m-okada/CPU2908/Schematics/74HC/RevC2/CPU2908C.sch

## KiCad design Schematics/74HC/RevC2/CPU2908C.sch (2020-01-18)

Schematic: CPU2908C.sch

Parts:
C1, C125, C126, C127: 10uF; C_0603_HandSoldering
C2, C3, C4, C5, C6, C7, C8, C9, C10: 0.1uF; C_0402
C124: 47uF; CP_Radial_D8.0mm_P2.50mm
D145, D146, D147, D160, D161: LED_G; LED_0402
J1: Conn_02x20_Odd_Even; Pin_Header_Straight_2x20_Pitch2.54mm
R146, R147, R170, R171, R172, R173, R174: 47K; R_0402
S0, S1: LED_G; LED_0402
U1, U2: 74HC08D; SOIC-14_W3.9mm
U3: TC74VHCT04AFT; TSSOP-14_4.4x5mm_Pitch0.65mm
U4, U7, U9: TC74VHC574F; SOIC-20_W7.5mm
U5, U6, U119: 74HC74; MC74HC74ADG
U8: TC74HC125; SN74HC11D
U117: TC74VHCT541; TSSOP-20_W4.4mm
U121: 74AHC1G32; TSOP-5_1.65x3.05mm_Pitch0.95mm
