m-okada/CPU2908/Schematics/74HC/RevC3/BROM.sch

## KiCad design Schematics/74HC/RevC3/BROM.sch (2020-06-03)

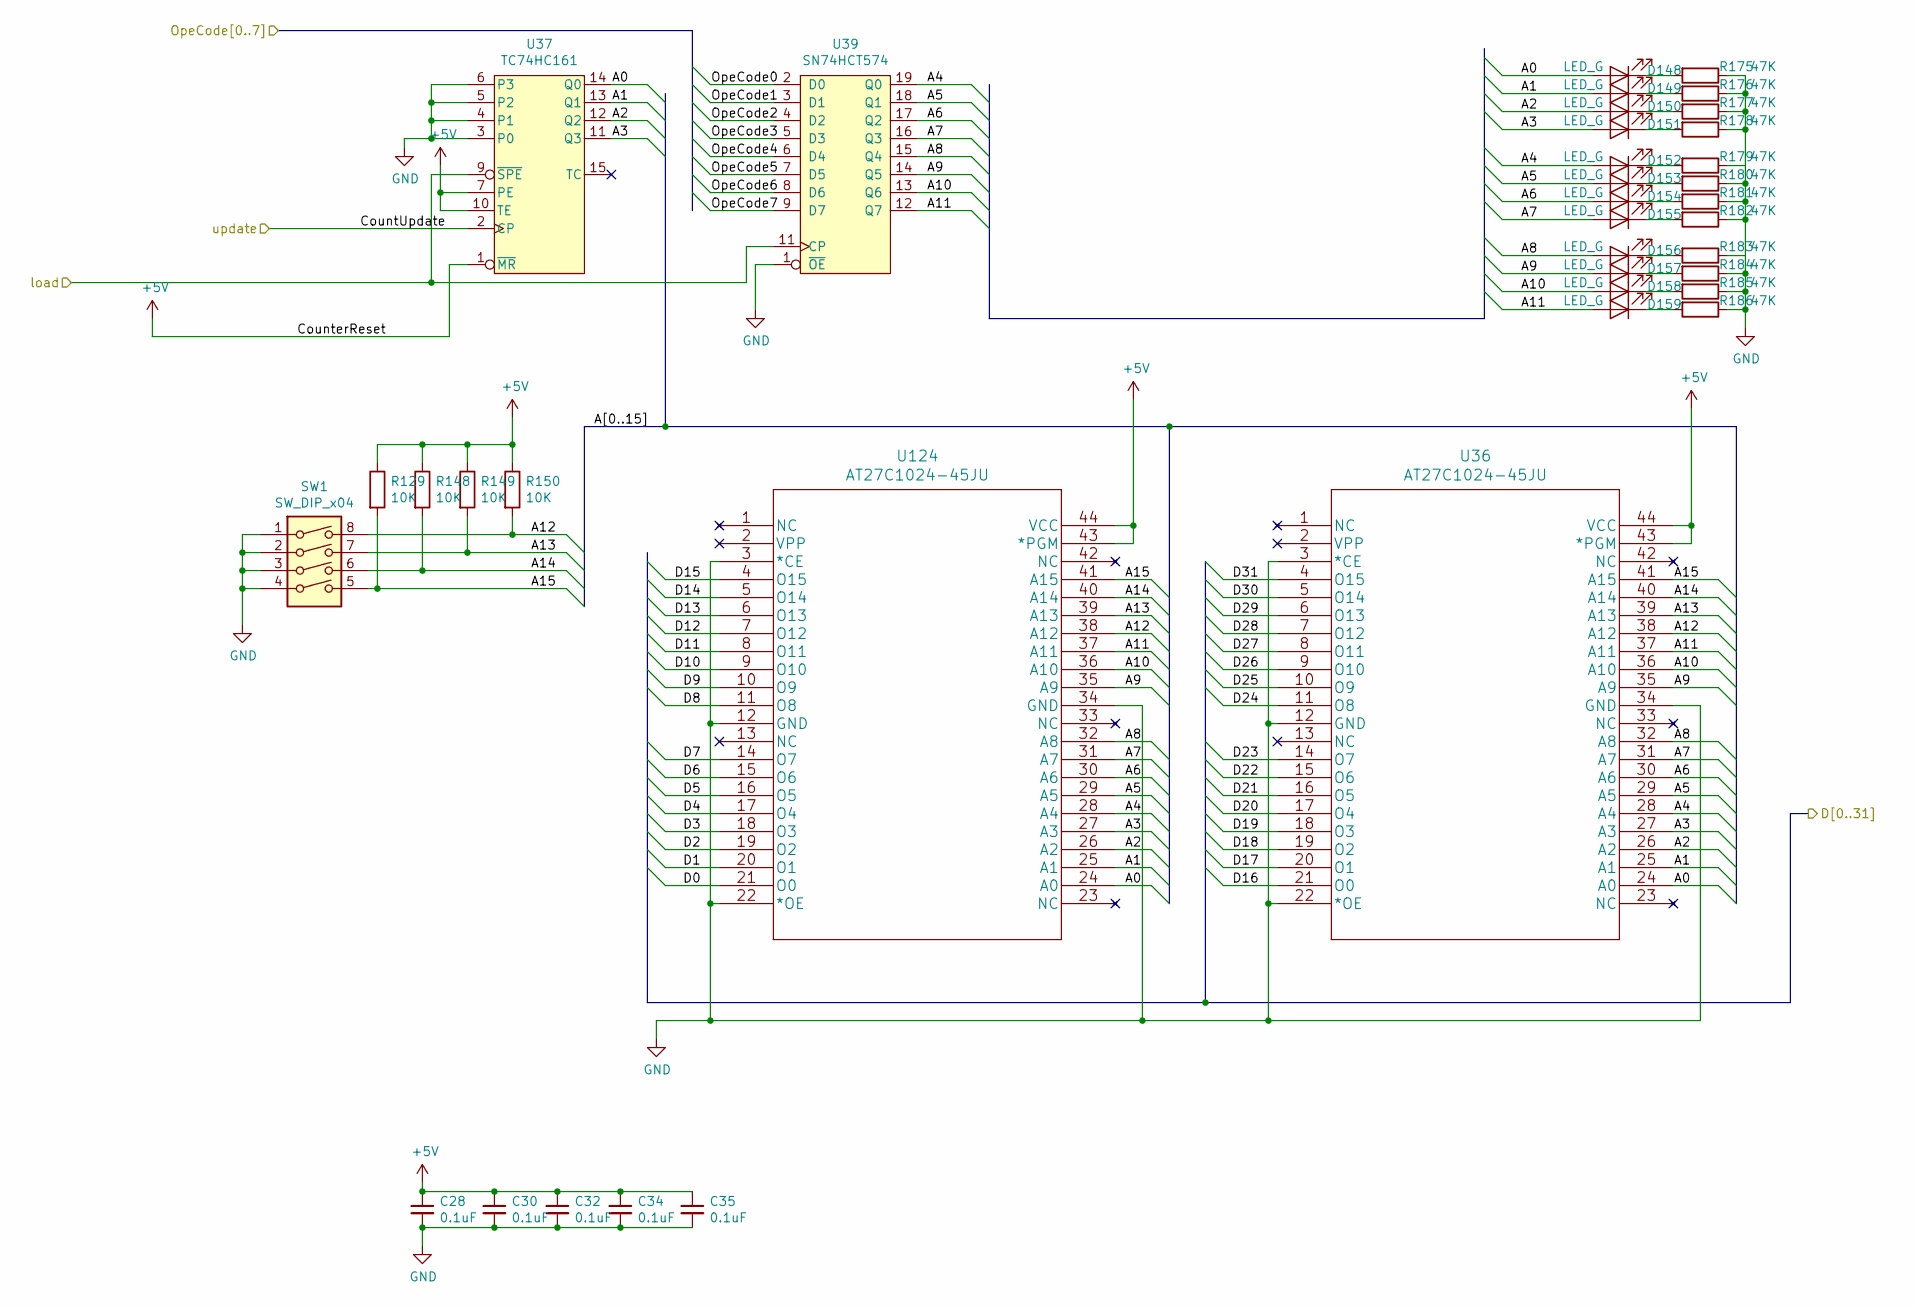
[picture p14: schematic BROM.sch]

Parts:
C28, C30, C32, C34, C35: 0.1uF; C_0402
D148, D149, D150, D151, D152, D153, D154, D155, D156, D157, D158, D159: LED_G; LED_0402
R129, R148, R149, R150: 10K; R_0402
R175, R176, R177, R178, R179, R180, R181, R182, R183, R184, R185, R186: 47K; R_0402
SW1: SW_DIP_x04; SW_DIP_x4_W7.62mm_Slide
U36, U124: AT27C1024-45JU; PLCC44
U37: TC74HC161; SOIC-16_W7.5mm
U39: SN74HCT574; SN74HCT574NSR

Connections:
+5V: C28.1, C30.1, C32.1, C34.1, C35.1, R129.1, R148.1, R149.1, R150.1, U36.43 (*PGM), U36.44 (VCC), U37.1 (~MR), U37.7 (PE), U37.10 (TE), U124.43 (*PGM), U124.44 (VCC)
A0: D148.2 (A), U36.24 (A0), U37.14 (Q0), U124.24 (A0)
A1: D149.2 (A), U36.25 (A1), U37.13 (Q1), U124.25 (A1)
A2: D150.2 (A), U36.26 (A2), U37.12 (Q2), U124.26 (A2)
A3: D151.2 (A), U36.27 (A3), U37.11 (Q3), U124.27 (A3)
A4: D152.2 (A), U36.28 (A4), U39.19 (Q0), U124.28 (A4)
A5: D153.2 (A), U36.29 (A5), U39.18 (Q1), U124.29 (A5)
A6: D154.2 (A), U36.30 (A6), U39.17 (Q2), U124.30 (A6)
A7: D155.2 (A), U36.31 (A7), U39.16 (Q3), U124.31 (A7)
A8: D156.2 (A), U36.32 (A8), U39.15 (Q4), U124.32 (A8)
A9: D157.2 (A), U36.35 (A9), U39.14 (Q5), U124.35 (A9)
A10: D158.2 (A), U36.36 (A10), U39.13 (Q6), U124.36 (A10)
A11: D159.2 (A), U36.37 (A11), U39.12 (Q7), U124.37 (A11)
A12: R150.2, SW1.8, U36.38 (A12), U124.38 (A12)
A13: R149.2, SW1.7, U36.39 (A13), U124.39 (A13)
A14: R148.2, SW1.6, U36.40 (A14), U124.40 (A14)
A15: R129.2, SW1.5, U36.41 (A15), U124.41 (A15)
CountUpdate: U37.2 (CP)
D0: U124.21 (O0)
D1: U124.20 (O1)
D2: U124.19 (O2)
D3: U124.18 (O3)
D4: U124.17 (O4)
D5: U124.16 (O5)
D6: U124.15 (O6)
D7: U124.14 (O7)
D8: U124.11 (O8)
D9: U124.10 (O9)
D10: U124.9 (O10)
D11: U124.8 (O11)
D12: U124.7 (O12)
D13: U124.6 (O13)
D14: U124.5 (O14)
D15: U124.4 (O15)
D16: U36.21 (O0)
D17: U36.20 (O1)
D18: U36.19 (O2)
D19: U36.18 (O3)
D20: U36.17 (O4)
D21: U36.16 (O5)
D22: U36.15 (O6)
D23: U36.14 (O7)
D24: U36.11 (O8)
D25: U36.10 (O9)
D26: U36.9 (O10)
D27: U36.8 (O11)
D28: U36.7 (O12)
D29: U36.6 (O13)
D30: U36.5 (O14)
D31: U36.4 (O15)
GND: C28.2, C30.2, C32.2, C34.2, C35.2, R175.1, R176.1, R177.1, R178.1, R179.1, R180.1, R181.1, R182.1, R183.1, R184.1, R185.1, R186.1, SW1.1, SW1.2, SW1.3, SW1.4, U36.3 (*CE), U36.12 (GND), U36.22 (*OE), U36.34 (GND), U37.3 (P0), U37.4 (P1), U37.5 (P2), U37.6 (P3), U39.1 (~OE), U124.3 (*CE), U124.12 (GND), U124.22 (*OE), U124.34 (GND)
unnamed: D148.1 (K), R175.2
unnamed: D149.1 (K), R176.2
unnamed: D150.1 (K), R177.2
unnamed: D151.1 (K), R178.2
unnamed: D152.1 (K), R179.2
unnamed: D153.1 (K), R180.2
unnamed: D154.1 (K), R181.2
unnamed: D155.1 (K), R182.2
unnamed: D156.1 (K), R183.2
unnamed: D157.1 (K), R184.2
unnamed: D158.1 (K), R185.2
unnamed: D159.1 (K), R186.2
OpeCode0: U39.2 (D0)
OpeCode1: U39.3 (D1)
OpeCode2: U39.4 (D2)
OpeCode3: U39.5 (D3)
OpeCode4: U39.6 (D4)
OpeCode5: U39.7 (D5)
OpeCode6: U39.8 (D6)
OpeCode7: U39.9 (D7)
load: U37.9 (~SPE), U39.11 (CP)
