m-okada/CPU2908/Schematics/74HC/RevC3/CPU2908Executer.sch

## KiCad design Schematics/74HC/RevC3/CPU2908Executer.sch (2020-06-03)

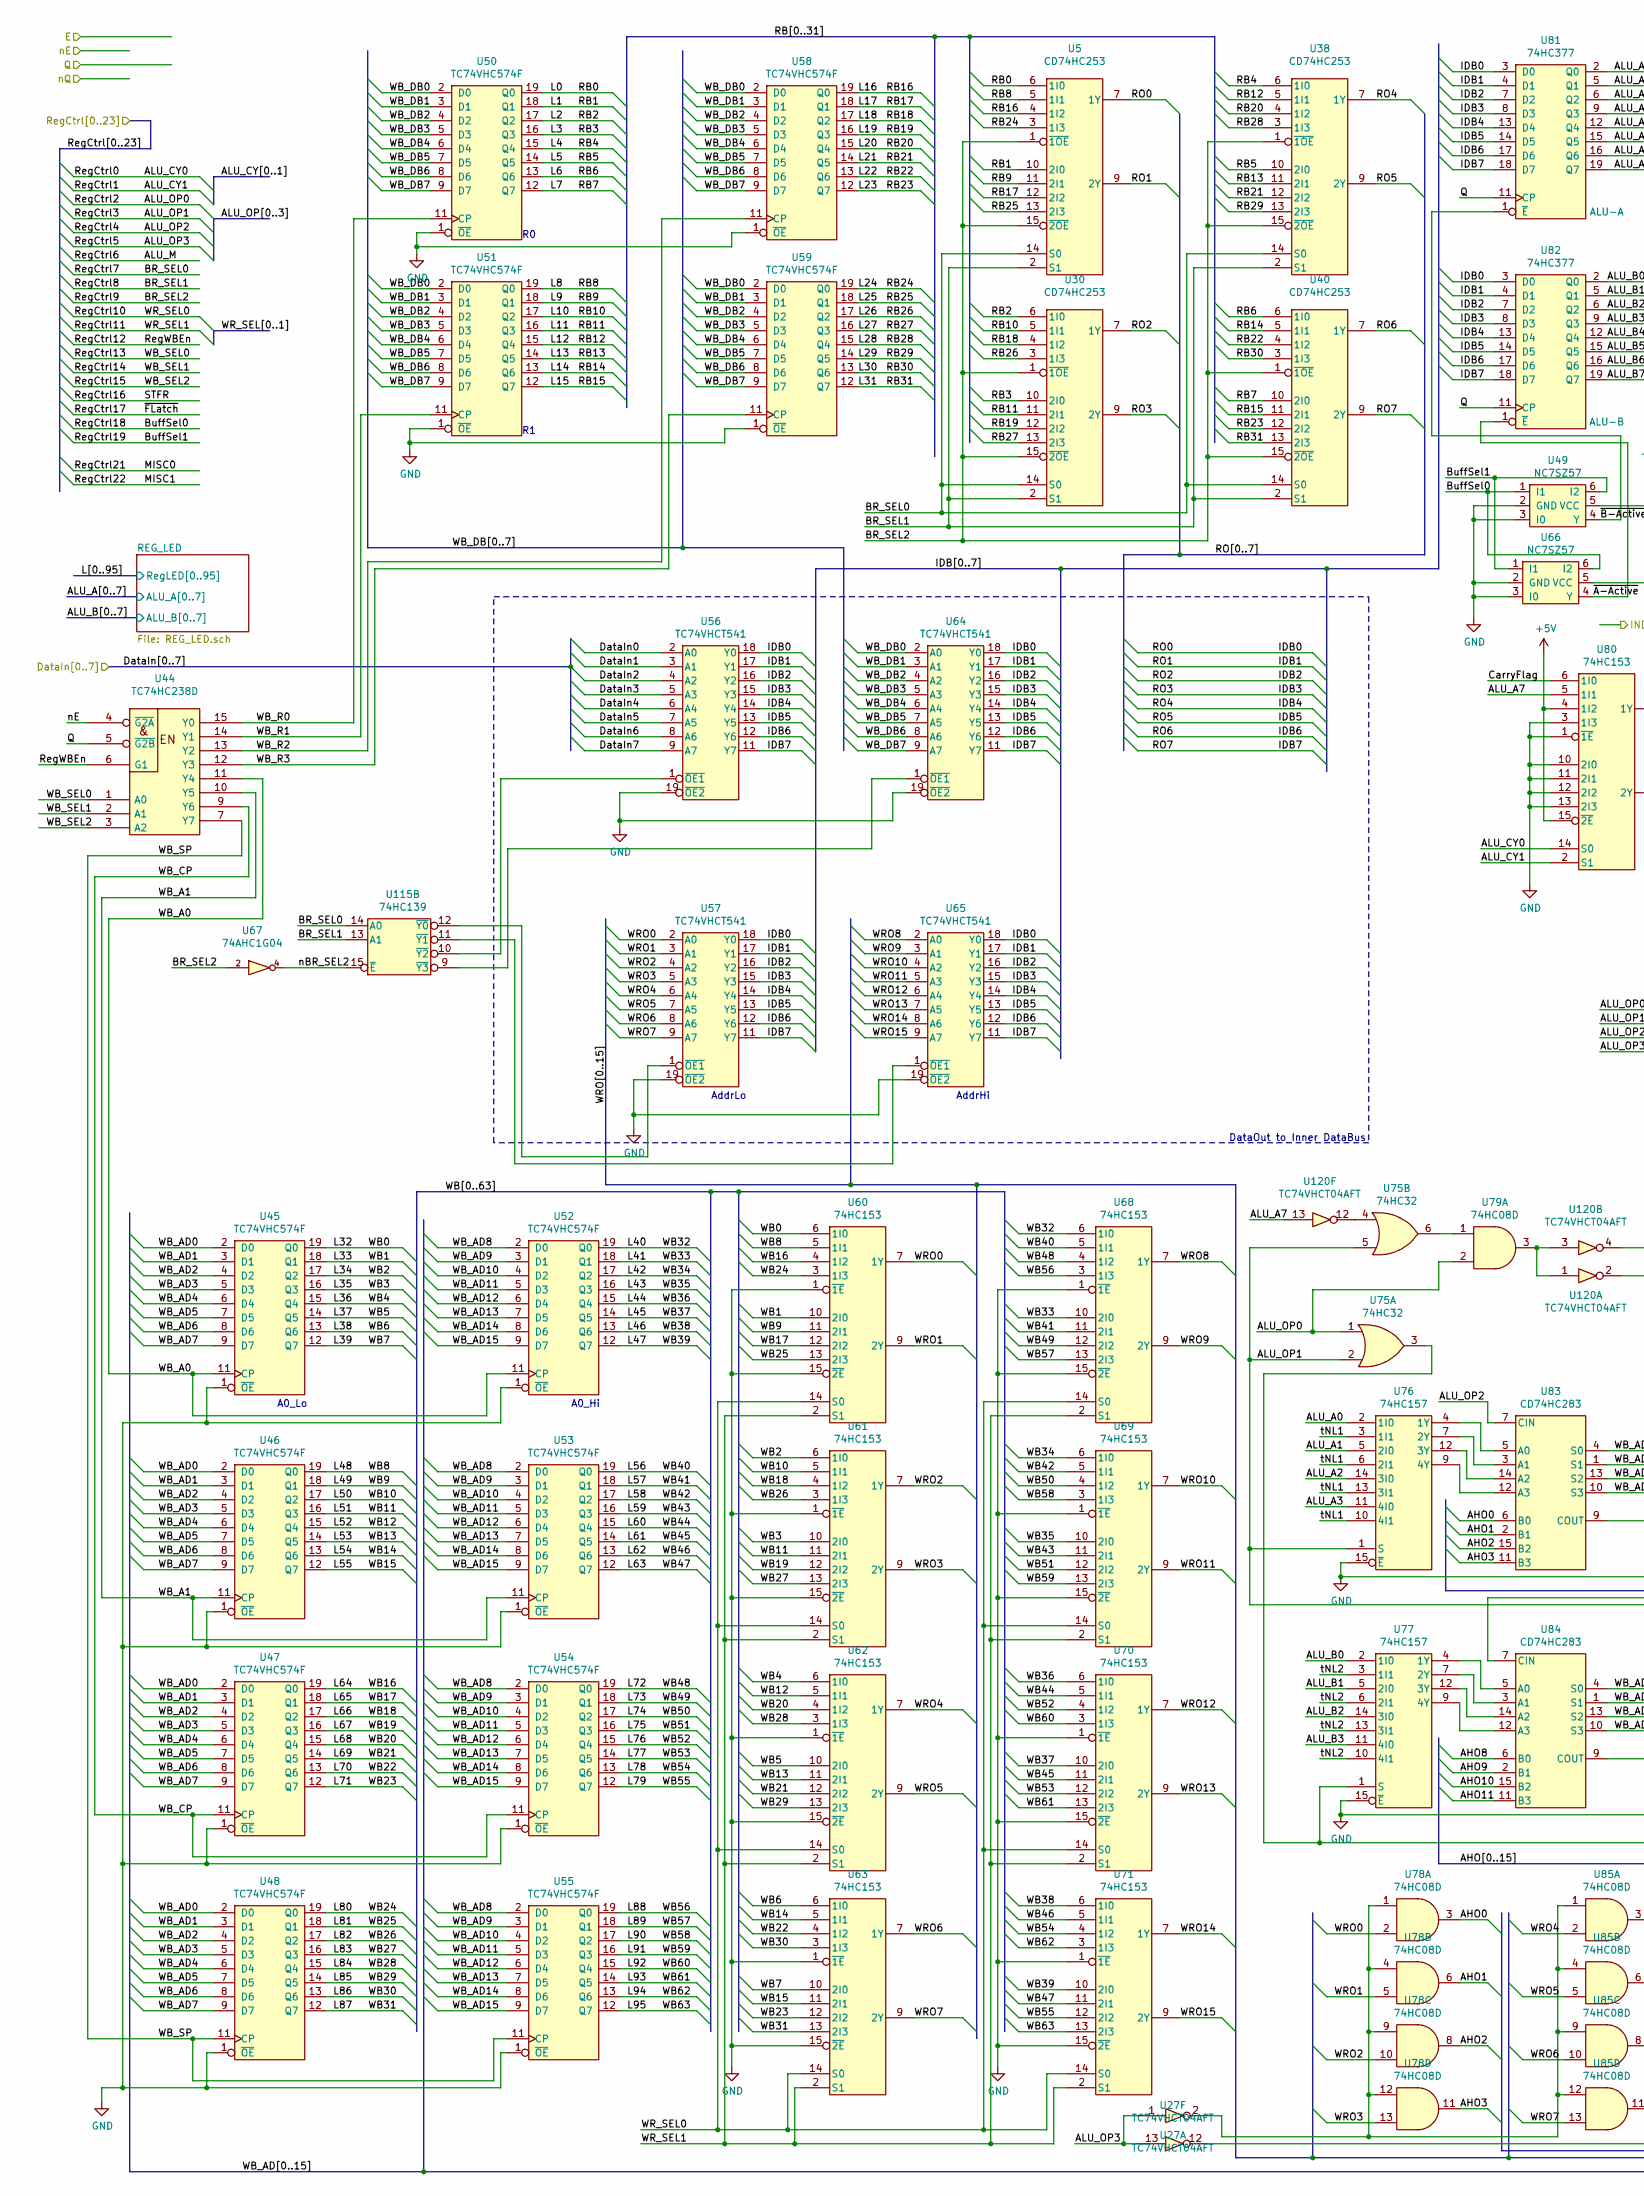
[picture p15: schematic CPU2908Executer.sch, part in row 1, column 1]

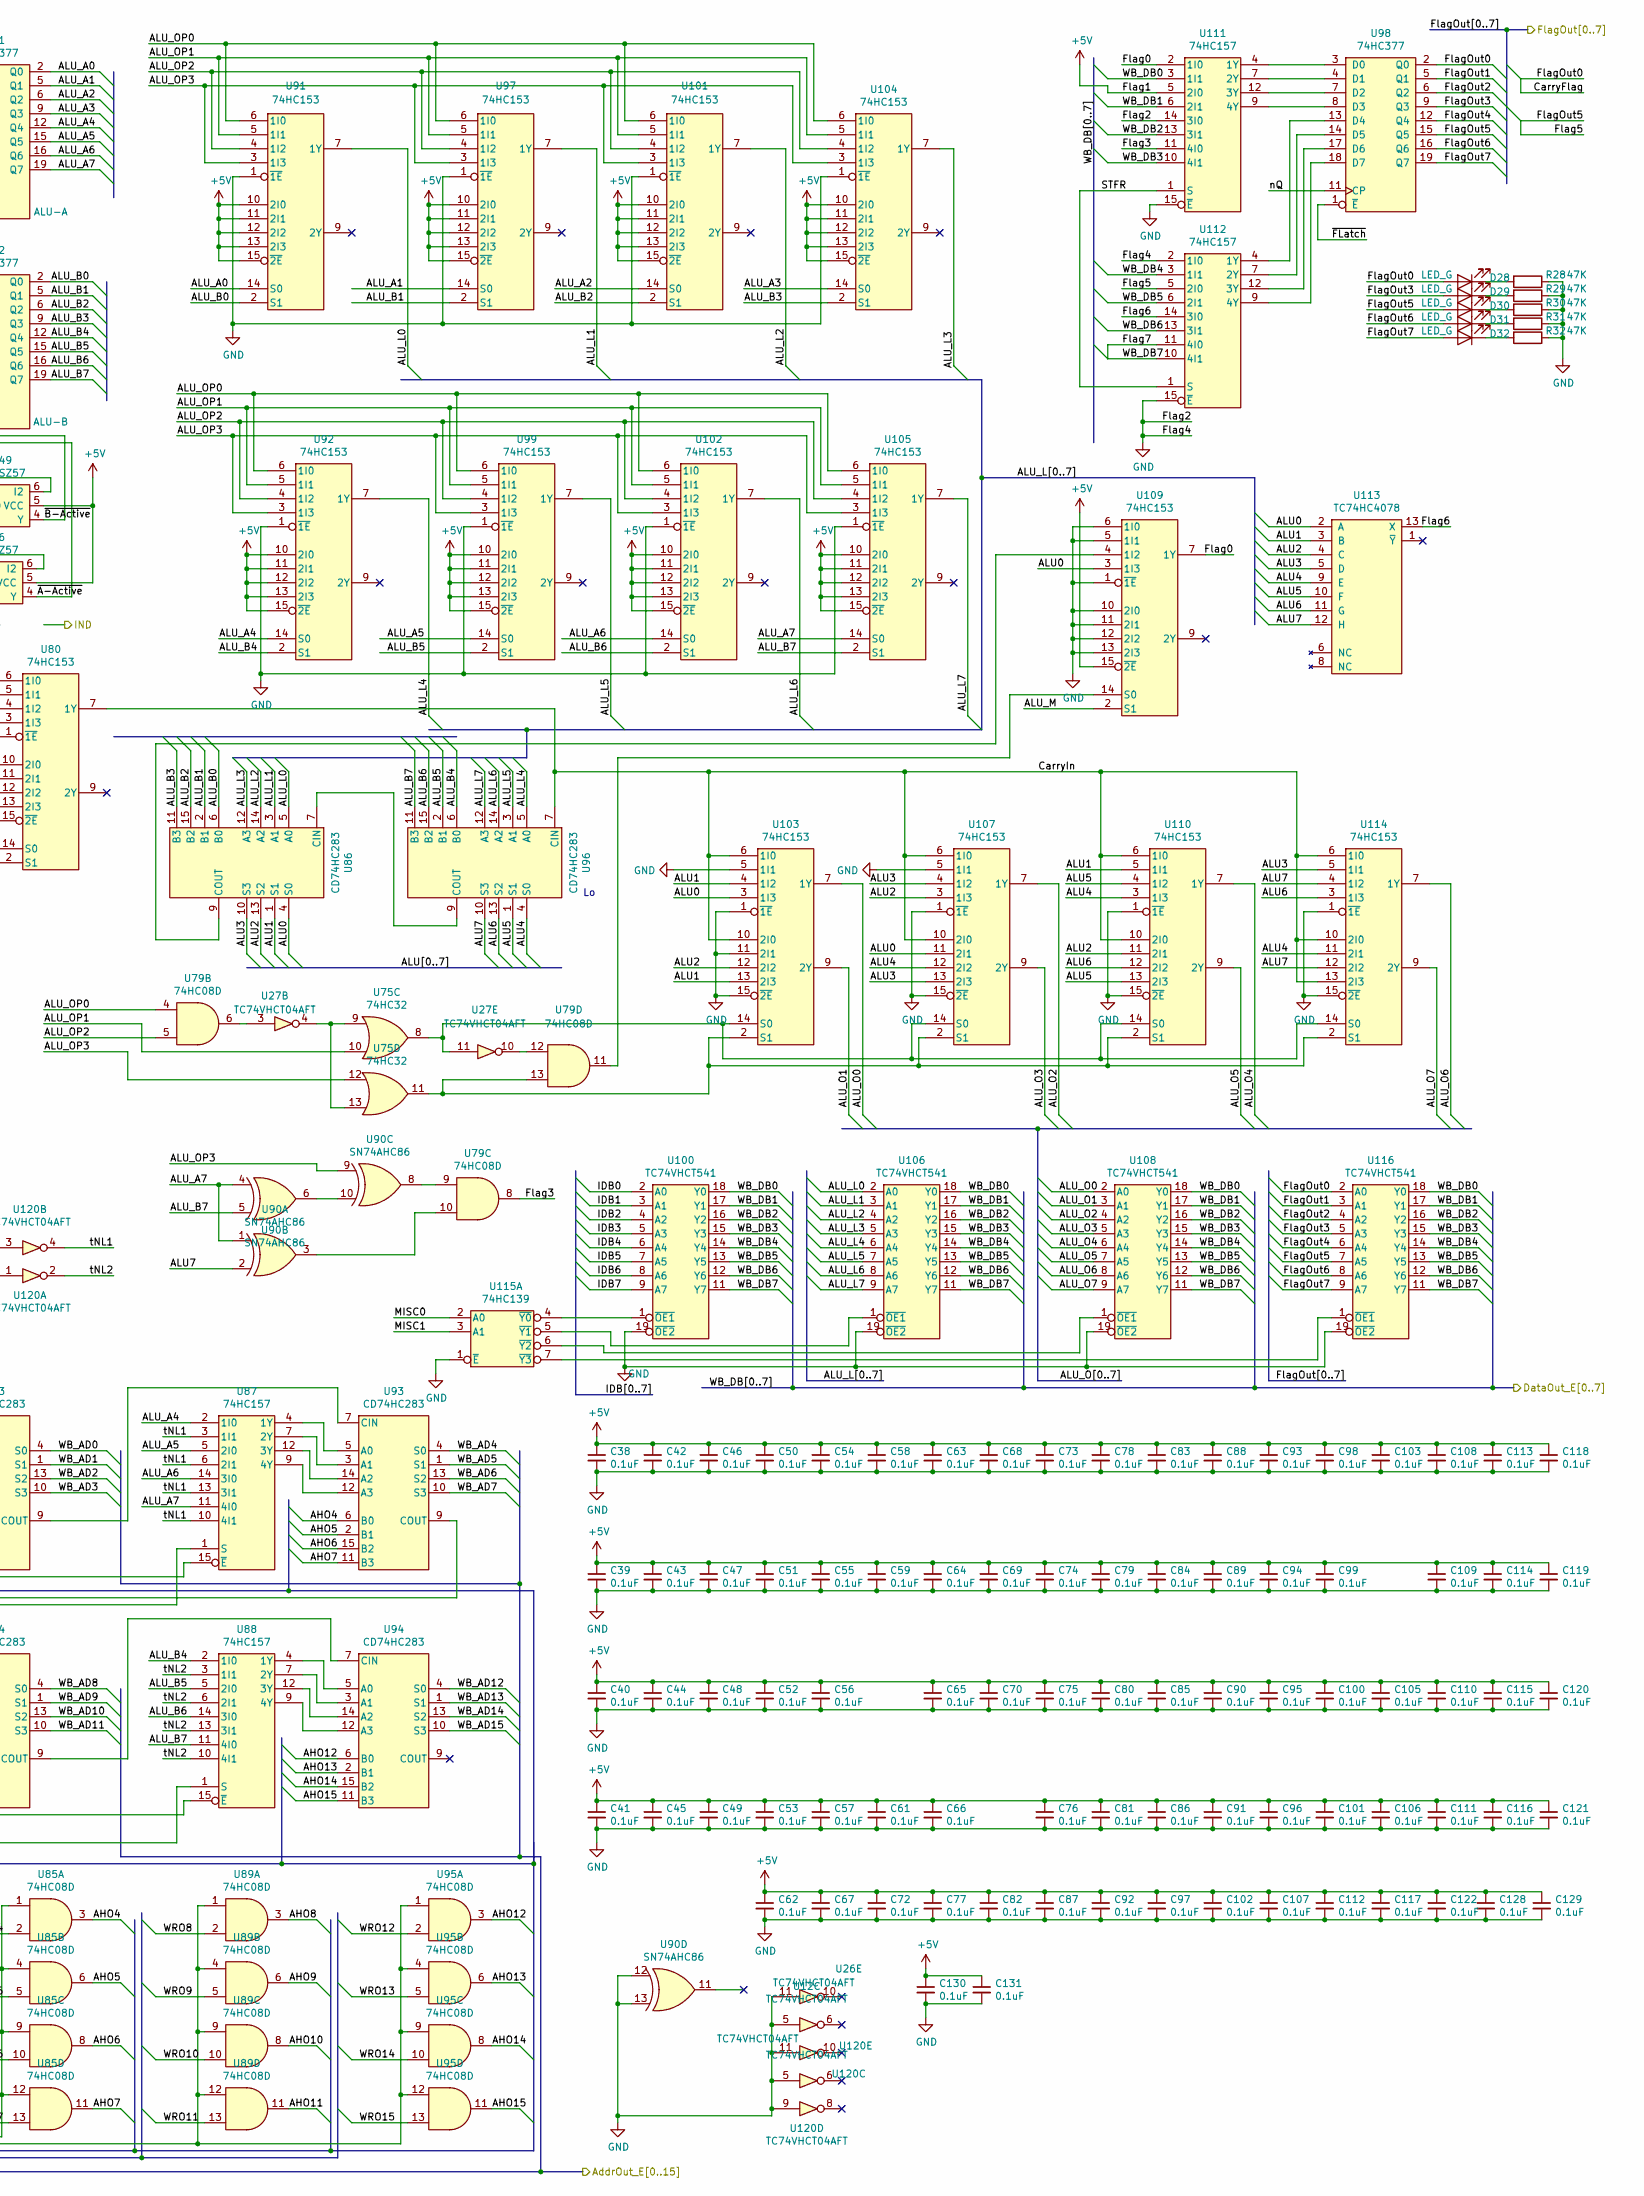
[picture p16: schematic CPU2908Executer.sch, part in row 1, column 2]

Parts:
C38, C39, C40, C41, C42, C43, C44, C45, C46, C47, C48, C49, C50, C51, C52, C53, C54, C55, C56, C57, C58, C59, C61, C62, C63, C64, C65, C66, C67, C68, C69, C70, C72, C73, C74, C75, C76, C77, C78, C79, C80, C81, C82, C83, C84, C85, C86, C87, C88, C89, C90, C91, C92, C93, C94, C95, C96, C97, C98, C99, C100, C101, C102, C103, C105, C106, C107, C108, C109, C110, C111, C112, C113, C114, C115, C116, C117, C118, C119, C120, C121, C122, C128, C129, C130, C131: 0.1uF; C_0402
D28, D29, D30, D31, D32: LED_G; LED_0402
R28, R29, R30, R31, R32: 47K; R_0402
U5, U30, U38, U40: CD74HC253; SOIC-16W_5.3x10.2mm_Pitch1.27mm
U12, U26, U27, U120: TC74VHCT04AFT; TSSOP-14_4.4x5mm_Pitch0.65mm
U44: TC74HC238D; 74HC238D
U45, U46, U47, U48, U50, U51, U52, U53, U54, U55, U58, U59: TC74VHC574F; SOIC-20_W7.5mm
U49, U66: NC7SZ57; SOT-363_SC-70-6_Handsoldering
U56, U57, U64, U65, U100, U106, U108, U116: TC74VHCT541; TSSOP-20_W4.4mm
U60, U61, U62, U63, U68, U69, U70, U71, U80, U91, U92, U97, U99, U101, U102, U103, U104, U105, U107, U109, U110, U114: 74HC153; SO-16-N
U67: 74AHC1G04; SOT-23-5
U75: 74HC32; SOIC-14_W3.9mm
U76, U77, U87, U88, U111, U112: 74HC157; SN74HC157DR
U78, U79, U85, U89, U95: 74HC08D; SOIC-14_W3.9mm
U81, U82, U98: 74HC377; SN74HC377NSR
U83, U84, U86, U93, U94, U96: CD74HC283; CD74HC283M96
U90: SN74AHC86; SN74AHC86D
U113: TC74HC4078; SN74HC11D
U115: 74HC139; MC74HC139ADR2G

Connections:
+5V: C38.1, C39.1, C40.1, C41.1, C42.1, C43.1, C44.1, C45.1, C46.1, C47.1, C48.1, C49.1, C50.1, C51.1, C52.1, C53.1, C54.1, C55.1, C56.1, C57.1, C58.1, C59.1, C61.1, C62.1, C63.1, C64.1, C65.1, C66.1, C67.1, C68.1, C69.1, C70.1, C72.1, C73.1, C74.1, C75.1, C76.1, C77.1, C78.1, C79.1, C80.1, C81.1, C82.1, C83.1, C84.1, C85.1, C86.1, C87.1, C88.1, C89.1, C90.1, C91.1, C92.1, C93.1, C94.1, C95.1, C96.1, C97.1, C98.1, C99.1, C100.1, C101.1, C102.1, C103.1, C105.1, C106.1, C107.1, C108.1, C109.1, C110.1, C111.1, C112.1, C113.1, C114.1, C115.1, C116.1, C117.1, C118.1, C119.1, C120.1, C121.1, C122.1, C128.1, C129.1, C130.1, C131.1, U49.5 (VCC), U66.5 (VCC), U80.4 (1I2), U80.15 (~2E), U91.10 (2I0), U91.11 (2I1), U91.12 (2I2), U91.13 (2I3), U91.15 (~2E), U92.10 (2I0), U92.11 (2I1), U92.12 (2I2), U92.13 (2I3), U92.15 (~2E), U97.10 (2I0), U97.11 (2I1), U97.12 (2I2), U97.13 (2I3), U97.15 (~2E), U99.10 (2I0), U99.11 (2I1), U99.12 (2I2), U99.13 (2I3), U99.15 (~2E), U101.10 (2I0), U101.11 (2I1), U101.12 (2I2), U101.13 (2I3), U101.15 (~2E), U102.10 (2I0), U102.11 (2I1), U102.12 (2I2), U102.13 (2I3), U102.15 (~2E), U104.10 (2I0), U104.11 (2I1), U104.12 (2I2), U104.13 (2I3), U104.15 (~2E), U105.10 (2I0), U105.11 (2I1), U105.12 (2I2), U105.13 (2I3), U105.15 (~2E), U109.15 (~2E), U111.5 (2I0)
AHO0: U78.3, U83.6 (B0)
AHO1: U78.6, U83.2 (B1)
AHO2: U78.8, U83.15 (B2)
AHO3: U78.11, U83.11 (B3)
AHO4: U85.3, U93.6 (B0)
AHO5: U85.6, U93.2 (B1)
AHO6: U85.8, U93.15 (B2)
AHO7: U85.11, U93.11 (B3)
AHO8: U84.6 (B0), U89.3
AHO9: U84.2 (B1), U89.6
AHO10: U84.15 (B2), U89.8
AHO11: U84.11 (B3), U89.11
AHO12: U94.6 (B0), U95.3
AHO13: U94.2 (B1), U95.6
AHO14: U94.15 (B2), U95.8
AHO15: U94.11 (B3), U95.11
ALU0: U86.4 (S0), U103.3 (1I3), U107.11 (2I1), U109.3 (1I3), U113.2 (A)
ALU1: U86.1 (S1), U103.4 (1I2), U103.13 (2I3), U110.5 (1I1), U113.3 (B)
ALU2: U86.13 (S2), U103.12 (2I2), U107.3 (1I3), U110.11 (2I1), U113.4 (C)
ALU3: U86.10 (S3), U107.4 (1I2), U107.13 (2I3), U113.5 (D), U114.5 (1I1)
ALU4: U96.4 (S0), U107.12 (2I2), U110.3 (1I3), U113.9 (E), U114.11 (2I1)
ALU5: U96.1 (S1), U110.4 (1I2), U110.13 (2I3), U113.10 (F)
ALU6: U96.13 (S2), U110.12 (2I2), U113.11 (G), U114.3 (1I3)
ALU7: U90.2, U96.10 (S3), U113.12 (H), U114.4 (1I2), U114.12 (2I2)
ALU_A0: U76.2 (1I0), U81.2 (Q0), U91.14 (S0)
ALU_A1: U76.5 (2I0), U81.5 (Q1), U97.14 (S0)
ALU_A2: U76.14 (3I0), U81.6 (Q2), U101.14 (S0)
ALU_A3: U76.11 (4I0), U81.9 (Q3), U104.14 (S0)
ALU_A4: U81.12 (Q4), U87.2 (1I0), U92.14 (S0)
ALU_A5: U81.15 (Q5), U87.5 (2I0), U99.14 (S0)
ALU_A6: U81.16 (Q6), U87.14 (3I0), U102.14 (S0)
ALU_A7: U80.5 (1I1), U81.19 (Q7), U87.11 (4I0), U90.1, U90.4, U105.14 (S0), U120.13
ALU_B0: U77.2 (1I0), U82.2 (Q0), U86.6 (B0), U91.2 (S1)
ALU_B1: U77.5 (2I0), U82.5 (Q1), U86.2 (B1), U97.2 (S1)
ALU_B2: U77.14 (3I0), U82.6 (Q2), U86.15 (B2), U101.2 (S1)
ALU_B3: U77.11 (4I0), U82.9 (Q3), U86.11 (B3), U104.2 (S1)
ALU_B4: U82.12 (Q4), U88.2 (1I0), U92.2 (S1), U96.6 (B0)
ALU_B5: U82.15 (Q5), U88.5 (2I0), U96.2 (B1), U99.2 (S1)
ALU_B6: U82.16 (Q6), U88.14 (3I0), U96.15 (B2), U102.2 (S1)
ALU_B7: U82.19 (Q7), U88.11 (4I0), U90.5, U96.11 (B3), U105.2 (S1)
ALU_CY0: U80.14 (S0)
ALU_CY1: U80.2 (S1)
ALU_L0: U86.5 (A0), U91.7 (1Y), U106.2 (A0)
ALU_L1: U86.3 (A1), U97.7 (1Y), U106.3 (A1)
ALU_L2: U86.14 (A2), U101.7 (1Y), U106.4 (A2)
ALU_L3: U86.12 (A3), U104.7 (1Y), U106.5 (A3)
ALU_L4: U92.7 (1Y), U96.5 (A0), U106.6 (A4)
ALU_L5: U96.3 (A1), U99.7 (1Y), U106.7 (A5)
ALU_L6: U96.14 (A2), U102.7 (1Y), U106.8 (A6)
ALU_L7: U96.12 (A3), U105.7 (1Y), U106.9 (A7)
ALU_M: U109.2 (S1)
ALU_O0: U103.7 (1Y), U108.2 (A0)
ALU_O1: U103.9 (2Y), U108.3 (A1)
ALU_O2: U107.7 (1Y), U108.4 (A2)
ALU_O3: U107.9 (2Y), U108.5 (A3)
ALU_O4: U108.6 (A4), U110.7 (1Y)
ALU_O5: U108.7 (A5), U110.9 (2Y)
ALU_O6: U108.8 (A6), U114.7 (1Y)
ALU_O7: U108.9 (A7), U114.9 (2Y)
ALU_OP0: U75.1, U79.2, U79.4, U91.6 (1I0), U92.6 (1I0), U97.6 (1I0), U99.6 (1I0), U101.6 (1I0), U102.6 (1I0), U104.6 (1I0), U105.6 (1I0)
ALU_OP1: U75.2, U75.5, U75.10, U76.1 (S), U87.1 (S), U91.5 (1I1), U92.5 (1I1), U97.5 (1I1), U99.5 (1I1), U101.5 (1I1), U102.5 (1I1), U104.5 (1I1), U105.5 (1I1)
ALU_OP2: U79.5, U83.7 (CIN), U91.4 (1I2), U92.4 (1I2), U97.4 (1I2), U99.4 (1I2), U101.4 (1I2), U102.4 (1I2), U104.4 (1I2), U105.4 (1I2)
ALU_OP3: U27.1, U27.13, U75.12, U90.9, U91.3 (1I3), U92.3 (1I3), U97.3 (1I3), U99.3 (1I3), U101.3 (1I3), U102.3 (1I3), U104.3 (1I3), U105.3 (1I3)
BR_SEL0: U5.14 (S0), U30.14 (S0), U38.14 (S0), U40.14 (S0), U115.14 (A0)
BR_SEL1: U5.2 (S1), U30.2 (S1), U38.2 (S1), U40.2 (S1), U115.13 (A1)
BR_SEL2: U5.1 (~1OE), U5.15 (~2OE), U30.1 (~1OE), U30.15 (~2OE), U38.1 (~1OE), U38.15 (~2OE), U40.1 (~1OE), U40.15 (~2OE), U67.2
BuffSel0: U49.1 (I1), U66.6 (I2)
BuffSel1: U49.6 (I2), U66.1 (I1)
CarryFlag: D28.2 (A), U80.6 (1I0), U98.2 (Q0), U116.2 (A0)
CarryIn: U80.7 (1Y), U96.7 (CIN), U103.6 (1I0), U103.10 (2I0), U107.6 (1I0), U107.10 (2I0), U110.6 (1I0), U110.10 (2I0), U114.6 (1I0), U114.10 (2I0), U114.13 (2I3)
DataIn0: U56.2 (A0)
DataIn1: U56.3 (A1)
DataIn2: U56.4 (A2)
DataIn3: U56.5 (A3)
DataIn4: U56.6 (A4)
DataIn5: U56.7 (A5)
DataIn6: U56.8 (A6)
DataIn7: U56.9 (A7)
Flag0: U109.7 (1Y), U111.2 (1I0)
Flag3: U79.8, U111.11 (4I0)
Flag5: D30.2 (A), U98.15 (Q5), U112.5 (2I0), U116.7 (A5)
Flag6: U112.14 (3I0), U113.13 (X)
Flag7: U50.9 (D7), U51.9 (D7), U58.9 (D7), U59.9 (D7), U64.9 (A7), U100.11 (Y7), U106.11 (Y7), U108.11 (Y7), U112.10 (4I1), U112.11 (4I0), U116.11 (Y7)
FlagOut1: U98.5 (Q1), U116.3 (A1)
FlagOut2: U98.6 (Q2), U116.4 (A2)
FlagOut3: D29.2 (A), U98.9 (Q3), U116.5 (A3)
FlagOut4: U98.12 (Q4), U116.6 (A4)
FlagOut6: D31.2 (A), U98.16 (Q6), U116.8 (A6)
FlagOut7: D32.2 (A), U98.19 (Q7), U116.9 (A7)
GND: C38.2, C39.2, C40.2, C41.2, C42.2, C43.2, C44.2, C45.2, C46.2, C47.2, C48.2, C49.2, C50.2, C51.2, C52.2, C53.2, C54.2, C55.2, C56.2, C57.2, C58.2, C59.2, C61.2, C62.2, C63.2, C64.2, C65.2, C66.2, C67.2, C68.2, C69.2, C70.2, C72.2, C73.2, C74.2, C75.2, C76.2, C77.2, C78.2, C79.2, C80.2, C81.2, C82.2, C83.2, C84.2, C85.2, C86.2, C87.2, C88.2, C89.2, C90.2, C91.2, C92.2, C93.2, C94.2, C95.2, C96.2, C97.2, C98.2, C99.2, C100.2, C101.2, C102.2, C103.2, C105.2, C106.2, C107.2, C108.2, C109.2, C110.2, C111.2, C112.2, C113.2, C114.2, C115.2, C116.2, C117.2, C118.2, C119.2, C120.2, C121.2, C122.2, C128.2, C129.2, C130.2, C131.2, R28.1, R29.1, R30.1, R31.1, R32.1, U12.5, U26.11, U45.1 (~OE), U46.1 (~OE), U47.1 (~OE), U48.1 (~OE), U49.2 (GND), U49.3 (I0), U50.1 (~OE), U51.1 (~OE), U52.1 (~OE), U53.1 (~OE), U54.1 (~OE), U55.1 (~OE), U56.19 (~OE2), U57.19 (~OE2), U58.1 (~OE), U59.1 (~OE), U60.1 (~1E), U60.15 (~2E), U61.1 (~1E), U61.15 (~2E), U62.1 (~1E), U62.15 (~2E), U63.1 (~1E), U63.15 (~2E), U64.19 (~OE2), U65.19 (~OE2), U66.2 (GND), U66.3 (I0), U68.1 (~1E), U68.15 (~2E), U69.1 (~1E), U69.15 (~2E), U70.1 (~1E), U70.15 (~2E), U71.1 (~1E), U71.15 (~2E), U76.15 (~E), U77.15 (~E), U80.1 (~1E), U80.3 (1I3), U80.10 (2I0), U80.11 (2I1), U80.12 (2I2), U80.13 (2I3), U87.15 (~E), U88.15 (~E), U90.12, U90.13, U91.1 (~1E), U92.1 (~1E), U97.1 (~1E), U99.1 (~1E), U100.19 (~OE2), U101.1 (~1E), U102.1 (~1E), U103.1 (~1E), U103.5 (1I1), U103.11 (2I1), U103.15 (~2E), U104.1 (~1E), U105.1 (~1E), U106.19 (~OE2), U107.1 (~1E), U107.5 (1I1), U107.15 (~2E), U108.19 (~OE2), U109.1 (~1E), U109.5 (1I1), U109.6 (1I0), U109.10 (2I0), U109.11 (2I1), U109.12 (2I2), U109.13 (2I3), U110.1 (~1E), U110.15 (~2E), U111.14 (3I0), U111.15 (~E), U112.2 (1I0), U112.15 (~E), U114.1 (~1E), U114.15 (~2E), U115.1 (~E), U116.19 (~OE2), U120.5, U120.9, U120.11
IDB0: U5.7 (1Y), U56.18 (Y0), U57.18 (Y0), U64.18 (Y0), U65.18 (Y0), U81.3 (D0), U82.3 (D0), U100.2 (A0)
IDB1: U5.9 (2Y), U56.17 (Y1), U57.17 (Y1), U64.17 (Y1), U65.17 (Y1), U81.4 (D1), U82.4 (D1), U100.3 (A1)
IDB2: U30.7 (1Y), U56.16 (Y2), U57.16 (Y2), U64.16 (Y2), U65.16 (Y2), U81.7 (D2), U82.7 (D2), U100.4 (A2)
IDB3: U30.9 (2Y), U56.15 (Y3), U57.15 (Y3), U64.15 (Y3), U65.15 (Y3), U81.8 (D3), U82.8 (D3), U100.5 (A3)
IDB4: U38.7 (1Y), U56.14 (Y4), U57.14 (Y4), U64.14 (Y4), U65.14 (Y4), U81.13 (D4), U82.13 (D4), U100.6 (A4)
IDB5: U38.9 (2Y), U56.13 (Y5), U57.13 (Y5), U64.13 (Y5), U65.13 (Y5), U81.14 (D5), U82.14 (D5), U100.7 (A5)
IDB6: U40.7 (1Y), U56.12 (Y6), U57.12 (Y6), U64.12 (Y6), U65.12 (Y6), U81.17 (D6), U82.17 (D6), U100.8 (A6)
IDB7: U40.9 (2Y), U56.11 (Y7), U57.11 (Y7), U64.11 (Y7), U65.11 (Y7), U81.18 (D7), U82.18 (D7), U100.9 (A7)
L0: U5.6 (1I0), U50.19 (Q0)
L1: U5.10 (2I0), U50.18 (Q1)
L2: U30.6 (1I0), U50.17 (Q2)
L3: U30.10 (2I0), U50.16 (Q3)
L4: U38.6 (1I0), U50.15 (Q4)
L5: U38.10 (2I0), U50.14 (Q5)
L6: U40.6 (1I0), U50.13 (Q6)
L7: U40.10 (2I0), U50.12 (Q7)
L8: U5.5 (1I1), U51.19 (Q0)
L9: U5.11 (2I1), U51.18 (Q1)
L10: U30.5 (1I1), U51.17 (Q2)
L11: U30.11 (2I1), U51.16 (Q3)
L12: U38.5 (1I1), U51.15 (Q4)
L13: U38.11 (2I1), U51.14 (Q5)
L14: U40.5 (1I1), U51.13 (Q6)
L15: U40.11 (2I1), U51.12 (Q7)
L16: U5.4 (1I2), U58.19 (Q0)
L17: U5.12 (2I2), U58.18 (Q1)
L18: U30.4 (1I2), U58.17 (Q2)
L19: U30.12 (2I2), U58.16 (Q3)
L20: U38.4 (1I2), U58.15 (Q4)
L21: U38.12 (2I2), U58.14 (Q5)
L22: U40.4 (1I2), U58.13 (Q6)
L23: U40.12 (2I2), U58.12 (Q7)
L24: U5.3 (1I3), U59.19 (Q0)
L25: U5.13 (2I3), U59.18 (Q1)
L26: U30.3 (1I3), U59.17 (Q2)
L27: U30.13 (2I3), U59.16 (Q3)
L28: U38.3 (1I3), U59.15 (Q4)
L29: U38.13 (2I3), U59.14 (Q5)
L30: U40.3 (1I3), U59.13 (Q6)
L31: U40.13 (2I3), U59.12 (Q7)
L32: U45.19 (Q0), U60.6 (1I0)
L33: U45.18 (Q1), U60.10 (2I0)
L34: U45.17 (Q2), U61.6 (1I0)
L35: U45.16 (Q3), U61.10 (2I0)
L36: U45.15 (Q4), U62.6 (1I0)
L37: U45.14 (Q5), U62.10 (2I0)
L38: U45.13 (Q6), U63.6 (1I0)
L39: U45.12 (Q7), U63.10 (2I0)
L40: U52.19 (Q0), U68.6 (1I0)
L41: U52.18 (Q1), U68.10 (2I0)
L42: U52.17 (Q2), U69.6 (1I0)
L43: U52.16 (Q3), U69.10 (2I0)
L44: U52.15 (Q4), U70.6 (1I0)
L45: U52.14 (Q5), U70.10 (2I0)
L46: U52.13 (Q6), U71.6 (1I0)
L47: U52.12 (Q7), U71.10 (2I0)
L48: U46.19 (Q0), U60.5 (1I1)
L49: U46.18 (Q1), U60.11 (2I1)
L50: U46.17 (Q2), U61.5 (1I1)
L51: U46.16 (Q3), U61.11 (2I1)
L52: U46.15 (Q4), U62.5 (1I1)
L53: U46.14 (Q5), U62.11 (2I1)
L54: U46.13 (Q6), U63.5 (1I1)
L55: U46.12 (Q7), U63.11 (2I1)
L56: U53.19 (Q0), U68.5 (1I1)
L57: U53.18 (Q1), U68.11 (2I1)
L58: U53.17 (Q2), U69.5 (1I1)
L59: U53.16 (Q3), U69.11 (2I1)
L60: U53.15 (Q4), U70.5 (1I1)
L61: U53.14 (Q5), U70.11 (2I1)
L62: U53.13 (Q6), U71.5 (1I1)
L63: U53.12 (Q7), U71.11 (2I1)
L64: U47.19 (Q0), U60.4 (1I2)
L65: U47.18 (Q1), U60.12 (2I2)
L66: U47.17 (Q2), U61.4 (1I2)
L67: U47.16 (Q3), U61.12 (2I2)
L68: U47.15 (Q4), U62.4 (1I2)
L69: U47.14 (Q5), U62.12 (2I2)
L70: U47.13 (Q6), U63.4 (1I2)
L71: U47.12 (Q7), U63.12 (2I2)
L72: U54.19 (Q0), U68.4 (1I2)
L73: U54.18 (Q1), U68.12 (2I2)
L74: U54.17 (Q2), U69.4 (1I2)
L75: U54.16 (Q3), U69.12 (2I2)
L76: U54.15 (Q4), U70.4 (1I2)
L77: U54.14 (Q5), U70.12 (2I2)
L78: U54.13 (Q6), U71.4 (1I2)
L79: U54.12 (Q7), U71.12 (2I2)
L80: U48.19 (Q0), U60.3 (1I3)
L81: U48.18 (Q1), U60.13 (2I3)
L82: U48.17 (Q2), U61.3 (1I3)
L83: U48.16 (Q3), U61.13 (2I3)
L84: U48.15 (Q4), U62.3 (1I3)
L85: U48.14 (Q5), U62.13 (2I3)
L86: U48.13 (Q6), U63.3 (1I3)
L87: U48.12 (Q7), U63.13 (2I3)
L88: U55.19 (Q0), U68.3 (1I3)
L89: U55.18 (Q1), U68.13 (2I3)
L90: U55.17 (Q2), U69.3 (1I3)
L91: U55.16 (Q3), U69.13 (2I3)
L92: U55.15 (Q4), U70.3 (1I3)
L93: U55.14 (Q5), U70.13 (2I3)
L94: U55.13 (Q6), U71.3 (1I3)
L95: U55.12 (Q7), U71.13 (2I3)
MISC0: U115.2 (A0)
MISC1: U115.3 (A1)
unnamed: D28.1 (K), R28.2
unnamed: D29.1 (K), R29.2
unnamed: D30.1 (K), R30.2
unnamed: D31.1 (K), R31.2
unnamed: D32.1 (K), R32.2
unnamed: U27.2, U78.1, U78.4, U78.9, U78.12, U85.1, U85.4, U85.9, U85.12
unnamed: U27.3, U79.6
unnamed: U27.4, U75.9, U75.13
unnamed: U27.10, U79.12
unnamed: U27.12, U89.1, U89.4, U89.9, U89.12, U95.1, U95.4, U95.9, U95.12
unnamed: U75.3, U77.1 (S), U88.1 (S)
unnamed: U75.6, U79.1
unnamed: U76.4 (1Y), U83.5 (A0)
unnamed: U76.7 (2Y), U83.3 (A1)
unnamed: U76.9 (4Y), U83.12 (A3)
unnamed: U76.12 (3Y), U83.14 (A2)
unnamed: U77.4 (1Y), U84.5 (A0)
unnamed: U77.7 (2Y), U84.3 (A1)
unnamed: U77.9 (4Y), U84.12 (A3)
unnamed: U77.12 (3Y), U84.14 (A2)
unnamed: U79.9, U90.8
unnamed: U79.10, U90.3
unnamed: U83.9 (COUT), U93.7 (CIN)
unnamed: U84.7 (CIN), U93.9 (COUT)
unnamed: U84.9 (COUT), U94.7 (CIN)
unnamed: U86.7 (CIN), U96.9 (COUT)
unnamed: U87.4 (1Y), U93.5 (A0)
unnamed: U87.7 (2Y), U93.3 (A1)
unnamed: U87.9 (4Y), U93.12 (A3)
unnamed: U87.12 (3Y), U93.14 (A2)
unnamed: U88.4 (1Y), U94.5 (A0)
unnamed: U88.7 (2Y), U94.3 (A1)
unnamed: U88.9 (4Y), U94.12 (A3)
unnamed: U88.12 (3Y), U94.14 (A2)
unnamed: U90.6, U90.10
unnamed: U100.1 (~OE1), U115.4 (~Y0)
unnamed: U75.11, U79.13, U103.2 (S1), U107.2 (S1), U110.2 (S1), U114.2 (S1)
unnamed: U27.11, U75.8, U103.14 (S0), U107.14 (S0), U110.14 (S0), U114.14 (S0)
unnamed: U106.1 (~OE1), U115.5 (~Y1)
unnamed: U108.1 (~OE1), U115.6 (~Y2)
unnamed: U86.9 (COUT), U109.4 (1I2)
unnamed: U79.11, U109.14 (S0)
unnamed: U98.3 (D0), U111.4 (1Y)
unnamed: U98.4 (D1), U111.7 (2Y)
unnamed: U98.8 (D3), U111.9 (4Y)
unnamed: U98.7 (D2), U111.12 (3Y)
unnamed: U98.13 (D4), U112.4 (1Y)
unnamed: U98.14 (D5), U112.7 (2Y)
unnamed: U98.18 (D7), U112.9 (4Y)
unnamed: U98.17 (D6), U112.12 (3Y)
unnamed: U115.7 (~Y3), U116.1 (~OE1)
unnamed: U64.1 (~OE1), U115.9 (~Y3)
unnamed: U56.1 (~OE1), U115.10 (~Y2)
unnamed: U65.1 (~OE1), U115.11 (~Y1)
unnamed: U57.1 (~OE1), U115.12 (~Y0)
unnamed: U79.3, U120.1, U120.3
unnamed: U75.4, U120.12
Q: U44.5 (~G2B), U81.11 (CP), U82.11 (CP)
RegCtrl10: U60.14 (S0), U61.14 (S0), U62.14 (S0), U63.14 (S0), U68.14 (S0), U69.14 (S0), U70.14 (S0), U71.14 (S0)
RegCtrl11: U60.2 (S1), U61.2 (S1), U62.2 (S1), U63.2 (S1), U68.2 (S1), U69.2 (S1), U70.2 (S1), U71.2 (S1)
RegCtrl12: U44.6 (G1)
RegCtrl13: U44.1 (A0)
RegCtrl14: U44.2 (A1)
RegCtrl15: U44.3 (A2)
RegCtrl16: U111.1 (S), U112.1 (S)
RegCtrl17: U98.1 (~E)
WB_A0: U44.11 (Y4), U45.11 (CP), U52.11 (CP)
WB_A1: U44.10 (Y5), U46.11 (CP), U53.11 (CP)
WB_AD0: U45.2 (D0), U46.2 (D0), U47.2 (D0), U48.2 (D0), U83.4 (S0)
WB_AD1: U45.3 (D1), U46.3 (D1), U47.3 (D1), U48.3 (D1), U83.1 (S1)
WB_AD2: U45.4 (D2), U46.4 (D2), U47.4 (D2), U48.4 (D2), U83.13 (S2)
WB_AD3: U45.5 (D3), U46.5 (D3), U47.5 (D3), U48.5 (D3), U83.10 (S3)
WB_AD4: U45.6 (D4), U46.6 (D4), U47.6 (D4), U48.6 (D4), U93.4 (S0)
WB_AD5: U45.7 (D5), U46.7 (D5), U47.7 (D5), U48.7 (D5), U93.1 (S1)
WB_AD6: U45.8 (D6), U46.8 (D6), U47.8 (D6), U48.8 (D6), U93.13 (S2)
WB_AD7: U45.9 (D7), U46.9 (D7), U47.9 (D7), U48.9 (D7), U93.10 (S3)
WB_AD8: U52.2 (D0), U53.2 (D0), U54.2 (D0), U55.2 (D0), U84.4 (S0)
WB_AD9: U52.3 (D1), U53.3 (D1), U54.3 (D1), U55.3 (D1), U84.1 (S1)
WB_AD10: U52.4 (D2), U53.4 (D2), U54.4 (D2), U55.4 (D2), U84.13 (S2)
WB_AD11: U52.5 (D3), U53.5 (D3), U54.5 (D3), U55.5 (D3), U84.10 (S3)
WB_AD12: U52.6 (D4), U53.6 (D4), U54.6 (D4), U55.6 (D4), U94.4 (S0)
WB_AD13: U52.7 (D5), U53.7 (D5), U54.7 (D5), U55.7 (D5), U94.1 (S1)
WB_AD14: U52.8 (D6), U53.8 (D6), U54.8 (D6), U55.8 (D6), U94.13 (S2)
WB_AD15: U52.9 (D7), U53.9 (D7), U54.9 (D7), U55.9 (D7), U94.10 (S3)
WB_CP: U44.9 (Y6), U47.11 (CP), U54.11 (CP)
WB_DB0: U50.2 (D0), U51.2 (D0), U58.2 (D0), U59.2 (D0), U64.2 (A0), U100.18 (Y0), U106.18 (Y0), U108.18 (Y0), U111.3 (1I1), U116.18 (Y0)
WB_DB1: U50.3 (D1), U51.3 (D1), U58.3 (D1), U59.3 (D1), U64.3 (A1), U100.17 (Y1), U106.17 (Y1), U108.17 (Y1), U111.6 (2I1), U116.17 (Y1)
WB_DB2: U50.4 (D2), U51.4 (D2), U58.4 (D2), U59.4 (D2), U64.4 (A2), U100.16 (Y2), U106.16 (Y2), U108.16 (Y2), U111.13 (3I1), U116.16 (Y2)
WB_DB3: U50.5 (D3), U51.5 (D3), U58.5 (D3), U59.5 (D3), U64.5 (A3), U100.15 (Y3), U106.15 (Y3), U108.15 (Y3), U111.10 (4I1), U116.15 (Y3)
WB_DB4: U50.6 (D4), U51.6 (D4), U58.6 (D4), U59.6 (D4), U64.6 (A4), U100.14 (Y4), U106.14 (Y4), U108.14 (Y4), U112.3 (1I1), U116.14 (Y4)
WB_DB5: U50.7 (D5), U51.7 (D5), U58.7 (D5), U59.7 (D5), U64.7 (A5), U100.13 (Y5), U106.13 (Y5), U108.13 (Y5), U112.6 (2I1), U116.13 (Y5)
WB_DB6: U50.8 (D6), U51.8 (D6), U58.8 (D6), U59.8 (D6), U64.8 (A6), U100.12 (Y6), U106.12 (Y6), U108.12 (Y6), U112.13 (3I1), U116.12 (Y6)
WB_R0: U44.15 (Y0), U50.11 (CP)
WB_R1: U44.14 (Y1), U51.11 (CP)
WB_R2: U44.13 (Y2), U58.11 (CP)
WB_R3: U44.12 (Y3), U59.11 (CP)
WB_SP: U44.7 (Y7), U48.11 (CP), U55.11 (CP)
WRO0: U57.2 (A0), U60.7 (1Y), U78.2
WRO1: U57.3 (A1), U60.9 (2Y), U78.5
WRO2: U57.4 (A2), U61.7 (1Y), U78.10
WRO3: U57.5 (A3), U61.9 (2Y), U78.13
WRO4: U57.6 (A4), U62.7 (1Y), U85.2
WRO5: U57.7 (A5), U62.9 (2Y), U85.5
WRO6: U57.8 (A6), U63.7 (1Y), U85.10
WRO7: U57.9 (A7), U63.9 (2Y), U85.13
WRO8: U65.2 (A0), U68.7 (1Y), U89.2
WRO9: U65.3 (A1), U68.9 (2Y), U89.5
WRO10: U65.4 (A2), U69.7 (1Y), U89.10
WRO11: U65.5 (A3), U69.9 (2Y), U89.13
WRO12: U65.6 (A4), U70.7 (1Y), U95.2
WRO13: U65.7 (A5), U70.9 (2Y), U95.5
WRO14: U65.8 (A6), U71.7 (1Y), U95.10
WRO15: U65.9 (A7), U71.9 (2Y), U95.13
nBR_SEL2: U67.4, U115.15 (~E)
nE: U44.4 (~G2A)
nQ: U98.11 (CP)
tNL1: U76.3 (1I1), U76.6 (2I1), U76.10 (4I1), U76.13 (3I1), U87.3 (1I1), U87.6 (2I1), U87.10 (4I1), U87.13 (3I1), U120.4
tNL2: U77.3 (1I1), U77.6 (2I1), U77.10 (4I1), U77.13 (3I1), U88.3 (1I1), U88.6 (2I1), U88.10 (4I1), U88.13 (3I1), U120.2
~A-Active: U66.4 (Y), U82.1 (~E)
~B-Active: U49.4 (Y), U81.1 (~E)

Notes on the sheet:
AddrHi
AddrLo
DataOut to Inner DataBus
A0_Lo
A0_Hi
