m-okada/CPU2908/Schematics/74HC/RevC3/CPU2908Sequencer.sch

## KiCad design Schematics/74HC/RevC3/CPU2908Sequencer.sch (2020-06-03)

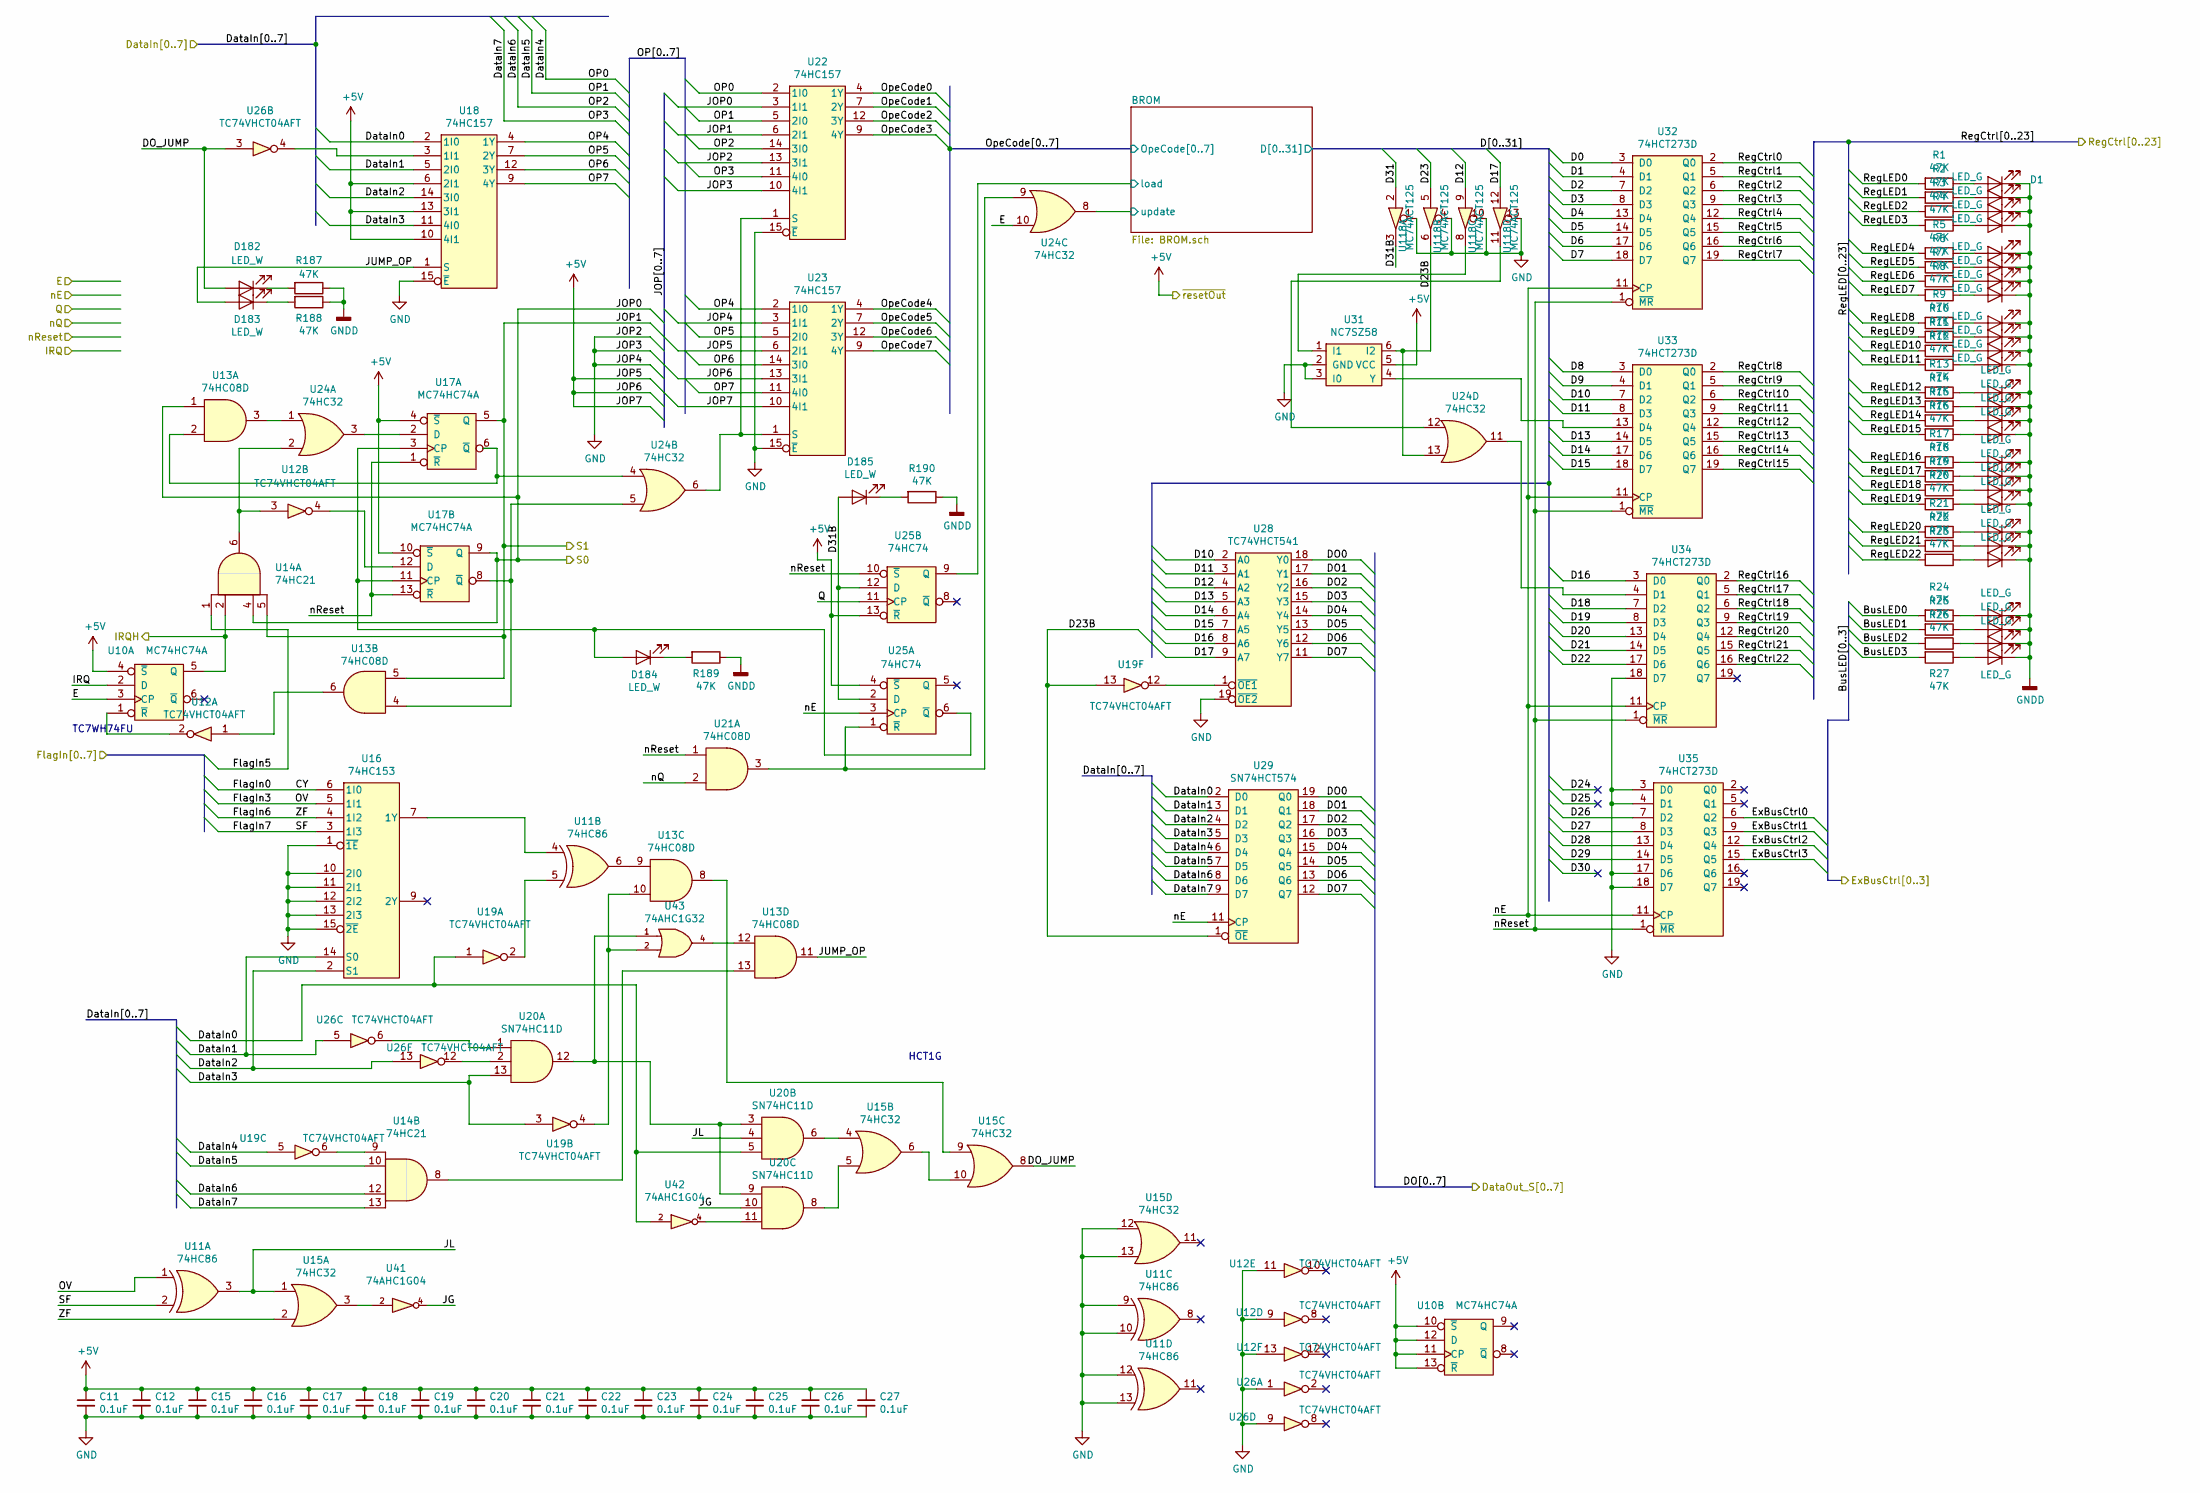
[picture p17: schematic CPU2908Sequencer.sch]

Parts:
C11, C12, C15, C16, C17, C18, C19, C20, C21, C22, C23, C24, C25, C26, C27: 0.1uF; C_0402
D1, D2, D3, D4, D5, D6, D7, D8, D9, D10, D11, D12, D13, D14, D15, D16, D17, D18, D19, D20, D21, D22, D23, D24, D25, D26, D27: LED_G; LED_0402
D182, D183, D184, D185: LED_W; LED_0402
R1, R2, R3, R4, R5, R6, R7, R8, R9, R10, R11, R12, R13, R14, R15, R16, R17, R18, R19, R20, R21, R22, R23, R24, R25, R26, R27, R187, R188, R189, R190: 47K; R_0402
U10, U17: MC74HC74A; MC74HC74ADG
U11: 74HC86; SOIC-14_W3.9mm
U12, U19, U26: TC74VHCT04AFT; TSSOP-14_4.4x5mm_Pitch0.65mm
U13, U21: 74HC08D; SOIC-14_W3.9mm
U14: 74HC21; SOIC-14_W3.9mm
U15, U24: 74HC32; SOIC-14_W3.9mm
U16: 74HC153; SO-16-N
U18, U22, U23: 74HC157; SN74HC157DR
U20: SN74HC11D
U25: 74HC74; MC74HC74ADG
U28: TC74VHCT541; TSSOP-20_W4.4mm
U29: SN74HCT574; SN74HCT574NSR
U31: NC7SZ58; SOT-363_SC-70-6_Handsoldering
U32, U33, U34, U35: 74HCT273D; SOIC-20_W7.5mm
U41, U42: 74AHC1G04; SOT-23-5
U43: 74AHC1G32; TSOP-5_1.65x3.05mm_Pitch0.95mm
U118: MC74ACT125; SOIC-14_W3.9mm

Connections:
+5V: C11.1, C12.1, C15.1, C16.1, C17.1, C18.1, C19.1, C20.1, C21.1, C22.1, C23.1, C24.1, C25.1, C26.1, C27.1, U10.4 (~S), U10.10 (~S), U10.11 (CP), U10.12 (D), U10.13 (~R), U17.4 (~S), U17.10 (~S), U18.6 (2I1), U18.10 (4I1), U18.13 (3I1), U23.6 (2I1), U23.10 (4I1), U23.13 (3I1), U25.4 (~S), U25.13 (~R), U31.5 (VCC)
BusLED0: R24.2
BusLED1: R25.2
BusLED2: R26.2
BusLED3: R27.2
CY: U16.6 (1I0)
D0: U32.3 (D0)
D1: U32.4 (D1)
D2: U32.7 (D2)
D3: U32.8 (D3)
D4: U32.13 (D4)
D5: U32.14 (D5)
D6: U32.17 (D6)
D7: U32.18 (D7)
D8: U33.3 (D0)
D9: U33.4 (D1)
D10: U28.2 (A0), U33.7 (D2)
D11: U28.3 (A1), U33.8 (D3)
D12: U28.4 (A2), U118.9
D13: U28.5 (A3), U33.14 (D5)
D14: U28.6 (A4), U33.17 (D6)
D15: U28.7 (A5), U33.18 (D7)
D16: U28.8 (A6), U34.3 (D0)
D17: U28.9 (A7), U118.12
D18: U34.7 (D2)
D19: U34.8 (D3)
D20: U34.13 (D4)
D21: U34.14 (D5)
D22: U34.17 (D6)
D23: U118.5
D23B: U19.13, U24.13, U29.1 (~OE), U31.6 (I2), U118.6
D26: U35.7 (D2)
D27: U35.8 (D3)
D28: U35.13 (D4)
D29: U35.14 (D5)
D31: U118.2
D31B: D185.2 (A), U25.2 (D), U25.12 (D), U118.3
DO0: U28.18 (Y0), U29.19 (Q0)
DO1: U28.17 (Y1), U29.18 (Q1)
DO2: U28.16 (Y2), U29.17 (Q2)
DO3: U28.15 (Y3), U29.16 (Q3)
DO4: U28.14 (Y4), U29.15 (Q4)
DO5: U28.13 (Y5), U29.14 (Q5)
DO6: U28.12 (Y6), U29.13 (Q6)
DO7: U28.11 (Y7), U29.12 (Q7)
DO_JUMP: D182.2 (A), U15.8, U26.3
DataIn0: U18.2 (1I0), U19.1, U20.5, U29.2 (D0), U42.2
DataIn1: U16.14 (S0), U18.5 (2I0), U26.5, U29.3 (D1)
DataIn2: U16.2 (S1), U18.14 (3I0), U26.13, U29.4 (D2)
DataIn3: U18.11 (4I0), U19.3, U20.13, U29.5 (D3)
DataIn4: U19.5, U22.2 (1I0), U29.6 (D4)
DataIn5: U14.10, U22.5 (2I0), U29.7 (D5)
DataIn6: U14.12, U22.14 (3I0), U29.8 (D6)
DataIn7: U14.13, U22.11 (4I0), U29.9 (D7)
E: U10.3 (CP), U24.10
ExBusCtrl0: U35.6 (Q2)
ExBusCtrl1: U35.9 (Q3)
ExBusCtrl2: U35.12 (Q4)
ExBusCtrl3: U35.15 (Q5)
FlagIn3: U11.1, U16.5 (1I1)
FlagIn5: U14.1
FlagIn6: U15.2, U16.4 (1I2)
FlagIn7: U11.2, U16.3 (1I3)
GND: C11.2, C12.2, C15.2, C16.2, C17.2, C18.2, C19.2, C20.2, C21.2, C22.2, C23.2, C24.2, C25.2, C26.2, C27.2, U11.9, U11.10, U11.12, U11.13, U12.9, U12.11, U12.13, U15.12, U15.13, U16.1 (~1E), U16.10 (2I0), U16.11 (2I1), U16.12 (2I2), U16.13 (2I3), U16.15 (~2E), U18.15 (~E), U22.10 (4I1), U22.13 (3I1), U22.15 (~E), U23.3 (1I1), U23.15 (~E), U26.1, U26.9, U28.19 (~OE2), U31.2 (GND), U31.3 (I0), U34.18 (D7), U35.3 (D0), U35.4 (D1), U35.17 (D6), U35.18 (D7), U118.1, U118.4, U118.10, U118.13
GNDD: D1.1 (K), D2.1 (K), D3.1 (K), D4.1 (K), D5.1 (K), D6.1 (K), D7.1 (K), D8.1 (K), D9.1 (K), D10.1 (K), D11.1 (K), D12.1 (K), D13.1 (K), D14.1 (K), D15.1 (K), D16.1 (K), D17.1 (K), D18.1 (K), D19.1 (K), D20.1 (K), D21.1 (K), D22.1 (K), D23.1 (K), D24.1 (K), D25.1 (K), D26.1 (K), D27.1 (K), R187.1, R188.1, R189.1, R190.1
IRQ: U10.2 (D)
IRQH: U10.5 (Q), U14.2
JG: U20.10, U41.4
JL: U11.3, U15.1, U20.4
JOP0: U13.1, U14.4, U17.9 (Q), U22.3 (1I1)
JOP1: U13.5, U14.5, U17.5 (Q), U22.6 (2I1)
JUMP_OP: D183.2 (A), U13.11, U18.1 (S)
unnamed: D1.2 (A), R1.1
unnamed: D2.2 (A), R2.1
unnamed: D3.2 (A), R3.1
unnamed: D4.2 (A), R4.1
unnamed: D5.2 (A), R5.1
unnamed: D6.2 (A), R6.1
unnamed: D7.2 (A), R7.1
unnamed: D8.2 (A), R8.1
unnamed: D9.2 (A), R9.1
unnamed: D10.2 (A), R10.1
unnamed: D11.2 (A), R11.1
unnamed: D12.2 (A), R12.1
unnamed: D13.2 (A), R13.1
unnamed: D14.2 (A), R14.1
unnamed: D15.2 (A), R15.1
unnamed: D16.2 (A), R16.1
unnamed: D17.2 (A), R17.1
unnamed: D18.2 (A), R18.1
unnamed: D19.2 (A), R19.1
unnamed: D20.2 (A), R20.1
unnamed: D21.2 (A), R21.1
unnamed: D22.2 (A), R22.1
unnamed: D23.2 (A), R23.1
unnamed: D24.2 (A), R24.1
unnamed: D25.2 (A), R25.1
unnamed: D26.2 (A), R26.1
unnamed: D27.2 (A), R27.1
unnamed: D182.1 (K), R187.2
unnamed: D183.1 (K), R188.2
unnamed: D184.1 (K), R189.2
unnamed: D184.2 (A), U17.3 (CP), U17.11 (CP), U25.6 (~Q)
unnamed: D185.1 (K), R190.2
unnamed: U10.1 (~R), U12.2
unnamed: U11.4, U16.7 (1Y)
unnamed: U11.5, U19.2
unnamed: U11.6, U13.9
unnamed: U12.1, U13.6
unnamed: U12.3, U14.6, U24.2
unnamed: U12.4, U17.12 (D)
unnamed: U13.2, U17.6 (~Q), U24.4
unnamed: U13.3, U24.1
unnamed: U13.4, U17.8 (~Q), U24.5
unnamed: U13.8, U15.9
unnamed: U13.10, U19.4, U43.2
unnamed: U13.12, U43.4
unnamed: U13.13, U14.8
unnamed: U14.9, U19.6
unnamed: U15.3, U41.2
unnamed: U15.4, U20.6
unnamed: U15.5, U20.8
unnamed: U15.6, U15.10
unnamed: U17.2 (D), U24.3
unnamed: U18.3 (1I1), U26.4
unnamed: U19.12, U28.1 (~OE1)
unnamed: U20.1, U26.6
unnamed: U20.2, U26.12
unnamed: U20.11, U42.4
unnamed: U20.3, U20.9, U20.12, U43.1
unnamed: U21.3, U24.9, U25.1 (~R)
unnamed: U22.1 (S), U23.1 (S), U24.6
unnamed: U24.11, U34.4 (D1)
unnamed: U31.4 (Y), U33.13 (D4)
unnamed: U31.1 (I1), U118.8
unnamed: U24.12, U118.11
OP4: U18.4 (1Y), U23.2 (1I0)
OP5: U18.7 (2Y), U23.5 (2I0)
OP6: U18.12 (3Y), U23.14 (3I0)
OP7: U18.9 (4Y), U23.11 (4I0)
OpeCode0: U22.4 (1Y)
OpeCode1: U22.7 (2Y)
OpeCode2: U22.12 (3Y)
OpeCode3: U22.9 (4Y)
OpeCode4: U23.4 (1Y)
OpeCode5: U23.7 (2Y)
OpeCode6: U23.12 (3Y)
OpeCode7: U23.9 (4Y)
Q: U25.11 (CP)
RegCtrl0: U32.2 (Q0)
RegCtrl1: U32.5 (Q1)
RegCtrl2: U32.6 (Q2)
RegCtrl3: U32.9 (Q3)
RegCtrl4: U32.12 (Q4)
RegCtrl5: U32.15 (Q5)
RegCtrl6: U32.16 (Q6)
RegCtrl7: U32.19 (Q7)
RegCtrl8: U33.2 (Q0)
RegCtrl9: U33.5 (Q1)
RegCtrl10: U33.6 (Q2)
RegCtrl11: U33.9 (Q3)
RegCtrl12: U33.12 (Q4)
RegCtrl13: U33.15 (Q5)
RegCtrl14: U33.16 (Q6)
RegCtrl15: U33.19 (Q7)
RegCtrl16: U34.2 (Q0)
RegCtrl17: U34.5 (Q1)
RegCtrl18: U34.6 (Q2)
RegCtrl19: U34.9 (Q3)
RegCtrl20: U34.12 (Q4)
RegCtrl21: U34.15 (Q5)
RegCtrl22: U34.16 (Q6)
RegLED0: R1.2
RegLED1: R2.2
RegLED2: R3.2
RegLED3: R4.2
RegLED4: R5.2
RegLED5: R6.2
RegLED6: R7.2
RegLED7: R8.2
RegLED8: R9.2
RegLED9: R10.2
RegLED10: R11.2
RegLED11: R12.2
RegLED12: R13.2
RegLED13: R14.2
RegLED14: R15.2
RegLED15: R16.2
RegLED16: R17.2
RegLED17: R18.2
RegLED18: R19.2
RegLED19: R20.2
RegLED20: R21.2
RegLED21: R22.2
RegLED22: R23.2
load: U25.9 (Q)
nE: U25.3 (CP), U29.11 (CP), U32.11 (CP), U33.11 (CP), U34.11 (CP), U35.11 (CP)
nQ: U21.2
nReset: U17.1 (~R), U17.13 (~R), U21.1, U25.10 (~S), U32.1 (~MR), U33.1 (~MR), U34.1 (~MR), U35.1 (~MR)
update: U24.8

Notes on the sheet:
HCT1G
TC7WH74FU
