m-okada/CPU2908/Schematics/74HC/RevC3/REG_LED.sch

## KiCad design Schematics/74HC/RevC3/REG_LED.sch (2020-06-03)

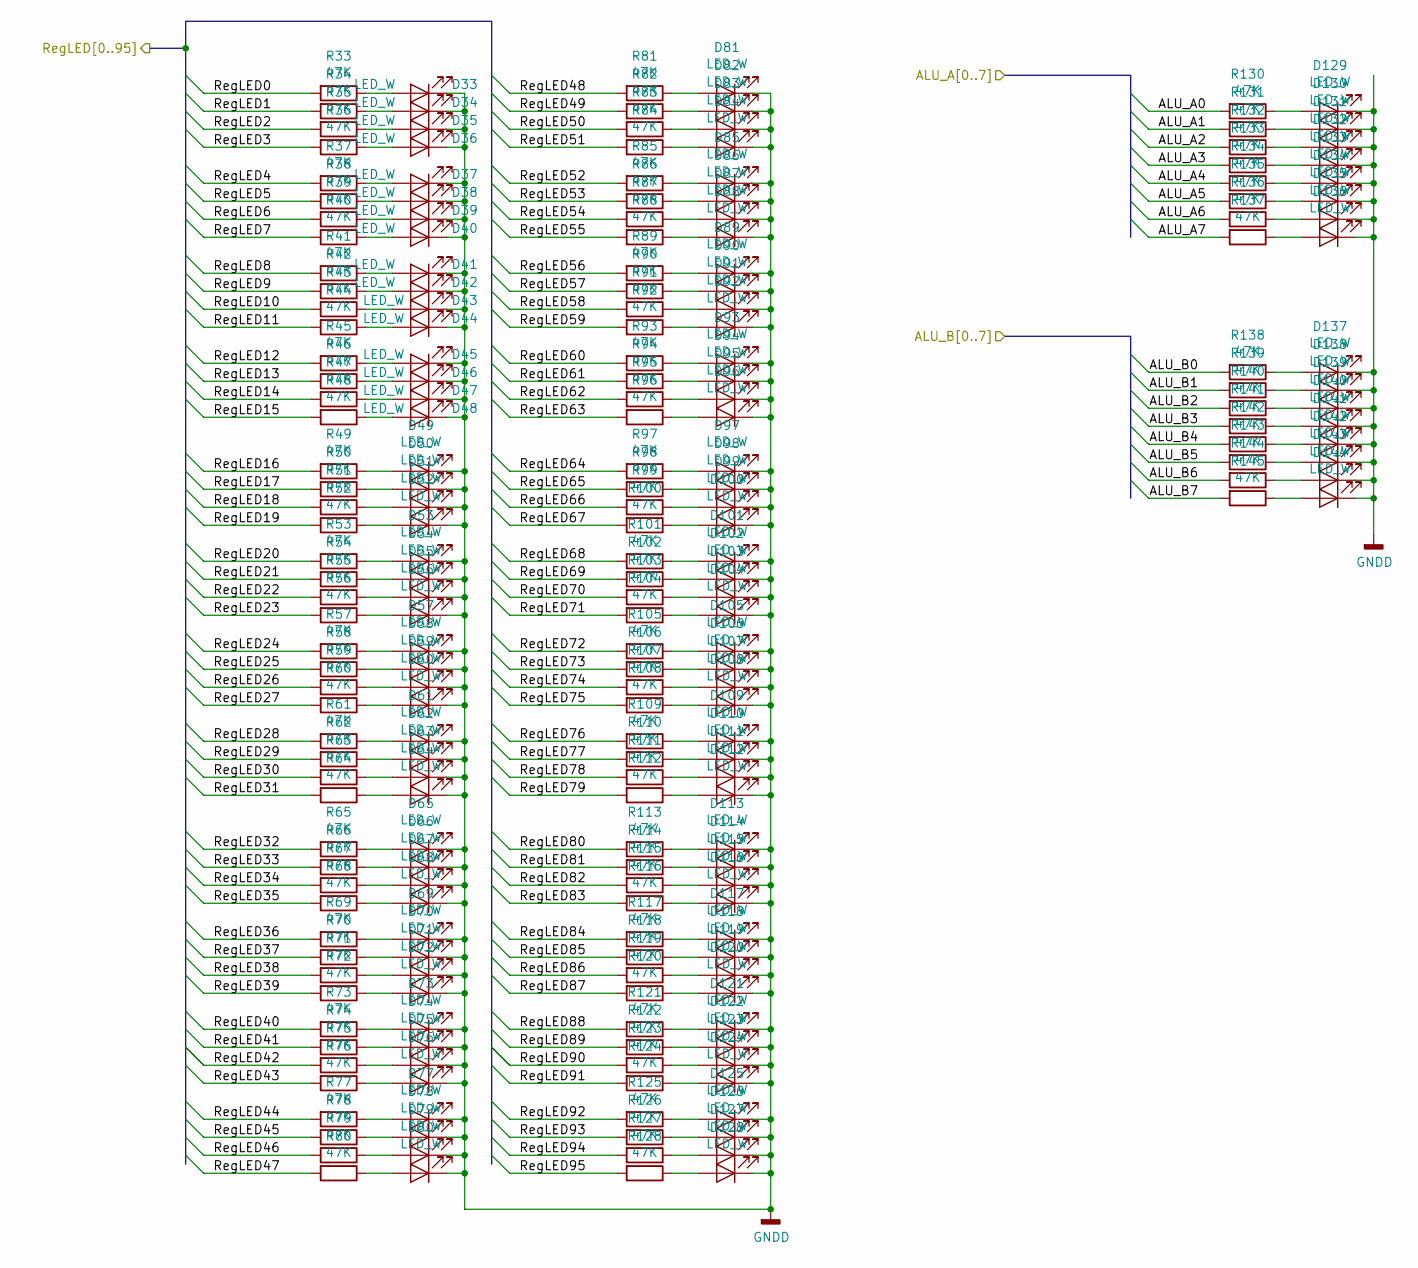
[picture p18: schematic REG_LED.sch]

Parts:
D33, D34, D35, D36, D37, D38, D39, D40, D41, D42, D43, D44, D45, D46, D47, D48, D49, D50, D51, D52, D53, D54, D55, D56, D57, D58, D59, D60, D61, D62, D63, D64, D65, D66, D67, D68, D69, D70, D71, D72, D73, D74, D75, D76, D77, D78, D79, D80, D81, D82, D83, D84, D85, D86, D87, D88, D89, D90, D91, D92, D93, D94, D95, D96, D97, D98, D99, D100, D101, D102, D103, D104, D105, D106, D107, D108, D109, D110, D111, D112, D113, D114, D115, D116, D117, D118, D119, D120, D121, D122, D123, D124, D125, D126, D127, D128, D129, D130, D131, D132, D133, D134, D135, D136, D137, D138, D139, D140, D141, D142, D143, D144: LED_W; LED_0402
R33, R34, R35, R36, R37, R38, R39, R40, R41, R42, R43, R44, R45, R46, R47, R48, R49, R50, R51, R52, R53, R54, R55, R56, R57, R58, R59, R60, R61, R62, R63, R64, R65, R66, R67, R68, R69, R70, R71, R72, R73, R74, R75, R76, R77, R78, R79, R80, R81, R82, R83, R84, R85, R86, R87, R88, R89, R90, R91, R92, R93, R94, R95, R96, R97, R98, R99, R100, R101, R102, R103, R104, R105, R106, R107, R108, R109, R110, R111, R112, R113, R114, R115, R116, R117, R118, R119, R120, R121, R122, R123, R124, R125, R126, R127, R128, R130, R131, R132, R133, R134, R135, R136, R137, R138, R139, R140, R141, R142, R143, R144, R145: 47K; R_0402

Connections:
ALU_A0: R130.2
ALU_A1: R131.2
ALU_A2: R132.2
ALU_A3: R133.2
ALU_A4: R134.2
ALU_A5: R135.2
ALU_A6: R136.2
ALU_A7: R137.2
ALU_B0: R138.2
ALU_B1: R139.2
ALU_B2: R140.2
ALU_B3: R141.2
ALU_B4: R142.2
ALU_B5: R143.2
ALU_B6: R144.2
ALU_B7: R145.2
GNDD: D33.1 (K), D34.1 (K), D35.1 (K), D36.1 (K), D37.1 (K), D38.1 (K), D39.1 (K), D40.1 (K), D41.1 (K), D42.1 (K), D43.1 (K), D44.1 (K), D45.1 (K), D46.1 (K), D47.1 (K), D48.1 (K), D49.1 (K), D50.1 (K), D51.1 (K), D52.1 (K), D53.1 (K), D54.1 (K), D55.1 (K), D56.1 (K), D57.1 (K), D58.1 (K), D59.1 (K), D60.1 (K), D61.1 (K), D62.1 (K), D63.1 (K), D64.1 (K), D65.1 (K), D66.1 (K), D67.1 (K), D68.1 (K), D69.1 (K), D70.1 (K), D71.1 (K), D72.1 (K), D73.1 (K), D74.1 (K), D75.1 (K), D76.1 (K), D77.1 (K), D78.1 (K), D79.1 (K), D80.1 (K), D81.1 (K), D82.1 (K), D83.1 (K), D84.1 (K), D85.1 (K), D86.1 (K), D87.1 (K), D88.1 (K), D89.1 (K), D90.1 (K), D91.1 (K), D92.1 (K), D93.1 (K), D94.1 (K), D95.1 (K), D96.1 (K), D97.1 (K), D98.1 (K), D99.1 (K), D100.1 (K), D101.1 (K), D102.1 (K), D103.1 (K), D104.1 (K), D105.1 (K), D106.1 (K), D107.1 (K), D108.1 (K), D109.1 (K), D110.1 (K), D111.1 (K), D112.1 (K), D113.1 (K), D114.1 (K), D115.1 (K), D116.1 (K), D117.1 (K), D118.1 (K), D119.1 (K), D120.1 (K), D121.1 (K), D122.1 (K), D123.1 (K), D124.1 (K), D125.1 (K), D126.1 (K), D127.1 (K), D128.1 (K), D129.1 (K), D130.1 (K), D131.1 (K), D132.1 (K), D133.1 (K), D134.1 (K), D135.1 (K), D136.1 (K), D137.1 (K), D138.1 (K), D139.1 (K), D140.1 (K), D141.1 (K), D142.1 (K), D143.1 (K), D144.1 (K)
unnamed: D33.2 (A), R33.1
unnamed: D34.2 (A), R34.1
unnamed: D35.2 (A), R35.1
unnamed: D36.2 (A), R36.1
unnamed: D37.2 (A), R37.1
unnamed: D38.2 (A), R38.1
unnamed: D39.2 (A), R39.1
unnamed: D40.2 (A), R40.1
unnamed: D41.2 (A), R41.1
unnamed: D42.2 (A), R42.1
unnamed: D43.2 (A), R43.1
unnamed: D44.2 (A), R44.1
unnamed: D45.2 (A), R45.1
unnamed: D46.2 (A), R46.1
unnamed: D47.2 (A), R47.1
unnamed: D48.2 (A), R48.1
unnamed: D49.2 (A), R49.1
unnamed: D50.2 (A), R50.1
unnamed: D51.2 (A), R51.1
unnamed: D52.2 (A), R52.1
unnamed: D53.2 (A), R53.1
unnamed: D54.2 (A), R54.1
unnamed: D55.2 (A), R55.1
unnamed: D56.2 (A), R56.1
unnamed: D57.2 (A), R57.1
unnamed: D58.2 (A), R58.1
unnamed: D59.2 (A), R59.1
unnamed: D60.2 (A), R60.1
unnamed: D61.2 (A), R61.1
unnamed: D62.2 (A), R62.1
unnamed: D63.2 (A), R63.1
unnamed: D64.2 (A), R64.1
unnamed: D65.2 (A), R65.1
unnamed: D66.2 (A), R66.1
unnamed: D67.2 (A), R67.1
unnamed: D68.2 (A), R68.1
unnamed: D69.2 (A), R69.1
unnamed: D70.2 (A), R70.1
unnamed: D71.2 (A), R71.1
unnamed: D72.2 (A), R72.1
unnamed: D73.2 (A), R73.1
unnamed: D74.2 (A), R74.1
unnamed: D75.2 (A), R75.1
unnamed: D76.2 (A), R76.1
unnamed: D77.2 (A), R77.1
unnamed: D78.2 (A), R78.1
unnamed: D79.2 (A), R79.1
unnamed: D80.2 (A), R80.1
unnamed: D81.2 (A), R81.1
unnamed: D82.2 (A), R82.1
unnamed: D83.2 (A), R83.1
unnamed: D84.2 (A), R84.1
unnamed: D85.2 (A), R85.1
unnamed: D86.2 (A), R86.1
unnamed: D87.2 (A), R87.1
unnamed: D88.2 (A), R88.1
unnamed: D89.2 (A), R89.1
unnamed: D90.2 (A), R90.1
unnamed: D91.2 (A), R91.1
unnamed: D92.2 (A), R92.1
unnamed: D93.2 (A), R93.1
unnamed: D94.2 (A), R94.1
unnamed: D95.2 (A), R95.1
unnamed: D96.2 (A), R96.1
unnamed: D97.2 (A), R97.1
unnamed: D98.2 (A), R98.1
unnamed: D99.2 (A), R99.1
unnamed: D100.2 (A), R100.1
unnamed: D101.2 (A), R101.1
unnamed: D102.2 (A), R102.1
unnamed: D103.2 (A), R103.1
unnamed: D104.2 (A), R104.1
unnamed: D105.2 (A), R105.1
unnamed: D106.2 (A), R106.1
unnamed: D107.2 (A), R107.1
unnamed: D108.2 (A), R108.1
unnamed: D109.2 (A), R109.1
unnamed: D110.2 (A), R110.1
unnamed: D111.2 (A), R111.1
unnamed: D112.2 (A), R112.1
unnamed: D113.2 (A), R113.1
unnamed: D114.2 (A), R114.1
unnamed: D115.2 (A), R115.1
unnamed: D116.2 (A), R116.1
unnamed: D117.2 (A), R117.1
unnamed: D118.2 (A), R118.1
unnamed: D119.2 (A), R119.1
unnamed: D120.2 (A), R120.1
unnamed: D121.2 (A), R121.1
unnamed: D122.2 (A), R122.1
unnamed: D123.2 (A), R123.1
unnamed: D124.2 (A), R124.1
unnamed: D125.2 (A), R125.1
unnamed: D126.2 (A), R126.1
unnamed: D127.2 (A), R127.1
unnamed: D128.2 (A), R128.1
unnamed: D129.2 (A), R130.1
unnamed: D130.2 (A), R131.1
unnamed: D131.2 (A), R132.1
unnamed: D132.2 (A), R133.1
unnamed: D133.2 (A), R134.1
unnamed: D134.2 (A), R135.1
unnamed: D135.2 (A), R136.1
unnamed: D136.2 (A), R137.1
unnamed: D137.2 (A), R138.1
unnamed: D138.2 (A), R139.1
unnamed: D139.2 (A), R140.1
unnamed: D140.2 (A), R141.1
unnamed: D141.2 (A), R142.1
unnamed: D142.2 (A), R143.1
unnamed: D143.2 (A), R144.1
unnamed: D144.2 (A), R145.1
RegLED0: R33.2
RegLED1: R34.2
RegLED2: R35.2
RegLED3: R36.2
RegLED4: R37.2
RegLED5: R38.2
RegLED6: R39.2
RegLED7: R40.2
RegLED8: R41.2
RegLED9: R42.2
RegLED10: R43.2
RegLED11: R44.2
RegLED12: R45.2
RegLED13: R46.2
RegLED14: R47.2
RegLED15: R48.2
RegLED16: R49.2
RegLED17: R50.2
RegLED18: R51.2
RegLED19: R52.2
RegLED20: R53.2
RegLED21: R54.2
RegLED22: R55.2
RegLED23: R56.2
RegLED24: R57.2
RegLED25: R58.2
RegLED26: R59.2
RegLED27: R60.2
RegLED28: R61.2
RegLED29: R62.2
RegLED30: R63.2
RegLED31: R64.2
RegLED32: R65.2
RegLED33: R66.2
RegLED34: R67.2
RegLED35: R68.2
RegLED36: R69.2
RegLED37: R70.2
RegLED38: R71.2
RegLED39: R72.2
RegLED40: R73.2
RegLED41: R74.2
RegLED42: R75.2
RegLED43: R76.2
RegLED44: R77.2
RegLED45: R78.2
RegLED46: R79.2
RegLED47: R80.2
RegLED48: R81.2
RegLED49: R82.2
RegLED50: R83.2
RegLED51: R84.2
RegLED52: R85.2
RegLED53: R86.2
RegLED54: R87.2
RegLED55: R88.2
RegLED56: R89.2
RegLED57: R90.2
RegLED58: R91.2
RegLED59: R92.2
RegLED60: R93.2
RegLED61: R94.2
RegLED62: R95.2
RegLED63: R96.2
RegLED64: R97.2
RegLED65: R98.2
RegLED66: R99.2
RegLED67: R100.2
RegLED68: R101.2
RegLED69: R102.2
RegLED70: R103.2
RegLED71: R104.2
RegLED72: R105.2
RegLED73: R106.2
RegLED74: R107.2
RegLED75: R108.2
RegLED76: R109.2
RegLED77: R110.2
RegLED78: R111.2
RegLED79: R112.2
RegLED80: R113.2
RegLED81: R114.2
RegLED82: R115.2
RegLED83: R116.2
RegLED84: R117.2
RegLED85: R118.2
RegLED86: R119.2
RegLED87: R120.2
RegLED88: R121.2
RegLED89: R122.2
RegLED90: R123.2
RegLED91: R124.2
RegLED92: R125.2
RegLED93: R126.2
RegLED94: R127.2
RegLED95: R128.2
