m-okada/CPU2908/FPGA/MachXO2/impl1/top_prim.v

// Verilog netlist produced by program LSE :  version Diamond (64-bit) 3.8.0.115.3
// Netlist written on Tue Jan 07 17:55:17 2020
//
// Verilog Description of module top
//

module top (dataBus, nCS, clk, gclk1, nReset, nIRQ, nTSC, bootMode, 
            addrOut, clkQ, clkE, nRD, nAltRD, nWR, nAltWR, nIRQA, 
            IRQH, S, SPI_CLK, SPI_MISO, SPI_MOSI, SPI_CS, TxD, 
            RxD, nRTS, nCTS, SerialClock, monitor_sel, UM) /* synthesis syn_module_defined=1 */ ;   // v:/cpu2908/fpga/machxo2/top.v(1[8:11])
    inout [7:0]dataBus;   // v:/cpu2908/fpga/machxo2/top.v(2[19:26])
    output [3:0]nCS;   // v:/cpu2908/fpga/machxo2/top.v(3[20:23])
    input clk;   // v:/cpu2908/fpga/machxo2/top.v(4[13:16])
    input gclk1;   // v:/cpu2908/fpga/machxo2/top.v(5[13:18])
    input nReset;   // v:/cpu2908/fpga/machxo2/top.v(7[13:19])
    input nIRQ;   // v:/cpu2908/fpga/machxo2/top.v(8[13:17])
    input nTSC;   // v:/cpu2908/fpga/machxo2/top.v(9[13:17])
    input bootMode;   // v:/cpu2908/fpga/machxo2/top.v(11[13:21])
    output [19:0]addrOut;   // v:/cpu2908/fpga/machxo2/top.v(13[21:28])
    output clkQ;   // v:/cpu2908/fpga/machxo2/top.v(14[14:18])
    output clkE;   // v:/cpu2908/fpga/machxo2/top.v(15[14:18])
    output nRD;   // v:/cpu2908/fpga/machxo2/top.v(17[14:17])
    output nAltRD;   // v:/cpu2908/fpga/machxo2/top.v(17[18:24])
    output nWR;   // v:/cpu2908/fpga/machxo2/top.v(18[14:17])
    output nAltWR;   // v:/cpu2908/fpga/machxo2/top.v(18[18:24])
    output nIRQA;   // v:/cpu2908/fpga/machxo2/top.v(19[14:19])
    output IRQH;   // v:/cpu2908/fpga/machxo2/top.v(20[14:18])
    output [1:0]S;   // v:/cpu2908/fpga/machxo2/top.v(22[19:20])
    output SPI_CLK;   // v:/cpu2908/fpga/machxo2/top.v(25[14:21])
    output SPI_MISO;   // v:/cpu2908/fpga/machxo2/top.v(26[14:22])
    output SPI_MOSI;   // v:/cpu2908/fpga/machxo2/top.v(27[14:22])
    output [5:0]SPI_CS;   // v:/cpu2908/fpga/machxo2/top.v(28[19:25])
    output TxD;   // v:/cpu2908/fpga/machxo2/top.v(30[14:17])
    input RxD;   // v:/cpu2908/fpga/machxo2/top.v(31[13:16])
    output nRTS;   // v:/cpu2908/fpga/machxo2/top.v(32[14:18])
    input nCTS;   // v:/cpu2908/fpga/machxo2/top.v(33[13:17])
    output SerialClock;   // v:/cpu2908/fpga/machxo2/top.v(34[14:25])
    input [3:0]monitor_sel;   // v:/cpu2908/fpga/machxo2/top.v(36[18:29])
    output [7:0]UM;   // v:/cpu2908/fpga/machxo2/top.v(37[19:21])
    
    wire clk_c /* synthesis SET_AS_NETWORK=clk_c, is_clock=1 */ ;   // v:/cpu2908/fpga/machxo2/top.v(4[13:16])
    wire clkQ_c /* synthesis is_clock=1 */ ;   // v:/cpu2908/fpga/machxo2/top.v(14[14:18])
    wire clkE_c /* synthesis is_clock=1 */ ;   // v:/cpu2908/fpga/machxo2/top.v(15[14:18])
    wire RxD_c /* synthesis is_clock=1 */ ;   // v:/cpu2908/fpga/machxo2/top.v(31[13:16])
    wire SerialClock2 /* synthesis is_clock=1 */ ;   // v:/cpu2908/fpga/machxo2/top.v(59[6:18])
    wire iclk /* synthesis is_clock=1, SET_AS_NETWORK=iclk */ ;   // v:/cpu2908/fpga/machxo2/top.v(61[6:10])
    wire nRDRxD /* synthesis is_clock=1, SET_AS_NETWORK=nRDRxD */ ;   // v:/cpu2908/fpga/machxo2/top.v(123[6:12])
    wire nWRTxD /* synthesis is_clock=1, SET_AS_NETWORK=nWRTxD */ ;   // v:/cpu2908/fpga/machxo2/top.v(124[6:12])
    wire clkE_N_18 /* synthesis is_inv_clock=1 */ ;   // v:/cpu2908/fpga/machxo2/top.v(14[14:18])
    wire clkQ_c__inv /* synthesis is_inv_clock=1, is_clock=1 */ ;   // v:/cpu2908/fpga/machxo2/top.v(14[14:18])
    
    wire GND_net, VCC_net, nCS_c_1, nCS_c_0, nReset_c, nIRQ_c, nTSC_c, 
        n534, n537, n541, n545, n549, n553, n557, n561, n565, 
        n569, n573, n577, n581, n585, n589, n593, IRQH_c, S_c_1, 
        S_c_0, n615, n614, n613, TxD_c, nRTS_c, SerialClock_c_7;
    wire [127:0]sig;   // v:/cpu2908/fpga/machxo2/top.v(40[13:16])
    wire [7:0]ExDataIn;   // v:/cpu2908/fpga/machxo2/top.v(43[11:19])
    wire [7:0]ExDataOut;   // v:/cpu2908/fpga/machxo2/top.v(44[11:20])
    
    wire n612, n611, clk3, nReset1, nReset2;
    wire [7:0]bootROM_data;   // v:/cpu2908/fpga/machxo2/top.v(90[11:23])
    wire [7:0]sramData;   // v:/cpu2908/fpga/machxo2/top.v(92[11:19])
    wire [7:0]TxBuff;   // v:/cpu2908/fpga/machxo2/top.v(121[10:16])
    
    wire RxDclr, RxBusy, TxRdy, n610, sramWE, nReset2_N_20, nReset_N_22, 
        n307, n308, n309, n310, n311, n312, n313, n314;
    wire [7:0]ExDataIn_7__N_23;
    wire [7:0]ExDataIn_7__N_6;
    wire [15:0]subPort;   // v:/cpu2908/fpga/machxo2/register.v(100[20:27])
    
    wire n31, n972, n5386;
    wire [15:0]subPort_adj_589;   // v:/cpu2908/fpga/machxo2/register.v(100[20:27])
    
    wire R, R_adj_564, R_adj_565, ocea_enable_1;
    wire [7:0]subPort_adj_599;   // v:/cpu2908/fpga/machxo2/register.v(74[19:26])
    
    wire n865, n531, n5382, n616, n4970, n31_adj_574, UM_c, n4, 
        n929, n921, n3115, n4869, n4907, n5398, n4793, n22, 
        n20, n18, n5742, n14, n10;
    
    VHI i2 (.Z(VCC_net));
    INV i4931 (.A(clkQ_c), .Z(clkQ_c__inv));
    FD1P3DX clkQ_I_0_89 (.D(clkE_N_18), .SP(VCC_net), .CK(iclk), .CD(nReset2_N_20), 
            .Q(clkQ_c)) /* synthesis syn_instantiated=1 */ ;   // v:/cpu2908/fpga/machxo2/top.v(80[9:72])
    defparam clkQ_I_0_89.GSR = "DISABLED";
    FD1P3DX dff03 (.D(n5742), .SP(VCC_net), .CK(clk_c), .CD(nReset_N_22), 
            .Q(nReset1)) /* synthesis syn_instantiated=1 */ ;   // v:/cpu2908/fpga/machxo2/top.v(82[9:77])
    defparam dff03.GSR = "DISABLED";
    FD1P3DX nReset2_I_0_87 (.D(nReset1), .SP(VCC_net), .CK(clk_c), .CD(nReset_N_22), 
            .Q(nReset2)) /* synthesis syn_instantiated=1 */ ;   // v:/cpu2908/fpga/machxo2/top.v(83[9:80])
    defparam nReset2_I_0_87.GSR = "DISABLED";
    FD1P3DX dff05 (.D(nReset2), .SP(VCC_net), .CK(clk_c), .CD(nReset_N_22), 
            .Q(clk3)) /* synthesis syn_instantiated=1 */ ;   // v:/cpu2908/fpga/machxo2/top.v(84[9:77])
    defparam dff05.GSR = "DISABLED";
    FD1P3DX dff06 (.D(SerialClock_c_7), .SP(VCC_net), .CK(clkQ_c__inv), 
            .CD(nReset_N_22), .Q(SerialClock2)) /* synthesis syn_instantiated=1 */ ;   // v:/cpu2908/fpga/machxo2/top.v(152[9:86])
    defparam dff06.GSR = "DISABLED";
    LUT4 mux_76_i6_3_lut (.A(sramData[5]), .B(n612), .C(ocea_enable_1), 
         .Z(n309)) /* synthesis lut_function=(A (B+(C))+!A !((C)+!B)) */ ;   // v:/cpu2908/fpga/machxo2/top.v(191[2] 192[9])
    defparam mux_76_i6_3_lut.init = 16'hacac;
    FD1P3DX dff07 (.D(n5742), .SP(VCC_net), .CK(nRDRxD), .CD(clkQ_c__inv), 
            .Q(RxDclr)) /* synthesis syn_instantiated=1 */ ;   // v:/cpu2908/fpga/machxo2/top.v(154[9:72])
    defparam dff07.GSR = "DISABLED";
    FD1P3DX clkE_I_0_88 (.D(clkQ_c), .SP(VCC_net), .CK(iclk), .CD(nReset2_N_20), 
            .Q(clkE_c)) /* synthesis syn_instantiated=1 */ ;   // v:/cpu2908/fpga/machxo2/top.v(79[9:71])
    defparam clkE_I_0_88.GSR = "DISABLED";
    sram sramData_7__I_0 (.clkQ_c__inv(clkQ_c__inv), .ocea_enable_1(ocea_enable_1), 
         .nReset2_N_20(nReset2_N_20), .sramWE(sramWE), .n569(n569), .n573(n573), 
         .n577(n577), .n581(n581), .n585(n585), .n589(n589), .n593(n593), 
         .ExDataOut({ExDataOut}), .sramData({sramData}), .GND_net(GND_net), 
         .VCC_net(VCC_net)) /* synthesis NGD_DRC_MASK=1, syn_module_defined=1 */ ;   // v:/cpu2908/fpga/machxo2/top.v(183[6] 184[33])
    core nWR_I_0_84 (.clkQ_c(clkQ_c), .clkE_c(clkE_c), .R(R_adj_564), 
         .nReset2_N_20(nReset2_N_20), .R_adj_121(R), .R_adj_122(R_adj_565), 
         .nReset2(nReset2), .clkQ_c__inv(clkQ_c__inv), .ExDataOut({ExDataOut}), 
         .nTSC_c(nTSC_c), .n865(n865), .nWRTxD(nWRTxD), .ocea_enable_1(ocea_enable_1), 
         .sramWE(sramWE), .subPort({subPort_adj_589}), .n549(n549), .nRDRxD(nRDRxD), 
         .n553(n553), .n929(n929), .nCS_c_0(nCS_c_0), .n4907(n4907), 
         .n5386(n5386), .n561(n561), .n5398(n5398), .n4869(n4869), .n972(n972), 
         .n4(n4), .n31(n31), .n589(n589), .n545(n545), .n557(n557), 
         .n541(n541), .n537(n537), .n534(n534), .n573(n573), .n569(n569), 
         .n585(n585), .n581(n581), .n577(n577), .n593(n593), .n565(n565), 
         .nCS_c_1(nCS_c_1), .ExDataIn({ExDataIn}), .IRQH_c(IRQH_c), .S_c_1(S_c_1), 
         .S_c_0(S_c_0), .nIRQ_c(nIRQ_c), .VCC_net(VCC_net), .clkE_N_18(clkE_N_18), 
         .nReset1(nReset1), .GND_net(GND_net)) /* synthesis syn_module_defined=1 */ ;   // v:/cpu2908/fpga/machxo2/top.v(97[6] 117[2])
    serialRxD rxd01 (.SerialClock2(SerialClock2), .\sig[40] (sig[40]), .GND_net(GND_net), 
            .VCC_net(VCC_net), .RxBusy(RxBusy), .n5742(n5742), .RxD_c(RxD_c), 
            .subPort({subPort_adj_599}), .RxDclr(RxDclr)) /* synthesis syn_module_defined=1 */ ;   // v:/cpu2908/fpga/machxo2/top.v(156[11] 159[66])
    FD1S3AX TxBuff_i0 (.D(ExDataOut[0]), .CK(nWRTxD), .Q(TxBuff[0]));   // v:/cpu2908/fpga/machxo2/top.v(126[8] 128[4])
    defparam TxBuff_i0.GSR = "DISABLED";
    serialTxD txd01 (.TxRdy(TxRdy), .TxD_c(TxD_c), .VCC_net(VCC_net), 
            .SerialClock2(SerialClock2), .n5742(n5742), .TxBuff({TxBuff}), 
            .nWRTxD(nWRTxD)) /* synthesis syn_module_defined=1 */ ;   // v:/cpu2908/fpga/machxo2/top.v(163[11:97])
    bootROM rom0 (.n577(n577), .n581(n581), .n585(n585), .n589(n589), 
            .n593(n593), .bootROM_data({bootROM_data})) /* synthesis NGD_DRC_MASK=1, syn_module_defined=1 */ ;   // v:/cpu2908/fpga/machxo2/top.v(175[9:52])
    LUT4 ExDataIn_7__I_0_i5_4_lut (.A(bootROM_data[4]), .B(ExDataIn_7__N_23[4]), 
         .C(n5382), .D(n31), .Z(ExDataIn[4])) /* synthesis lut_function=(A (B ((D)+!C)+!B !(C))+!A (B (C (D)))) */ ;   // v:/cpu2908/fpga/machxo2/top.v(187[2] 192[9])
    defparam ExDataIn_7__I_0_i5_4_lut.init = 16'hca0a;
    LUT4 mux_77_i5_3_lut (.A(subPort_adj_599[3]), .B(n310), .C(n31_adj_574), 
         .Z(ExDataIn_7__N_23[4])) /* synthesis lut_function=(A (B+!(C))+!A (B (C))) */ ;   // v:/cpu2908/fpga/machxo2/top.v(190[2] 192[9])
    defparam mux_77_i5_3_lut.init = 16'hcaca;
    LUT4 mux_76_i5_3_lut (.A(sramData[4]), .B(n613), .C(ocea_enable_1), 
         .Z(n310)) /* synthesis lut_function=(A (B+(C))+!A !((C)+!B)) */ ;   // v:/cpu2908/fpga/machxo2/top.v(191[2] 192[9])
    defparam mux_76_i5_3_lut.init = 16'hacac;
    LUT4 ExDataIn_7__I_0_i3_4_lut (.A(bootROM_data[2]), .B(ExDataIn_7__N_23[2]), 
         .C(n5382), .D(n31), .Z(ExDataIn[2])) /* synthesis lut_function=(A (B ((D)+!C)+!B !(C))+!A (B (C (D)))) */ ;   // v:/cpu2908/fpga/machxo2/top.v(187[2] 192[9])
    defparam ExDataIn_7__I_0_i3_4_lut.init = 16'hca0a;
    register16_U18 ioaddr_reg (.subPort({subPort}), .clkQ_c__inv(clkQ_c__inv), 
            .n593(n593), .n534(n534), .n537(n537), .n541(n541), .n545(n545), 
            .n549(n549), .n553(n553), .n557(n557), .n561(n561), .n565(n565), 
            .n569(n569), .n573(n573), .n577(n577), .n581(n581), .n585(n585), 
            .n589(n589)) /* synthesis syn_module_defined=1 */ ;   // v:/cpu2908/fpga/machxo2/top.v(146[12:82])
    PFUMX ExDataIn_7__I_0_i4 (.BLUT(n311), .ALUT(ExDataIn_7__N_6[3]), .C0(n4970), 
          .Z(ExDataIn[3]));
    PFUMX ExDataIn_7__I_0_i7 (.BLUT(n308), .ALUT(ExDataIn_7__N_6[6]), .C0(n4970), 
          .Z(ExDataIn[6]));
    PFUMX ExDataIn_7__I_0_i8 (.BLUT(n307), .ALUT(ExDataIn_7__N_6[7]), .C0(n4970), 
          .Z(ExDataIn[7]));
    LUT4 nReset_I_0_1_lut (.A(nReset_c), .Z(nReset_N_22)) /* synthesis lut_function=(!(A)) */ ;   // v:/cpu2908/fpga/machxo2/top.v(82[57:64])
    defparam nReset_I_0_1_lut.init = 16'h5555;
    LUT4 ExDataIn_7__I_1_i4_3_lut (.A(ExDataIn_7__N_23[3]), .B(bootROM_data[3]), 
         .C(n5382), .Z(ExDataIn_7__N_6[3])) /* synthesis lut_function=(A (B+(C))+!A !((C)+!B)) */ ;   // v:/cpu2908/fpga/machxo2/top.v(189[2] 192[9])
    defparam ExDataIn_7__I_1_i4_3_lut.init = 16'hacac;
    LUT4 mux_77_i3_3_lut (.A(subPort_adj_599[5]), .B(n312), .C(n31_adj_574), 
         .Z(ExDataIn_7__N_23[2])) /* synthesis lut_function=(A (B+!(C))+!A (B (C))) */ ;   // v:/cpu2908/fpga/machxo2/top.v(190[2] 192[9])
    defparam mux_77_i3_3_lut.init = 16'hcaca;
    LUT4 i1_4_lut (.A(subPort[0]), .B(n4793), .C(n3115), .D(subPort[8]), 
         .Z(n865)) /* synthesis lut_function=((B+!(C (D)))+!A) */ ;   // v:/cpu2908/fpga/machxo2/top.v(148[17:39])
    defparam i1_4_lut.init = 16'hdfff;
    divider div01 (.clk_c(clk_c), .nReset2_N_20(nReset2_N_20), .SerialClock_c_7(SerialClock_c_7), 
            .GND_net(GND_net)) /* synthesis syn_module_defined=1 */ ;   // v:/cpu2908/fpga/machxo2/top.v(87[9:78])
    FD1S3AX TxBuff_i7 (.D(ExDataOut[7]), .CK(nWRTxD), .Q(TxBuff[7]));   // v:/cpu2908/fpga/machxo2/top.v(126[8] 128[4])
    defparam TxBuff_i7.GSR = "DISABLED";
    FD1S3AX TxBuff_i6 (.D(ExDataOut[6]), .CK(nWRTxD), .Q(TxBuff[6]));   // v:/cpu2908/fpga/machxo2/top.v(126[8] 128[4])
    defparam TxBuff_i6.GSR = "DISABLED";
    FD1S3AX TxBuff_i5 (.D(ExDataOut[5]), .CK(nWRTxD), .Q(TxBuff[5]));   // v:/cpu2908/fpga/machxo2/top.v(126[8] 128[4])
    defparam TxBuff_i5.GSR = "DISABLED";
    LUT4 mux_76_i3_3_lut (.A(sramData[2]), .B(n615), .C(ocea_enable_1), 
         .Z(n312)) /* synthesis lut_function=(A (B+(C))+!A !((C)+!B)) */ ;   // v:/cpu2908/fpga/machxo2/top.v(191[2] 192[9])
    defparam mux_76_i3_3_lut.init = 16'hacac;
    IB RxD_pad (.I(RxD), .O(RxD_c));   // v:/cpu2908/fpga/machxo2/top.v(31[13:16])
    FD1S3AX TxBuff_i4 (.D(ExDataOut[4]), .CK(nWRTxD), .Q(TxBuff[4]));   // v:/cpu2908/fpga/machxo2/top.v(126[8] 128[4])
    defparam TxBuff_i4.GSR = "DISABLED";
    FD1S3AX TxBuff_i3 (.D(ExDataOut[3]), .CK(nWRTxD), .Q(TxBuff[3]));   // v:/cpu2908/fpga/machxo2/top.v(126[8] 128[4])
    defparam TxBuff_i3.GSR = "DISABLED";
    FD1S3AX TxBuff_i2 (.D(ExDataOut[2]), .CK(nWRTxD), .Q(TxBuff[2]));   // v:/cpu2908/fpga/machxo2/top.v(126[8] 128[4])
    defparam TxBuff_i2.GSR = "DISABLED";
    FD1S3AX TxBuff_i1 (.D(ExDataOut[1]), .CK(nWRTxD), .Q(TxBuff[1]));   // v:/cpu2908/fpga/machxo2/top.v(126[8] 128[4])
    defparam TxBuff_i1.GSR = "DISABLED";
    IB nTSC_pad (.I(nTSC), .O(nTSC_c));   // v:/cpu2908/fpga/machxo2/top.v(9[13:17])
    IB nIRQ_pad (.I(nIRQ), .O(nIRQ_c));   // v:/cpu2908/fpga/machxo2/top.v(8[13:17])
    IB nReset_pad (.I(nReset), .O(nReset_c));   // v:/cpu2908/fpga/machxo2/top.v(7[13:19])
    LUT4 i10_4_lut (.A(subPort[6]), .B(n20), .C(n14), .D(subPort[1]), 
         .Z(n22)) /* synthesis lut_function=(A+(B+(C+(D)))) */ ;   // v:/cpu2908/fpga/machxo2/top.v(148[17:39])
    defparam i10_4_lut.init = 16'hfffe;
    LUT4 i4615_3_lut_3_lut (.A(n5382), .B(n31_adj_574), .C(n31), .Z(n4970)) /* synthesis lut_function=(!(A (B (C)))) */ ;   // v:/cpu2908/fpga/machxo2/top.v(187[2] 192[9])
    defparam i4615_3_lut_3_lut.init = 16'h7f7f;
    LUT4 i6_2_lut (.A(subPort[14]), .B(subPort[15]), .Z(n18)) /* synthesis lut_function=(A+(B)) */ ;   // v:/cpu2908/fpga/machxo2/top.v(148[17:39])
    defparam i6_2_lut.init = 16'heeee;
    LUT4 i8_4_lut (.A(subPort[3]), .B(subPort[12]), .C(subPort[5]), .D(subPort[2]), 
         .Z(n20)) /* synthesis lut_function=(A+(B+(C+(D)))) */ ;   // v:/cpu2908/fpga/machxo2/top.v(148[17:39])
    defparam i8_4_lut.init = 16'hfffe;
    IB clk_pad (.I(clk), .O(clk_c));   // v:/cpu2908/fpga/machxo2/top.v(4[13:16])
    OB UM_pad_0 (.I(UM_c), .O(UM[0]));   // v:/cpu2908/fpga/machxo2/top.v(37[19:21])
    OB UM_pad_1 (.I(n616), .O(UM[1]));   // v:/cpu2908/fpga/machxo2/top.v(37[19:21])
    OB UM_pad_2 (.I(n615), .O(UM[2]));   // v:/cpu2908/fpga/machxo2/top.v(37[19:21])
    OB UM_pad_3 (.I(n614), .O(UM[3]));   // v:/cpu2908/fpga/machxo2/top.v(37[19:21])
    OB UM_pad_4 (.I(n613), .O(UM[4]));   // v:/cpu2908/fpga/machxo2/top.v(37[19:21])
    OB UM_pad_5 (.I(n612), .O(UM[5]));   // v:/cpu2908/fpga/machxo2/top.v(37[19:21])
    OB UM_pad_6 (.I(n611), .O(UM[6]));   // v:/cpu2908/fpga/machxo2/top.v(37[19:21])
    OB UM_pad_7 (.I(n610), .O(UM[7]));   // v:/cpu2908/fpga/machxo2/top.v(37[19:21])
    OB SerialClock_pad (.I(SerialClock_c_7), .O(SerialClock));   // v:/cpu2908/fpga/machxo2/top.v(34[14:25])
    OB nRTS_pad (.I(nRTS_c), .O(nRTS));   // v:/cpu2908/fpga/machxo2/top.v(32[14:18])
    OB TxD_pad (.I(TxD_c), .O(TxD));   // v:/cpu2908/fpga/machxo2/top.v(30[14:17])
    OB SPI_CS_pad_0 (.I(GND_net), .O(SPI_CS[0]));   // v:/cpu2908/fpga/machxo2/top.v(28[19:25])
    OB SPI_CS_pad_1 (.I(GND_net), .O(SPI_CS[1]));   // v:/cpu2908/fpga/machxo2/top.v(28[19:25])
    OB SPI_CS_pad_2 (.I(GND_net), .O(SPI_CS[2]));   // v:/cpu2908/fpga/machxo2/top.v(28[19:25])
    OB SPI_CS_pad_3 (.I(GND_net), .O(SPI_CS[3]));   // v:/cpu2908/fpga/machxo2/top.v(28[19:25])
    OB SPI_CS_pad_4 (.I(GND_net), .O(SPI_CS[4]));   // v:/cpu2908/fpga/machxo2/top.v(28[19:25])
    OB SPI_CS_pad_5 (.I(GND_net), .O(SPI_CS[5]));   // v:/cpu2908/fpga/machxo2/top.v(28[19:25])
    OB SPI_MOSI_pad (.I(GND_net), .O(SPI_MOSI));   // v:/cpu2908/fpga/machxo2/top.v(27[14:22])
    OB SPI_MISO_pad (.I(GND_net), .O(SPI_MISO));   // v:/cpu2908/fpga/machxo2/top.v(26[14:22])
    OB SPI_CLK_pad (.I(GND_net), .O(SPI_CLK));   // v:/cpu2908/fpga/machxo2/top.v(25[14:21])
    OB S_pad_0 (.I(S_c_0), .O(S[0]));   // v:/cpu2908/fpga/machxo2/top.v(22[19:20])
    OB S_pad_1 (.I(S_c_1), .O(S[1]));   // v:/cpu2908/fpga/machxo2/top.v(22[19:20])
    OB IRQH_pad (.I(IRQH_c), .O(IRQH));   // v:/cpu2908/fpga/machxo2/top.v(20[14:18])
    OBZ nIRQA_pad (.I(R_adj_565), .T(n5398), .O(nIRQA));   // v:/cpu2908/fpga/machxo2/tristatebuff.v(7[8:9])
    OBZ n607_pad (.I(R_adj_564), .T(n5398), .O(nAltWR));   // v:/cpu2908/fpga/machxo2/tristatebuff.v(7[8:9])
    OBZ n604_pad (.I(R_adj_564), .T(n5398), .O(nWR));   // v:/cpu2908/fpga/machxo2/tristatebuff.v(7[8:9])
    LUT4 i2_2_lut (.A(subPort[4]), .B(subPort[13]), .Z(n14)) /* synthesis lut_function=(A+(B)) */ ;   // v:/cpu2908/fpga/machxo2/top.v(148[17:39])
    defparam i2_2_lut.init = 16'heeee;
    OBZ n601_pad (.I(R), .T(n5398), .O(nAltRD));   // v:/cpu2908/fpga/machxo2/tristatebuff.v(7[8:9])
    OBZ n598_pad (.I(R), .T(n5398), .O(nRD));   // v:/cpu2908/fpga/machxo2/tristatebuff.v(7[8:9])
    OB clkE_pad (.I(clkE_c), .O(clkE));   // v:/cpu2908/fpga/machxo2/top.v(15[14:18])
    OB clkQ_pad (.I(clkQ_c), .O(clkQ));   // v:/cpu2908/fpga/machxo2/top.v(14[14:18])
    OBZ addrOut_pad_0 (.I(subPort_adj_589[0]), .T(n5398), .O(addrOut[0]));   // v:/cpu2908/fpga/machxo2/register.v(112[8:9])
    OBZ addrOut_pad_1 (.I(subPort_adj_589[1]), .T(n5398), .O(addrOut[1]));   // v:/cpu2908/fpga/machxo2/register.v(112[8:9])
    OBZ addrOut_pad_2 (.I(subPort_adj_589[2]), .T(n5398), .O(addrOut[2]));   // v:/cpu2908/fpga/machxo2/register.v(112[8:9])
    OBZ addrOut_pad_3 (.I(subPort_adj_589[3]), .T(n5398), .O(addrOut[3]));   // v:/cpu2908/fpga/machxo2/register.v(112[8:9])
    OBZ addrOut_pad_4 (.I(subPort_adj_589[4]), .T(n5398), .O(addrOut[4]));   // v:/cpu2908/fpga/machxo2/register.v(112[8:9])
    OBZ addrOut_pad_5 (.I(subPort_adj_589[5]), .T(n5398), .O(addrOut[5]));   // v:/cpu2908/fpga/machxo2/register.v(112[8:9])
    OBZ addrOut_pad_6 (.I(subPort_adj_589[6]), .T(n5398), .O(addrOut[6]));   // v:/cpu2908/fpga/machxo2/register.v(112[8:9])
    OBZ addrOut_pad_7 (.I(subPort_adj_589[7]), .T(n5398), .O(addrOut[7]));   // v:/cpu2908/fpga/machxo2/register.v(112[8:9])
    LUT4 ExDataIn_7__I_0_i1_4_lut (.A(bootROM_data[0]), .B(ExDataIn_7__N_23[0]), 
         .C(n5382), .D(n31), .Z(ExDataIn[0])) /* synthesis lut_function=(A (B ((D)+!C)+!B !(C))+!A (B (C (D)))) */ ;   // v:/cpu2908/fpga/machxo2/top.v(187[2] 192[9])
    defparam ExDataIn_7__I_0_i1_4_lut.init = 16'hca0a;
    OBZ addrOut_pad_8 (.I(subPort_adj_589[8]), .T(n5398), .O(addrOut[8]));   // v:/cpu2908/fpga/machxo2/register.v(112[8:9])
    OBZ addrOut_pad_9 (.I(subPort_adj_589[9]), .T(n5398), .O(addrOut[9]));   // v:/cpu2908/fpga/machxo2/register.v(112[8:9])
    OBZ addrOut_pad_10 (.I(subPort_adj_589[10]), .T(n5398), .O(addrOut[10]));   // v:/cpu2908/fpga/machxo2/register.v(112[8:9])
    OBZ addrOut_pad_11 (.I(subPort_adj_589[11]), .T(n5398), .O(addrOut[11]));   // v:/cpu2908/fpga/machxo2/register.v(112[8:9])
    OBZ addrOut_pad_12 (.I(subPort_adj_589[12]), .T(n5398), .O(addrOut[12]));   // v:/cpu2908/fpga/machxo2/register.v(112[8:9])
    OBZ addrOut_pad_13 (.I(subPort_adj_589[13]), .T(n5398), .O(addrOut[13]));   // v:/cpu2908/fpga/machxo2/register.v(112[8:9])
    OBZ addrOut_pad_14 (.I(subPort_adj_589[14]), .T(n5398), .O(addrOut[14]));   // v:/cpu2908/fpga/machxo2/register.v(112[8:9])
    OBZ addrOut_pad_15 (.I(subPort_adj_589[15]), .T(n5398), .O(addrOut[15]));   // v:/cpu2908/fpga/machxo2/register.v(112[8:9])
    OBZ addrOut_pad_16 (.I(GND_net), .T(n531), .O(addrOut[16]));   // v:/cpu2908/fpga/machxo2/top.v(52[8:15])
    OBZ addrOut_pad_17 (.I(GND_net), .T(n531), .O(addrOut[17]));   // v:/cpu2908/fpga/machxo2/top.v(52[8:15])
    OBZ addrOut_pad_18 (.I(GND_net), .T(n531), .O(addrOut[18]));   // v:/cpu2908/fpga/machxo2/top.v(52[8:15])
    OBZ addrOut_pad_19 (.I(GND_net), .T(n531), .O(addrOut[19]));   // v:/cpu2908/fpga/machxo2/top.v(52[8:15])
    OB nCS_pad_0 (.I(nCS_c_0), .O(nCS[0]));   // v:/cpu2908/fpga/machxo2/top.v(3[20:23])
    OB nCS_pad_1 (.I(nCS_c_1), .O(nCS[1]));   // v:/cpu2908/fpga/machxo2/top.v(3[20:23])
    OB nCS_pad_2 (.I(GND_net), .O(nCS[2]));   // v:/cpu2908/fpga/machxo2/top.v(3[20:23])
    OB nCS_pad_3 (.I(GND_net), .O(nCS[3]));   // v:/cpu2908/fpga/machxo2/top.v(3[20:23])
    BB dataBus_pad_0 (.I(ExDataOut[0]), .T(n5386), .B(dataBus[0]), .O(UM_c));   // v:/cpu2908/fpga/machxo2/top.v(53[8:15])
    BB dataBus_pad_1 (.I(ExDataOut[1]), .T(n5386), .B(dataBus[1]), .O(n616));   // v:/cpu2908/fpga/machxo2/top.v(53[8:15])
    BB dataBus_pad_2 (.I(ExDataOut[2]), .T(n5386), .B(dataBus[2]), .O(n615));   // v:/cpu2908/fpga/machxo2/top.v(53[8:15])
    BB dataBus_pad_3 (.I(ExDataOut[3]), .T(n5386), .B(dataBus[3]), .O(n614));   // v:/cpu2908/fpga/machxo2/top.v(53[8:15])
    BB dataBus_pad_4 (.I(ExDataOut[4]), .T(n5386), .B(dataBus[4]), .O(n613));   // v:/cpu2908/fpga/machxo2/top.v(53[8:15])
    BB dataBus_pad_5 (.I(ExDataOut[5]), .T(n5386), .B(dataBus[5]), .O(n612));   // v:/cpu2908/fpga/machxo2/top.v(53[8:15])
    BB dataBus_pad_6 (.I(ExDataOut[6]), .T(n5386), .B(dataBus[6]), .O(n611));   // v:/cpu2908/fpga/machxo2/top.v(53[8:15])
    BB dataBus_pad_7 (.I(ExDataOut[7]), .T(n5386), .B(dataBus[7]), .O(n610));   // v:/cpu2908/fpga/machxo2/top.v(53[8:15])
    LUT4 mux_77_i1_3_lut (.A(subPort_adj_599[7]), .B(n314), .C(n31_adj_574), 
         .Z(ExDataIn_7__N_23[0])) /* synthesis lut_function=(A (B+!(C))+!A (B (C))) */ ;   // v:/cpu2908/fpga/machxo2/top.v(190[2] 192[9])
    defparam mux_77_i1_3_lut.init = 16'hcaca;
    LUT4 mux_76_i1_3_lut (.A(sramData[0]), .B(UM_c), .C(ocea_enable_1), 
         .Z(n314)) /* synthesis lut_function=(A (B+(C))+!A !((C)+!B)) */ ;   // v:/cpu2908/fpga/machxo2/top.v(191[2] 192[9])
    defparam mux_76_i1_3_lut.init = 16'hacac;
    LUT4 i2_4_lut (.A(n4907), .B(n589), .C(n593), .D(n972), .Z(n31_adj_574)) /* synthesis lut_function=(A+(B+((D)+!C))) */ ;   // v:/cpu2908/fpga/machxo2/top.v(190[2:22])
    defparam i2_4_lut.init = 16'hffef;
    LUT4 i431_4_lut_rep_94 (.A(n5398), .B(n921), .C(n10), .D(subPort_adj_589[8]), 
         .Z(n5382)) /* synthesis lut_function=(!(A+!(B+(C+(D))))) */ ;   // v:/cpu2908/fpga/machxo2/top.v(187[2:21])
    defparam i431_4_lut_rep_94.init = 16'h5554;
    LUT4 sig_40__I_0_1_lut (.A(sig[40]), .Z(nRTS_c)) /* synthesis lut_function=(!(A)) */ ;   // v:/cpu2908/fpga/machxo2/top.v(150[15:21])
    defparam sig_40__I_0_1_lut.init = 16'h5555;
    GSR GSR_INST (.GSR(nReset1));
    LUT4 i3_4_lut (.A(subPort_adj_589[14]), .B(subPort_adj_589[13]), .C(subPort_adj_589[12]), 
         .D(subPort_adj_589[15]), .Z(n929)) /* synthesis lut_function=(A+(B+(C+(D)))) */ ;   // v:/cpu2908/fpga/machxo2/top.v(189[2:22])
    defparam i3_4_lut.init = 16'hfffe;
    LUT4 i4_4_lut (.A(subPort_adj_589[9]), .B(n929), .C(subPort_adj_589[10]), 
         .D(subPort_adj_589[11]), .Z(n10)) /* synthesis lut_function=(A+(B+(C+(D)))) */ ;   // v:/cpu2908/fpga/machxo2/top.v(187[2:21])
    defparam i4_4_lut.init = 16'hfffe;
    LUT4 i260_1_lut (.A(nTSC_c), .Z(n531)) /* synthesis lut_function=(!(A)) */ ;   // v:/cpu2908/fpga/machxo2/top.v(52[8:15])
    defparam i260_1_lut.init = 16'h5555;
    LUT4 i1_2_lut (.A(subPort_adj_589[1]), .B(subPort_adj_589[0]), .Z(n4)) /* synthesis lut_function=(A+(B)) */ ;   // v:/cpu2908/fpga/machxo2/top.v(190[2:22])
    defparam i1_2_lut.init = 16'heeee;
    LUT4 i3_4_lut_adj_101 (.A(subPort_adj_589[4]), .B(subPort_adj_589[2]), 
         .C(subPort_adj_589[3]), .D(n921), .Z(n4869)) /* synthesis lut_function=(A+(B+(C+(D)))) */ ;   // v:/cpu2908/fpga/machxo2/top.v(187[2:21])
    defparam i3_4_lut_adj_101.init = 16'hfffe;
    LUT4 i2_3_lut (.A(subPort_adj_589[7]), .B(subPort_adj_589[6]), .C(subPort_adj_589[5]), 
         .Z(n921)) /* synthesis lut_function=(A+(B+(C))) */ ;   // v:/cpu2908/fpga/machxo2/top.v(190[2:22])
    defparam i2_3_lut.init = 16'hfefe;
    LUT4 mux_77_i4_3_lut (.A(subPort_adj_599[4]), .B(TxRdy), .C(n31), 
         .Z(ExDataIn_7__N_23[3])) /* synthesis lut_function=(A (B+(C))+!A !((C)+!B)) */ ;   // v:/cpu2908/fpga/machxo2/top.v(190[2] 192[9])
    defparam mux_77_i4_3_lut.init = 16'hacac;
    LUT4 mux_76_i4_3_lut (.A(sramData[3]), .B(n614), .C(ocea_enable_1), 
         .Z(n311)) /* synthesis lut_function=(A (B+(C))+!A !((C)+!B)) */ ;   // v:/cpu2908/fpga/machxo2/top.v(191[2] 192[9])
    defparam mux_76_i4_3_lut.init = 16'hacac;
    LUT4 clk3_I_0_2_lut (.A(clk3), .B(clk_c), .Z(iclk)) /* synthesis lut_function=(A (B)) */ ;   // v:/cpu2908/fpga/machxo2/top.v(70[15:30])
    defparam clk3_I_0_2_lut.init = 16'h8888;
    LUT4 ExDataIn_7__I_0_i2_4_lut (.A(bootROM_data[1]), .B(ExDataIn_7__N_23[1]), 
         .C(n5382), .D(n31), .Z(ExDataIn[1])) /* synthesis lut_function=(A (B ((D)+!C)+!B !(C))+!A (B (C (D)))) */ ;   // v:/cpu2908/fpga/machxo2/top.v(187[2] 192[9])
    defparam ExDataIn_7__I_0_i2_4_lut.init = 16'hca0a;
    LUT4 ExDataIn_7__I_0_i6_4_lut (.A(bootROM_data[5]), .B(ExDataIn_7__N_23[5]), 
         .C(n5382), .D(n31), .Z(ExDataIn[5])) /* synthesis lut_function=(A (B ((D)+!C)+!B !(C))+!A (B (C (D)))) */ ;   // v:/cpu2908/fpga/machxo2/top.v(187[2] 192[9])
    defparam ExDataIn_7__I_0_i6_4_lut.init = 16'hca0a;
    LUT4 mux_77_i6_3_lut (.A(subPort_adj_599[2]), .B(n309), .C(n31_adj_574), 
         .Z(ExDataIn_7__N_23[5])) /* synthesis lut_function=(A (B+!(C))+!A (B (C))) */ ;   // v:/cpu2908/fpga/machxo2/top.v(190[2] 192[9])
    defparam mux_77_i6_3_lut.init = 16'hcaca;
    LUT4 mux_77_i2_3_lut (.A(subPort_adj_599[6]), .B(n313), .C(n31_adj_574), 
         .Z(ExDataIn_7__N_23[1])) /* synthesis lut_function=(A (B+!(C))+!A (B (C))) */ ;   // v:/cpu2908/fpga/machxo2/top.v(190[2] 192[9])
    defparam mux_77_i2_3_lut.init = 16'hcaca;
    LUT4 mux_76_i2_3_lut (.A(sramData[1]), .B(n616), .C(ocea_enable_1), 
         .Z(n313)) /* synthesis lut_function=(A (B+(C))+!A !((C)+!B)) */ ;   // v:/cpu2908/fpga/machxo2/top.v(191[2] 192[9])
    defparam mux_76_i2_3_lut.init = 16'hacac;
    LUT4 mux_76_i7_3_lut (.A(sramData[6]), .B(n611), .C(ocea_enable_1), 
         .Z(n308)) /* synthesis lut_function=(A (B+(C))+!A !((C)+!B)) */ ;   // v:/cpu2908/fpga/machxo2/top.v(191[2] 192[9])
    defparam mux_76_i7_3_lut.init = 16'hacac;
    LUT4 ExDataIn_7__I_1_i7_3_lut (.A(ExDataIn_7__N_23[6]), .B(bootROM_data[6]), 
         .C(n5382), .Z(ExDataIn_7__N_6[6])) /* synthesis lut_function=(A (B+(C))+!A !((C)+!B)) */ ;   // v:/cpu2908/fpga/machxo2/top.v(189[2] 192[9])
    defparam ExDataIn_7__I_1_i7_3_lut.init = 16'hacac;
    INV i4930 (.A(clkE_c), .Z(clkE_N_18));
    LUT4 mux_77_i7_3_lut (.A(subPort_adj_599[1]), .B(sig[40]), .C(n31), 
         .Z(ExDataIn_7__N_23[6])) /* synthesis lut_function=(A (B+(C))+!A !((C)+!B)) */ ;   // v:/cpu2908/fpga/machxo2/top.v(190[2] 192[9])
    defparam mux_77_i7_3_lut.init = 16'hacac;
    VLO i1 (.Z(GND_net));
    LUT4 mux_76_i8_3_lut (.A(sramData[7]), .B(n610), .C(ocea_enable_1), 
         .Z(n307)) /* synthesis lut_function=(A (B+(C))+!A !((C)+!B)) */ ;   // v:/cpu2908/fpga/machxo2/top.v(191[2] 192[9])
    defparam mux_76_i8_3_lut.init = 16'hacac;
    TSALL TSALL_INST (.TSALL(GND_net));
    LUT4 ExDataIn_7__I_1_i8_3_lut (.A(ExDataIn_7__N_23[7]), .B(bootROM_data[7]), 
         .C(n5382), .Z(ExDataIn_7__N_6[7])) /* synthesis lut_function=(A (B+(C))+!A !((C)+!B)) */ ;   // v:/cpu2908/fpga/machxo2/top.v(189[2] 192[9])
    defparam ExDataIn_7__I_1_i8_3_lut.init = 16'hacac;
    LUT4 mux_77_i8_3_lut (.A(subPort_adj_599[0]), .B(RxBusy), .C(n31), 
         .Z(ExDataIn_7__N_23[7])) /* synthesis lut_function=(A (B+(C))+!A !((C)+!B)) */ ;   // v:/cpu2908/fpga/machxo2/top.v(190[2] 192[9])
    defparam mux_77_i8_3_lut.init = 16'hacac;
    PUR PUR_INST (.PUR(VCC_net));
    defparam PUR_INST.RST_PULSE = 1;
    LUT4 i11_4_lut (.A(subPort[7]), .B(n22), .C(n18), .D(subPort[11]), 
         .Z(n4793)) /* synthesis lut_function=(A+(B+(C+!(D)))) */ ;   // v:/cpu2908/fpga/machxo2/top.v(148[17:39])
    defparam i11_4_lut.init = 16'hfeff;
    LUT4 i2669_2_lut (.A(subPort[10]), .B(subPort[9]), .Z(n3115)) /* synthesis lut_function=(A (B)) */ ;
    defparam i2669_2_lut.init = 16'h8888;
    LUT4 m1_lut (.Z(n5742)) /* synthesis lut_function=1, syn_instantiated=1 */ ;
    defparam m1_lut.init = 16'hffff;
    
endmodule
//
// Verilog Description of module sram
//

module sram (clkQ_c__inv, ocea_enable_1, nReset2_N_20, sramWE, n569, 
            n573, n577, n581, n585, n589, n593, ExDataOut, sramData, 
            GND_net, VCC_net) /* synthesis NGD_DRC_MASK=1, syn_module_defined=1 */ ;
    input clkQ_c__inv;
    input ocea_enable_1;
    input nReset2_N_20;
    input sramWE;
    input n569;
    input n573;
    input n577;
    input n581;
    input n585;
    input n589;
    input n593;
    input [7:0]ExDataOut;
    output [7:0]sramData;
    input GND_net;
    input VCC_net;
    
    wire clkQ_c__inv /* synthesis is_inv_clock=1, is_clock=1 */ ;   // v:/cpu2908/fpga/machxo2/top.v(14[14:18])
    
    DP8KC sram_0_0_0_0 (.DIA0(ExDataOut[0]), .DIA1(ExDataOut[1]), .DIA2(ExDataOut[2]), 
          .DIA3(ExDataOut[3]), .DIA4(ExDataOut[4]), .DIA5(ExDataOut[5]), 
          .DIA6(ExDataOut[6]), .DIA7(ExDataOut[7]), .DIA8(GND_net), .ADA0(VCC_net), 
          .ADA1(GND_net), .ADA2(GND_net), .ADA3(n593), .ADA4(n589), 
          .ADA5(n585), .ADA6(n581), .ADA7(n577), .ADA8(n573), .ADA9(n569), 
          .ADA10(GND_net), .ADA11(GND_net), .ADA12(GND_net), .CEA(ocea_enable_1), 
          .OCEA(ocea_enable_1), .CLKA(clkQ_c__inv), .WEA(sramWE), .CSA0(GND_net), 
          .CSA1(GND_net), .CSA2(GND_net), .RSTA(nReset2_N_20), .DIB0(GND_net), 
          .DIB1(GND_net), .DIB2(GND_net), .DIB3(GND_net), .DIB4(GND_net), 
          .DIB5(GND_net), .DIB6(GND_net), .DIB7(GND_net), .DIB8(GND_net), 
          .ADB0(GND_net), .ADB1(GND_net), .ADB2(GND_net), .ADB3(GND_net), 
          .ADB4(GND_net), .ADB5(GND_net), .ADB6(GND_net), .ADB7(GND_net), 
          .ADB8(GND_net), .ADB9(GND_net), .ADB10(GND_net), .ADB11(GND_net), 
          .ADB12(GND_net), .CEB(VCC_net), .OCEB(VCC_net), .CLKB(GND_net), 
          .WEB(GND_net), .CSB0(GND_net), .CSB1(GND_net), .CSB2(GND_net), 
          .RSTB(GND_net), .DOA0(sramData[0]), .DOA1(sramData[1]), .DOA2(sramData[2]), 
          .DOA3(sramData[3]), .DOA4(sramData[4]), .DOA5(sramData[5]), 
          .DOA6(sramData[6]), .DOA7(sramData[7])) /* synthesis MEM_LPC_FILE="sram.lpc", MEM_INIT_FILE="INIT_ALL_0s", syn_instantiated=1, LSE_LINE_FILE_ID=3, LSE_LCOL=6, LSE_RCOL=33, LSE_LLINE=183, LSE_RLINE=184 */ ;   // v:/cpu2908/fpga/machxo2/top.v(183[6] 184[33])
    defparam sram_0_0_0_0.DATA_WIDTH_A = 9;
    defparam sram_0_0_0_0.DATA_WIDTH_B = 9;
    defparam sram_0_0_0_0.REGMODE_A = "NOREG";
    defparam sram_0_0_0_0.REGMODE_B = "NOREG";
    defparam sram_0_0_0_0.CSDECODE_A = "0b000";
    defparam sram_0_0_0_0.CSDECODE_B = "0b111";
    defparam sram_0_0_0_0.WRITEMODE_A = "NORMAL";
    defparam sram_0_0_0_0.WRITEMODE_B = "NORMAL";
    defparam sram_0_0_0_0.GSR = "ENABLED";
    defparam sram_0_0_0_0.RESETMODE = "ASYNC";
    defparam sram_0_0_0_0.ASYNC_RESET_RELEASE = "SYNC";
    defparam sram_0_0_0_0.INIT_DATA = "STATIC";
    defparam sram_0_0_0_0.INITVAL_00 = "0x00000000000000000000000000000000000000000000000000000000000000000000000000000000";
    defparam sram_0_0_0_0.INITVAL_01 = "0x00000000000000000000000000000000000000000000000000000000000000000000000000000000";
    defparam sram_0_0_0_0.INITVAL_02 = "0x00000000000000000000000000000000000000000000000000000000000000000000000000000000";
    defparam sram_0_0_0_0.INITVAL_03 = "0x00000000000000000000000000000000000000000000000000000000000000000000000000000000";
    defparam sram_0_0_0_0.INITVAL_04 = "0x00000000000000000000000000000000000000000000000000000000000000000000000000000000";
    defparam sram_0_0_0_0.INITVAL_05 = "0x00000000000000000000000000000000000000000000000000000000000000000000000000000000";
    defparam sram_0_0_0_0.INITVAL_06 = "0x00000000000000000000000000000000000000000000000000000000000000000000000000000000";
    defparam sram_0_0_0_0.INITVAL_07 = "0x00000000000000000000000000000000000000000000000000000000000000000000000000000000";
    defparam sram_0_0_0_0.INITVAL_08 = "0x00000000000000000000000000000000000000000000000000000000000000000000000000000000";
    defparam sram_0_0_0_0.INITVAL_09 = "0x00000000000000000000000000000000000000000000000000000000000000000000000000000000";
    defparam sram_0_0_0_0.INITVAL_0A = "0x00000000000000000000000000000000000000000000000000000000000000000000000000000000";
    defparam sram_0_0_0_0.INITVAL_0B = "0x00000000000000000000000000000000000000000000000000000000000000000000000000000000";
    defparam sram_0_0_0_0.INITVAL_0C = "0x00000000000000000000000000000000000000000000000000000000000000000000000000000000";
    defparam sram_0_0_0_0.INITVAL_0D = "0x00000000000000000000000000000000000000000000000000000000000000000000000000000000";
    defparam sram_0_0_0_0.INITVAL_0E = "0x00000000000000000000000000000000000000000000000000000000000000000000000000000000";
    defparam sram_0_0_0_0.INITVAL_0F = "0x00000000000000000000000000000000000000000000000000000000000000000000000000000000";
    defparam sram_0_0_0_0.INITVAL_10 = "0x00000000000000000000000000000000000000000000000000000000000000000000000000000000";
    defparam sram_0_0_0_0.INITVAL_11 = "0x00000000000000000000000000000000000000000000000000000000000000000000000000000000";
    defparam sram_0_0_0_0.INITVAL_12 = "0x00000000000000000000000000000000000000000000000000000000000000000000000000000000";
    defparam sram_0_0_0_0.INITVAL_13 = "0x00000000000000000000000000000000000000000000000000000000000000000000000000000000";
    defparam sram_0_0_0_0.INITVAL_14 = "0x00000000000000000000000000000000000000000000000000000000000000000000000000000000";
    defparam sram_0_0_0_0.INITVAL_15 = "0x00000000000000000000000000000000000000000000000000000000000000000000000000000000";
    defparam sram_0_0_0_0.INITVAL_16 = "0x00000000000000000000000000000000000000000000000000000000000000000000000000000000";
    defparam sram_0_0_0_0.INITVAL_17 = "0x00000000000000000000000000000000000000000000000000000000000000000000000000000000";
    defparam sram_0_0_0_0.INITVAL_18 = "0x00000000000000000000000000000000000000000000000000000000000000000000000000000000";
    defparam sram_0_0_0_0.INITVAL_19 = "0x00000000000000000000000000000000000000000000000000000000000000000000000000000000";
    defparam sram_0_0_0_0.INITVAL_1A = "0x00000000000000000000000000000000000000000000000000000000000000000000000000000000";
    defparam sram_0_0_0_0.INITVAL_1B = "0x00000000000000000000000000000000000000000000000000000000000000000000000000000000";
    defparam sram_0_0_0_0.INITVAL_1C = "0x00000000000000000000000000000000000000000000000000000000000000000000000000000000";
    defparam sram_0_0_0_0.INITVAL_1D = "0x00000000000000000000000000000000000000000000000000000000000000000000000000000000";
    defparam sram_0_0_0_0.INITVAL_1E = "0x00000000000000000000000000000000000000000000000000000000000000000000000000000000";
    defparam sram_0_0_0_0.INITVAL_1F = "0x00000000000000000000000000000000000000000000000000000000000000000000000000000000";
    
endmodule
//
// Verilog Description of module core
//

module core (clkQ_c, clkE_c, R, nReset2_N_20, R_adj_121, R_adj_122, 
            nReset2, clkQ_c__inv, ExDataOut, nTSC_c, n865, nWRTxD, 
            ocea_enable_1, sramWE, subPort, n549, nRDRxD, n553, 
            n929, nCS_c_0, n4907, n5386, n561, n5398, n4869, n972, 
            n4, n31, n589, n545, n557, n541, n537, n534, n573, 
            n569, n585, n581, n577, n593, n565, nCS_c_1, ExDataIn, 
            IRQH_c, S_c_1, S_c_0, nIRQ_c, VCC_net, clkE_N_18, nReset1, 
            GND_net) /* synthesis syn_module_defined=1 */ ;
    input clkQ_c;
    input clkE_c;
    output R;
    output nReset2_N_20;
    output R_adj_121;
    output R_adj_122;
    input nReset2;
    input clkQ_c__inv;
    output [7:0]ExDataOut;
    input nTSC_c;
    input n865;
    output nWRTxD;
    output ocea_enable_1;
    output sramWE;
    output [15:0]subPort;
    output n549;
    output nRDRxD;
    output n553;
    input n929;
    output nCS_c_0;
    output n4907;
    output n5386;
    output n561;
    output n5398;
    input n4869;
    output n972;
    input n4;
    output n31;
    output n589;
    output n545;
    output n557;
    output n541;
    output n537;
    output n534;
    output n573;
    output n569;
    output n585;
    output n581;
    output n577;
    output n593;
    output n565;
    output nCS_c_1;
    input [7:0]ExDataIn;
    output IRQH_c;
    output S_c_1;
    output S_c_0;
    input nIRQ_c;
    input VCC_net;
    input clkE_N_18;
    input nReset1;
    input GND_net;
    
    wire clkQ_c /* synthesis is_clock=1 */ ;   // v:/cpu2908/fpga/machxo2/top.v(14[14:18])
    wire clkE_c /* synthesis is_clock=1 */ ;   // v:/cpu2908/fpga/machxo2/top.v(15[14:18])
    wire N_34 /* synthesis is_clock=1, SET_AS_NETWORK=\nWR_I_0_84/Executer/Executer_s/N_34 */ ;   // v:/cpu2908/fpga/machxo2/impl1/executer_s.v(38[6:10])
    wire clkQ_c__inv /* synthesis is_inv_clock=1, is_clock=1 */ ;   // v:/cpu2908/fpga/machxo2/top.v(14[14:18])
    wire nWRTxD /* synthesis is_clock=1, SET_AS_NETWORK=nWRTxD */ ;   // v:/cpu2908/fpga/machxo2/top.v(124[6:12])
    wire nRDRxD /* synthesis is_clock=1, SET_AS_NETWORK=nRDRxD */ ;   // v:/cpu2908/fpga/machxo2/top.v(123[6:12])
    wire clkE_N_18 /* synthesis is_inv_clock=1 */ ;   // v:/cpu2908/fpga/machxo2/top.v(14[14:18])
    wire [127:0]sig;   // v:/cpu2908/fpga/machxo2/core.v(20[21:24])
    
    wire nread_ff_N_58, n5395, data_ctrl_N_62, nirq_ff_N_64;
    wire [7:0]subPort_c;   // v:/cpu2908/fpga/machxo2/register.v(49[19:26])
    wire [7:0]data_ibus;   // v:/cpu2908/fpga/machxo2/core.v(48[12:21])
    
    wire R_adj_516;
    wire [15:0]addr_ibus;   // v:/cpu2908/fpga/machxo2/core.v(45[13:22])
    
    wire n7;
    wire [7:0]subPort_adj_544;   // v:/cpu2908/fpga/machxo2/register.v(49[19:26])
    wire [3:0]outreg;   // v:/cpu2908/fpga/machxo2/executer.v(109[11:17])
    wire [7:0]InternalDataBus;   // v:/cpu2908/fpga/machxo2/impl1/executer_s.v(35[14:29])
    wire [7:0]addrLo;   // v:/cpu2908/fpga/machxo2/impl1/executer_s.v(31[14:20])
    wire [7:0]addrHi;   // v:/cpu2908/fpga/machxo2/impl1/executer_s.v(30[14:20])
    
    wire n68;
    wire [7:0]subPort_adj_545;   // v:/cpu2908/fpga/machxo2/register.v(49[19:26])
    wire [7:0]subPort_adj_546;   // v:/cpu2908/fpga/machxo2/register.v(49[19:26])
    
    wire n5388, n1, n1_adj_530, n1_adj_532, n1_adj_534, n1_adj_536, 
        n5389;
    wire [7:0]subPort_adj_547;   // v:/cpu2908/fpga/machxo2/register.v(49[19:26])
    
    wire n5, clkQ_c_derived_27_enable_9, clkQ_c_derived_27_enable_5, n7_adj_539, 
        n7_adj_540, n7_adj_541, n7_adj_542;
    wire [7:0]data_es_bus;   // v:/cpu2908/fpga/machxo2/core.v(51[12:23])
    
    LUT4 i4574_2_lut (.A(sig[32]), .B(sig[33]), .Z(nread_ff_N_58)) /* synthesis lut_function=((B)+!A) */ ;   // v:/cpu2908/fpga/machxo2/core.v(69[26:59])
    defparam i4574_2_lut.init = 16'hdddd;
    LUT4 data_ctrl_I_2_2_lut_rep_107 (.A(sig[32]), .B(sig[33]), .Z(n5395)) /* synthesis lut_function=(!(A+!(B))) */ ;   // v:/cpu2908/fpga/machxo2/core.v(70[27:59])
    defparam data_ctrl_I_2_2_lut_rep_107.init = 16'h4444;
    LUT4 data_ctrl_N_50_I_0_1_lut_2_lut (.A(sig[32]), .B(sig[33]), .Z(data_ctrl_N_62)) /* synthesis lut_function=(A+!(B)) */ ;   // v:/cpu2908/fpga/machxo2/core.v(70[27:59])
    defparam data_ctrl_N_50_I_0_1_lut_2_lut.init = 16'hbbbb;
    LUT4 i4577_2_lut (.A(sig[32]), .B(sig[33]), .Z(nirq_ff_N_64)) /* synthesis lut_function=(!(A (B))) */ ;   // v:/cpu2908/fpga/machxo2/core.v(71[26:58])
    defparam i4577_2_lut.init = 16'h7777;
    LUT4 i2_3_lut_3_lut (.A(clkQ_c), .B(sig[84]), .C(clkE_c), .Z(N_34)) /* synthesis lut_function=(!(A+!(B (C)))) */ ;   // v:/cpu2908/fpga/machxo2/top.v(146[38:43])
    defparam i2_3_lut_3_lut.init = 16'h4040;
    register1as nwrite_ff_I_0 (.R(R), .clkE_c(clkE_c), .nReset2_N_20(nReset2_N_20), 
            .data_ctrl_N_62(data_ctrl_N_62)) /* synthesis syn_module_defined=1 */ ;   // v:/cpu2908/fpga/machxo2/core.v(70[13:124])
    register1as_U13 nread_ff_I_0 (.R(R_adj_121), .clkE_c(clkE_c), .nReset2_N_20(nReset2_N_20), 
            .nread_ff_N_58(nread_ff_N_58)) /* synthesis syn_module_defined=1 */ ;   // v:/cpu2908/fpga/machxo2/core.v(69[13:123])
    register1as_U14 nirq_ff_I_0 (.R(R_adj_122), .clkE_c(clkE_c), .nReset2_N_20(nReset2_N_20), 
            .nirq_ff_N_64(nirq_ff_N_64), .nReset2(nReset2)) /* synthesis syn_module_defined=1 */ ;   // v:/cpu2908/fpga/machxo2/core.v(71[13:121])
    register8_U15 data_ibus2_7__I_0 (.subPort({subPort_c}), .clkE_c(clkE_c), 
            .\sig[34] (sig[34]), .data_ibus({data_ibus})) /* synthesis syn_module_defined=1 */ ;   // v:/cpu2908/fpga/machxo2/core.v(62[11:97])
    register1 data_ctrl_I_0_25 (.R(R_adj_516), .clkQ_c__inv(clkQ_c__inv), 
            .n5395(n5395)) /* synthesis syn_module_defined=1 */ ;   // v:/cpu2908/fpga/machxo2/core.v(79[11:108])
    tristateBuff8_U16 dataOut_7__I_0 (.subPort({subPort_c}), .R(R_adj_516), 
            .ExDataOut({ExDataOut})) /* synthesis syn_module_defined=1 */ ;   // v:/cpu2908/fpga/machxo2/core.v(63[15:71])
    register16_U17 addrOut_15__I_0 (.nTSC_c(nTSC_c), .nReset2(nReset2), 
            .n865(n865), .R(R), .nWRTxD(nWRTxD), .ocea_enable_1(ocea_enable_1), 
            .sramWE(sramWE), .subPort({subPort}), .n549(n549), .R_adj_120(R_adj_121), 
            .nRDRxD(nRDRxD), .n553(n553), .n929(n929), .nCS_c_0(nCS_c_0), 
            .clkE_c(clkE_c), .\sig[35] (sig[35]), .addr_ibus({addr_ibus}), 
            .n4907(n4907), .n5386(n5386), .n561(n561), .n5398(n5398), 
            .n4869(n4869), .n972(n972), .n4(n4), .n31(n31), .n589(n589), 
            .n545(n545), .n557(n557), .n541(n541), .n537(n537), .n534(n534), 
            .n573(n573), .n569(n569), .n585(n585), .n581(n581), .n577(n577), 
            .n593(n593), .n565(n565), .nCS_c_1(nCS_c_1)) /* synthesis syn_module_defined=1 */ ;   // v:/cpu2908/fpga/machxo2/core.v(66[13:97])
    sequencer Sequencer (.ExDataIn({ExDataIn}), .\sig[45] (sig[45]), .IRQH_c(IRQH_c), 
            .S_c_1(S_c_1), .S_c_0(S_c_0), .clkE_c(clkE_c), .nIRQ_c(nIRQ_c), 
            .VCC_net(VCC_net), .clkE_N_18(clkE_N_18), .clkQ_c(clkQ_c), 
            .\sig[44] (sig[44]), .\sig[47] (sig[47]), .\sig[46] (sig[46]), 
            .clkQ_c__inv(clkQ_c__inv), .nReset2(nReset2), .nReset1(nReset1), 
            .\sig[43] (sig[43]), .\sig[35] (sig[35]), .\sig[34] (sig[34]), 
            .\sig[33] (sig[33]), .\sig[32] (sig[32]), .\sig[94] (sig[94]), 
            .\sig[93] (sig[93]), .\sig[91] (sig[91]), .\sig[90] (sig[90]), 
            .\sig[89] (sig[89]), .\sig[88] (sig[88]), .\sig[87] (sig[87]), 
            .\sig[86] (sig[86]), .\sig[85] (sig[85]), .\sig[84] (sig[84]), 
            .\sig[83] (sig[83]), .\sig[82] (sig[82]), .\sig[81] (sig[81]), 
            .\sig[80] (sig[80]), .\sig[79] (sig[79]), .\data_ibus[1] (data_ibus[1]), 
            .n7(n7), .\sig[78] (sig[78]), .\sig[77] (sig[77]), .\sig[76] (sig[76]), 
            .\sig[75] (sig[75]), .\sig[74] (sig[74]), .\sig[73] (sig[73]), 
            .\sig[72] (sig[72]), .\subPort[4] (subPort_adj_544[4]), .\outreg[1] (outreg[1]), 
            .\InternalDataBus[4] (InternalDataBus[4]), .\addrLo[4] (addrLo[4]), 
            .\addrHi[4] (addrHi[4]), .n68(n68), .\subPort[4]_adj_109 (subPort_adj_545[4]), 
            .\subPort[4]_adj_110 (subPort_adj_546[4]), .\outreg[2] (outreg[2]), 
            .n5388(n5388), .\subPort[2] (subPort_adj_545[2]), .n1(n1), 
            .\subPort[1] (subPort_adj_545[1]), .n1_adj_111(n1_adj_530), 
            .\subPort[7] (subPort_adj_545[7]), .n1_adj_112(n1_adj_532), 
            .\subPort[0] (subPort_adj_545[0]), .n1_adj_113(n1_adj_534), 
            .\subPort[6] (subPort_adj_545[6]), .n1_adj_114(n1_adj_536), 
            .n5389(n5389), .\data_ibus[4] (data_ibus[4]), .\subPort[4]_adj_115 (subPort_adj_547[4]), 
            .\addrLo[3] (addrLo[3]), .n5(n5), .clkQ_c_derived_27_enable_9(clkQ_c_derived_27_enable_9), 
            .clkQ_c_derived_27_enable_5(clkQ_c_derived_27_enable_5), .\subPort[5] (subPort_adj_547[5]), 
            .\data_ibus[6] (data_ibus[6]), .n7_adj_116(n7_adj_539), .\data_ibus[7] (data_ibus[7]), 
            .n7_adj_117(n7_adj_540), .\data_ibus[2] (data_ibus[2]), .n7_adj_118(n7_adj_541), 
            .\data_ibus[0] (data_ibus[0]), .n7_adj_119(n7_adj_542), .\data_es_bus[6] (data_es_bus[6]), 
            .\data_es_bus[7] (data_es_bus[7]), .\data_es_bus[3] (data_es_bus[3]), 
            .\data_es_bus[2] (data_es_bus[2]), .\data_es_bus[1] (data_es_bus[1]), 
            .\data_es_bus[0] (data_es_bus[0]), .GND_net(GND_net)) /* synthesis syn_module_defined=1 */ ;   // v:/cpu2908/fpga/machxo2/core.v(86[11] 104[2])
    executer Executer (.\sig[73] (sig[73]), .\sig[43] (sig[43]), .\sig[72] (sig[72]), 
            .\sig[80] (sig[80]), .\data_es_bus[2] (data_es_bus[2]), .\sig[79] (sig[79]), 
            .\outreg[2] (outreg[2]), .n5389(n5389), .\outreg[1] (outreg[1]), 
            .n68(n68), .n5388(n5388), .N_34(N_34), .data_ibus({data_ibus}), 
            .\data_es_bus[0] (data_es_bus[0]), .\sig[81] (sig[81]), .\data_es_bus[3] (data_es_bus[3]), 
            .\data_es_bus[7] (data_es_bus[7]), .\data_es_bus[1] (data_es_bus[1]), 
            .\data_es_bus[6] (data_es_bus[6]), .\subPort[4] (subPort_adj_547[4]), 
            .\subPort[5] (subPort_adj_547[5]), .n5(n5), .n1(n1_adj_536), 
            .n7(n7_adj_539), .n1_adj_76(n1_adj_530), .n7_adj_77(n7), .n1_adj_78(n1_adj_532), 
            .n7_adj_79(n7_adj_540), .n1_adj_80(n1), .n7_adj_81(n7_adj_541), 
            .n1_adj_82(n1_adj_534), .n7_adj_83(n7_adj_542), .\subPort[4]_adj_84 (subPort_adj_546[4]), 
            .\subPort[4]_adj_85 (subPort_adj_544[4]), .\subPort[0] (subPort_adj_545[0]), 
            .\subPort[1] (subPort_adj_545[1]), .\subPort[2] (subPort_adj_545[2]), 
            .\subPort[4]_adj_86 (subPort_adj_545[4]), .\subPort[6] (subPort_adj_545[6]), 
            .\subPort[7] (subPort_adj_545[7]), .\sig[85] (sig[85]), .\sig[84] (sig[84]), 
            .\sig[87] (sig[87]), .\sig[86] (sig[86]), .\sig[83] (sig[83]), 
            .\sig[82] (sig[82]), .addr_ibus({addr_ibus}), .\addrLo[3] (addrLo[3]), 
            .\addrHi[4] (addrHi[4]), .\addrLo[4] (addrLo[4]), .\sig[93] (sig[93]), 
            .\sig[94] (sig[94]), .\sig[46] (sig[46]), .\sig[45] (sig[45]), 
            .\sig[44] (sig[44]), .\sig[47] (sig[47]), .\InternalDataBus[4] (InternalDataBus[4]), 
            .\sig[77] (sig[77]), .\sig[75] (sig[75]), .\sig[76] (sig[76]), 
            .\sig[74] (sig[74]), .\sig[78] (sig[78]), .GND_net(GND_net), 
            .clkQ_c__inv(clkQ_c__inv), .clkQ_c_derived_27_enable_9(clkQ_c_derived_27_enable_9), 
            .clkQ_c_derived_27_enable_5(clkQ_c_derived_27_enable_5), .\sig[88] (sig[88]), 
            .\sig[89] (sig[89]), .\sig[90] (sig[90]), .\sig[91] (sig[91]), 
            .clkQ_c(clkQ_c)) /* synthesis syn_module_defined=1 */ ;   // v:/cpu2908/fpga/machxo2/core.v(107[10] 119[2])
    
endmodule
//
// Verilog Description of module register1as
//

module register1as (R, clkE_c, nReset2_N_20, data_ctrl_N_62) /* synthesis syn_module_defined=1 */ ;
    output R;
    input clkE_c;
    input nReset2_N_20;
    input data_ctrl_N_62;
    
    wire clkE_c /* synthesis is_clock=1 */ ;   // v:/cpu2908/fpga/machxo2/top.v(15[14:18])
    
    FD1S3BX R_15 (.D(data_ctrl_N_62), .CK(clkE_c), .PD(nReset2_N_20), 
            .Q(R)) /* synthesis LSE_LINE_FILE_ID=4, LSE_LCOL=13, LSE_RCOL=124, LSE_LLINE=70, LSE_RLINE=70 */ ;   // v:/cpu2908/fpga/machxo2/register.v(36[3:22])
    defparam R_15.GSR = "DISABLED";
    
endmodule
//
// Verilog Description of module register1as_U13
//

module register1as_U13 (R, clkE_c, nReset2_N_20, nread_ff_N_58) /* synthesis syn_module_defined=1 */ ;
    output R;
    input clkE_c;
    input nReset2_N_20;
    input nread_ff_N_58;
    
    wire clkE_c /* synthesis is_clock=1 */ ;   // v:/cpu2908/fpga/machxo2/top.v(15[14:18])
    
    FD1S3BX R_15 (.D(nread_ff_N_58), .CK(clkE_c), .PD(nReset2_N_20), .Q(R)) /* synthesis LSE_LINE_FILE_ID=4, LSE_LCOL=13, LSE_RCOL=123, LSE_LLINE=69, LSE_RLINE=69 */ ;   // v:/cpu2908/fpga/machxo2/register.v(36[3:22])
    defparam R_15.GSR = "DISABLED";
    
endmodule
//
// Verilog Description of module register1as_U14
//

module register1as_U14 (R, clkE_c, nReset2_N_20, nirq_ff_N_64, nReset2) /* synthesis syn_module_defined=1 */ ;
    output R;
    input clkE_c;
    output nReset2_N_20;
    input nirq_ff_N_64;
    input nReset2;
    
    wire clkE_c /* synthesis is_clock=1 */ ;   // v:/cpu2908/fpga/machxo2/top.v(15[14:18])
    
    FD1S3BX R_15 (.D(nirq_ff_N_64), .CK(clkE_c), .PD(nReset2_N_20), .Q(R)) /* synthesis LSE_LINE_FILE_ID=4, LSE_LCOL=13, LSE_RCOL=121, LSE_LLINE=71, LSE_RLINE=71 */ ;   // v:/cpu2908/fpga/machxo2/register.v(36[3:22])
    defparam R_15.GSR = "DISABLED";
    LUT4 nReset2_I_0_1_lut (.A(nReset2), .Z(nReset2_N_20)) /* synthesis lut_function=(!(A)) */ ;   // v:/cpu2908/fpga/machxo2/top.v(80[51:59])
    defparam nReset2_I_0_1_lut.init = 16'h5555;
    
endmodule
//
// Verilog Description of module register8_U15
//

module register8_U15 (subPort, clkE_c, \sig[34] , data_ibus) /* synthesis syn_module_defined=1 */ ;
    output [7:0]subPort;
    input clkE_c;
    input \sig[34] ;
    input [7:0]data_ibus;
    
    wire clkE_c /* synthesis is_clock=1 */ ;   // v:/cpu2908/fpga/machxo2/top.v(15[14:18])
    
    FD1P3AX R_i0_i0 (.D(data_ibus[0]), .SP(\sig[34] ), .CK(clkE_c), .Q(subPort[0])) /* synthesis LSE_LINE_FILE_ID=4, LSE_LCOL=11, LSE_RCOL=97, LSE_LLINE=62, LSE_RLINE=62 */ ;   // v:/cpu2908/fpga/machxo2/register.v(57[8] 59[4])
    defparam R_i0_i0.GSR = "DISABLED";
    FD1P3AX R_i0_i1 (.D(data_ibus[1]), .SP(\sig[34] ), .CK(clkE_c), .Q(subPort[1])) /* synthesis LSE_LINE_FILE_ID=4, LSE_LCOL=11, LSE_RCOL=97, LSE_LLINE=62, LSE_RLINE=62 */ ;   // v:/cpu2908/fpga/machxo2/register.v(57[8] 59[4])
    defparam R_i0_i1.GSR = "DISABLED";
    FD1P3AX R_i0_i2 (.D(data_ibus[2]), .SP(\sig[34] ), .CK(clkE_c), .Q(subPort[2])) /* synthesis LSE_LINE_FILE_ID=4, LSE_LCOL=11, LSE_RCOL=97, LSE_LLINE=62, LSE_RLINE=62 */ ;   // v:/cpu2908/fpga/machxo2/register.v(57[8] 59[4])
    defparam R_i0_i2.GSR = "DISABLED";
    FD1P3AX R_i0_i3 (.D(data_ibus[3]), .SP(\sig[34] ), .CK(clkE_c), .Q(subPort[3])) /* synthesis LSE_LINE_FILE_ID=4, LSE_LCOL=11, LSE_RCOL=97, LSE_LLINE=62, LSE_RLINE=62 */ ;   // v:/cpu2908/fpga/machxo2/register.v(57[8] 59[4])
    defparam R_i0_i3.GSR = "DISABLED";
    FD1P3AX R_i0_i4 (.D(data_ibus[4]), .SP(\sig[34] ), .CK(clkE_c), .Q(subPort[4])) /* synthesis LSE_LINE_FILE_ID=4, LSE_LCOL=11, LSE_RCOL=97, LSE_LLINE=62, LSE_RLINE=62 */ ;   // v:/cpu2908/fpga/machxo2/register.v(57[8] 59[4])
    defparam R_i0_i4.GSR = "DISABLED";
    FD1P3AX R_i0_i5 (.D(data_ibus[5]), .SP(\sig[34] ), .CK(clkE_c), .Q(subPort[5])) /* synthesis LSE_LINE_FILE_ID=4, LSE_LCOL=11, LSE_RCOL=97, LSE_LLINE=62, LSE_RLINE=62 */ ;   // v:/cpu2908/fpga/machxo2/register.v(57[8] 59[4])
    defparam R_i0_i5.GSR = "DISABLED";
    FD1P3AX R_i0_i6 (.D(data_ibus[6]), .SP(\sig[34] ), .CK(clkE_c), .Q(subPort[6])) /* synthesis LSE_LINE_FILE_ID=4, LSE_LCOL=11, LSE_RCOL=97, LSE_LLINE=62, LSE_RLINE=62 */ ;   // v:/cpu2908/fpga/machxo2/register.v(57[8] 59[4])
    defparam R_i0_i6.GSR = "DISABLED";
    FD1P3AX R_i0_i7 (.D(data_ibus[7]), .SP(\sig[34] ), .CK(clkE_c), .Q(subPort[7])) /* synthesis LSE_LINE_FILE_ID=4, LSE_LCOL=11, LSE_RCOL=97, LSE_LLINE=62, LSE_RLINE=62 */ ;   // v:/cpu2908/fpga/machxo2/register.v(57[8] 59[4])
    defparam R_i0_i7.GSR = "DISABLED";
    
endmodule
//
// Verilog Description of module register1
//

module register1 (R, clkQ_c__inv, n5395) /* synthesis syn_module_defined=1 */ ;
    output R;
    input clkQ_c__inv;
    input n5395;
    
    wire clkQ_c__inv /* synthesis is_inv_clock=1, is_clock=1 */ ;   // v:/cpu2908/fpga/machxo2/top.v(14[14:18])
    
    FD1S3AX R_12 (.D(n5395), .CK(clkQ_c__inv), .Q(R)) /* synthesis LSE_LINE_FILE_ID=4, LSE_LCOL=11, LSE_RCOL=108, LSE_LLINE=79, LSE_RLINE=79 */ ;   // v:/cpu2908/fpga/machxo2/register.v(12[8] 14[4])
    defparam R_12.GSR = "DISABLED";
    
endmodule
//
// Verilog Description of module tristateBuff8_U16
//

module tristateBuff8_U16 (subPort, R, ExDataOut) /* synthesis syn_module_defined=1 */ ;
    input [7:0]subPort;
    input R;
    output [7:0]ExDataOut;
    
    
    LUT4 i295_2_lut (.A(subPort[7]), .B(R), .Z(ExDataOut[7])) /* synthesis lut_function=(A (B)) */ ;   // v:/cpu2908/fpga/machxo2/tristatebuff.v(17[8:9])
    defparam i295_2_lut.init = 16'h8888;
    LUT4 i294_2_lut (.A(subPort[6]), .B(R), .Z(ExDataOut[6])) /* synthesis lut_function=(A (B)) */ ;   // v:/cpu2908/fpga/machxo2/tristatebuff.v(17[8:9])
    defparam i294_2_lut.init = 16'h8888;
    LUT4 i293_2_lut (.A(subPort[5]), .B(R), .Z(ExDataOut[5])) /* synthesis lut_function=(A (B)) */ ;   // v:/cpu2908/fpga/machxo2/tristatebuff.v(17[8:9])
    defparam i293_2_lut.init = 16'h8888;
    LUT4 i292_2_lut (.A(subPort[4]), .B(R), .Z(ExDataOut[4])) /* synthesis lut_function=(A (B)) */ ;   // v:/cpu2908/fpga/machxo2/tristatebuff.v(17[8:9])
    defparam i292_2_lut.init = 16'h8888;
    LUT4 i291_2_lut (.A(subPort[3]), .B(R), .Z(ExDataOut[3])) /* synthesis lut_function=(A (B)) */ ;   // v:/cpu2908/fpga/machxo2/tristatebuff.v(17[8:9])
    defparam i291_2_lut.init = 16'h8888;
    LUT4 i290_2_lut (.A(subPort[2]), .B(R), .Z(ExDataOut[2])) /* synthesis lut_function=(A (B)) */ ;   // v:/cpu2908/fpga/machxo2/tristatebuff.v(17[8:9])
    defparam i290_2_lut.init = 16'h8888;
    LUT4 i289_2_lut (.A(subPort[1]), .B(R), .Z(ExDataOut[1])) /* synthesis lut_function=(A (B)) */ ;   // v:/cpu2908/fpga/machxo2/tristatebuff.v(17[8:9])
    defparam i289_2_lut.init = 16'h8888;
    LUT4 i285_2_lut (.A(subPort[0]), .B(R), .Z(ExDataOut[0])) /* synthesis lut_function=(A (B)) */ ;   // v:/cpu2908/fpga/machxo2/tristatebuff.v(17[8:9])
    defparam i285_2_lut.init = 16'h8888;
    
endmodule
//
// Verilog Description of module register16_U17
//

module register16_U17 (nTSC_c, nReset2, n865, R, nWRTxD, ocea_enable_1, 
            sramWE, subPort, n549, R_adj_120, nRDRxD, n553, n929, 
            nCS_c_0, clkE_c, \sig[35] , addr_ibus, n4907, n5386, 
            n561, n5398, n4869, n972, n4, n31, n589, n545, n557, 
            n541, n537, n534, n573, n569, n585, n581, n577, 
            n593, n565, nCS_c_1) /* synthesis syn_module_defined=1 */ ;
    input nTSC_c;
    input nReset2;
    input n865;
    input R;
    output nWRTxD;
    output ocea_enable_1;
    output sramWE;
    output [15:0]subPort;
    output n549;
    input R_adj_120;
    output nRDRxD;
    output n553;
    input n929;
    output nCS_c_0;
    input clkE_c;
    input \sig[35] ;
    input [15:0]addr_ibus;
    output n4907;
    output n5386;
    output n561;
    output n5398;
    input n4869;
    output n972;
    input n4;
    output n31;
    output n589;
    output n545;
    output n557;
    output n541;
    output n537;
    output n534;
    output n573;
    output n569;
    output n585;
    output n581;
    output n577;
    output n593;
    output n565;
    output nCS_c_1;
    
    wire nWRTxD /* synthesis is_clock=1, SET_AS_NETWORK=nWRTxD */ ;   // v:/cpu2908/fpga/machxo2/top.v(124[6:12])
    wire nRDRxD /* synthesis is_clock=1, SET_AS_NETWORK=nRDRxD */ ;   // v:/cpu2908/fpga/machxo2/top.v(123[6:12])
    wire clkE_c /* synthesis is_clock=1 */ ;   // v:/cpu2908/fpga/machxo2/top.v(15[14:18])
    
    wire n4871, n10;
    
    LUT4 i2710_2_lut_3_lut_4_lut (.A(nTSC_c), .B(nReset2), .C(n865), .D(R), 
         .Z(nWRTxD)) /* synthesis lut_function=(A (B (C+(D))+!B (C))+!A (C)) */ ;   // v:/cpu2908/fpga/machxo2/register.v(112[8:9])
    defparam i2710_2_lut_3_lut_4_lut.init = 16'hf8f0;
    LUT4 i4572_2_lut_2_lut_3_lut_4_lut (.A(nTSC_c), .B(nReset2), .C(ocea_enable_1), 
         .D(R), .Z(sramWE)) /* synthesis lut_function=(!(A (B ((D)+!C)+!B !(C))+!A !(C))) */ ;   // v:/cpu2908/fpga/machxo2/register.v(112[8:9])
    defparam i4572_2_lut_2_lut_3_lut_4_lut.init = 16'h70f0;
    LUT4 i306_2_lut_3_lut (.A(nTSC_c), .B(nReset2), .C(subPort[11]), .Z(n549)) /* synthesis lut_function=(A (B (C))) */ ;   // v:/cpu2908/fpga/machxo2/register.v(112[8:9])
    defparam i306_2_lut_3_lut.init = 16'h8080;
    LUT4 i2643_3_lut_4_lut (.A(nTSC_c), .B(nReset2), .C(n865), .D(R_adj_120), 
         .Z(nRDRxD)) /* synthesis lut_function=(A (B (C+(D))+!B (C))+!A (C)) */ ;   // v:/cpu2908/fpga/machxo2/register.v(112[8:9])
    defparam i2643_3_lut_4_lut.init = 16'hf8f0;
    LUT4 i305_2_lut_3_lut (.A(nTSC_c), .B(nReset2), .C(subPort[10]), .Z(n553)) /* synthesis lut_function=(A (B (C))) */ ;   // v:/cpu2908/fpga/machxo2/register.v(112[8:9])
    defparam i305_2_lut_3_lut.init = 16'h8080;
    LUT4 i4585_2_lut_2_lut_3_lut_3_lut_4_lut (.A(nTSC_c), .B(nReset2), .C(n929), 
         .D(ocea_enable_1), .Z(nCS_c_0)) /* synthesis lut_function=((((D)+!C)+!B)+!A) */ ;   // v:/cpu2908/fpga/machxo2/register.v(112[8:9])
    defparam i4585_2_lut_2_lut_3_lut_3_lut_4_lut.init = 16'hff7f;
    FD1P3AX R_i0_i0 (.D(addr_ibus[0]), .SP(\sig[35] ), .CK(clkE_c), .Q(subPort[0])) /* synthesis LSE_LINE_FILE_ID=4, LSE_LCOL=13, LSE_RCOL=97, LSE_LLINE=66, LSE_RLINE=66 */ ;   // v:/cpu2908/fpga/machxo2/register.v(108[8] 110[4])
    defparam R_i0_i0.GSR = "DISABLED";
    LUT4 i3_4_lut (.A(subPort[11]), .B(subPort[9]), .C(subPort[8]), .D(subPort[10]), 
         .Z(n4871)) /* synthesis lut_function=(A (B (C (D)))) */ ;   // v:/cpu2908/fpga/machxo2/register.v(112[8:9])
    defparam i3_4_lut.init = 16'h8000;
    FD1P3AX R_i0_i1 (.D(addr_ibus[1]), .SP(\sig[35] ), .CK(clkE_c), .Q(subPort[1])) /* synthesis LSE_LINE_FILE_ID=4, LSE_LCOL=13, LSE_RCOL=97, LSE_LLINE=66, LSE_RLINE=66 */ ;   // v:/cpu2908/fpga/machxo2/register.v(108[8] 110[4])
    defparam R_i0_i1.GSR = "DISABLED";
    LUT4 i1_3_lut_4_lut_4_lut_3_lut_4_lut (.A(nTSC_c), .B(nReset2), .C(n4871), 
         .D(n929), .Z(n4907)) /* synthesis lut_function=((((D)+!C)+!B)+!A) */ ;   // v:/cpu2908/fpga/machxo2/register.v(112[8:9])
    defparam i1_3_lut_4_lut_4_lut_3_lut_4_lut.init = 16'hff7f;
    FD1P3AX R_i0_i2 (.D(addr_ibus[2]), .SP(\sig[35] ), .CK(clkE_c), .Q(subPort[2])) /* synthesis LSE_LINE_FILE_ID=4, LSE_LCOL=13, LSE_RCOL=97, LSE_LLINE=66, LSE_RLINE=66 */ ;   // v:/cpu2908/fpga/machxo2/register.v(108[8] 110[4])
    defparam R_i0_i2.GSR = "DISABLED";
    FD1P3AX R_i0_i3 (.D(addr_ibus[3]), .SP(\sig[35] ), .CK(clkE_c), .Q(subPort[3])) /* synthesis LSE_LINE_FILE_ID=4, LSE_LCOL=13, LSE_RCOL=97, LSE_LLINE=66, LSE_RLINE=66 */ ;   // v:/cpu2908/fpga/machxo2/register.v(108[8] 110[4])
    defparam R_i0_i3.GSR = "DISABLED";
    FD1P3AX R_i0_i4 (.D(addr_ibus[4]), .SP(\sig[35] ), .CK(clkE_c), .Q(subPort[4])) /* synthesis LSE_LINE_FILE_ID=4, LSE_LCOL=13, LSE_RCOL=97, LSE_LLINE=66, LSE_RLINE=66 */ ;   // v:/cpu2908/fpga/machxo2/register.v(108[8] 110[4])
    defparam R_i0_i4.GSR = "DISABLED";
    FD1P3AX R_i0_i5 (.D(addr_ibus[5]), .SP(\sig[35] ), .CK(clkE_c), .Q(subPort[5])) /* synthesis LSE_LINE_FILE_ID=4, LSE_LCOL=13, LSE_RCOL=97, LSE_LLINE=66, LSE_RLINE=66 */ ;   // v:/cpu2908/fpga/machxo2/register.v(108[8] 110[4])
    defparam R_i0_i5.GSR = "DISABLED";
    FD1P3AX R_i0_i6 (.D(addr_ibus[6]), .SP(\sig[35] ), .CK(clkE_c), .Q(subPort[6])) /* synthesis LSE_LINE_FILE_ID=4, LSE_LCOL=13, LSE_RCOL=97, LSE_LLINE=66, LSE_RLINE=66 */ ;   // v:/cpu2908/fpga/machxo2/register.v(108[8] 110[4])
    defparam R_i0_i6.GSR = "DISABLED";
    FD1P3AX R_i0_i7 (.D(addr_ibus[7]), .SP(\sig[35] ), .CK(clkE_c), .Q(subPort[7])) /* synthesis LSE_LINE_FILE_ID=4, LSE_LCOL=13, LSE_RCOL=97, LSE_LLINE=66, LSE_RLINE=66 */ ;   // v:/cpu2908/fpga/machxo2/register.v(108[8] 110[4])
    defparam R_i0_i7.GSR = "DISABLED";
    FD1P3AX R_i0_i8 (.D(addr_ibus[8]), .SP(\sig[35] ), .CK(clkE_c), .Q(subPort[8])) /* synthesis LSE_LINE_FILE_ID=4, LSE_LCOL=13, LSE_RCOL=97, LSE_LLINE=66, LSE_RLINE=66 */ ;   // v:/cpu2908/fpga/machxo2/register.v(108[8] 110[4])
    defparam R_i0_i8.GSR = "DISABLED";
    FD1P3AX R_i0_i9 (.D(addr_ibus[9]), .SP(\sig[35] ), .CK(clkE_c), .Q(subPort[9])) /* synthesis LSE_LINE_FILE_ID=4, LSE_LCOL=13, LSE_RCOL=97, LSE_LLINE=66, LSE_RLINE=66 */ ;   // v:/cpu2908/fpga/machxo2/register.v(108[8] 110[4])
    defparam R_i0_i9.GSR = "DISABLED";
    FD1P3AX R_i0_i10 (.D(addr_ibus[10]), .SP(\sig[35] ), .CK(clkE_c), 
            .Q(subPort[10])) /* synthesis LSE_LINE_FILE_ID=4, LSE_LCOL=13, LSE_RCOL=97, LSE_LLINE=66, LSE_RLINE=66 */ ;   // v:/cpu2908/fpga/machxo2/register.v(108[8] 110[4])
    defparam R_i0_i10.GSR = "DISABLED";
    FD1P3AX R_i0_i11 (.D(addr_ibus[11]), .SP(\sig[35] ), .CK(clkE_c), 
            .Q(subPort[11])) /* synthesis LSE_LINE_FILE_ID=4, LSE_LCOL=13, LSE_RCOL=97, LSE_LLINE=66, LSE_RLINE=66 */ ;   // v:/cpu2908/fpga/machxo2/register.v(108[8] 110[4])
    defparam R_i0_i11.GSR = "DISABLED";
    FD1P3AX R_i0_i12 (.D(addr_ibus[12]), .SP(\sig[35] ), .CK(clkE_c), 
            .Q(subPort[12])) /* synthesis LSE_LINE_FILE_ID=4, LSE_LCOL=13, LSE_RCOL=97, LSE_LLINE=66, LSE_RLINE=66 */ ;   // v:/cpu2908/fpga/machxo2/register.v(108[8] 110[4])
    defparam R_i0_i12.GSR = "DISABLED";
    FD1P3AX R_i0_i13 (.D(addr_ibus[13]), .SP(\sig[35] ), .CK(clkE_c), 
            .Q(subPort[13])) /* synthesis LSE_LINE_FILE_ID=4, LSE_LCOL=13, LSE_RCOL=97, LSE_LLINE=66, LSE_RLINE=66 */ ;   // v:/cpu2908/fpga/machxo2/register.v(108[8] 110[4])
    defparam R_i0_i13.GSR = "DISABLED";
    FD1P3AX R_i0_i14 (.D(addr_ibus[14]), .SP(\sig[35] ), .CK(clkE_c), 
            .Q(subPort[14])) /* synthesis LSE_LINE_FILE_ID=4, LSE_LCOL=13, LSE_RCOL=97, LSE_LLINE=66, LSE_RLINE=66 */ ;   // v:/cpu2908/fpga/machxo2/register.v(108[8] 110[4])
    defparam R_i0_i14.GSR = "DISABLED";
    FD1P3AX R_i0_i15 (.D(addr_ibus[15]), .SP(\sig[35] ), .CK(clkE_c), 
            .Q(subPort[15])) /* synthesis LSE_LINE_FILE_ID=4, LSE_LCOL=13, LSE_RCOL=97, LSE_LLINE=66, LSE_RLINE=66 */ ;   // v:/cpu2908/fpga/machxo2/register.v(108[8] 110[4])
    defparam R_i0_i15.GSR = "DISABLED";
    LUT4 i4_4_lut (.A(subPort[12]), .B(subPort[14]), .C(subPort[15]), 
         .D(subPort[7]), .Z(n10)) /* synthesis lut_function=(A (B (C (D)))) */ ;   // v:/cpu2908/fpga/machxo2/register.v(112[8:9])
    defparam i4_4_lut.init = 16'h8000;
    LUT4 i288_2_lut_rep_98_3_lut (.A(nTSC_c), .B(nReset2), .C(R), .Z(n5386)) /* synthesis lut_function=(A (B (C))) */ ;   // v:/cpu2908/fpga/machxo2/register.v(112[8:9])
    defparam i288_2_lut_rep_98_3_lut.init = 16'h8080;
    LUT4 i303_2_lut_3_lut (.A(nTSC_c), .B(nReset2), .C(subPort[8]), .Z(n561)) /* synthesis lut_function=(A (B (C))) */ ;   // v:/cpu2908/fpga/machxo2/register.v(112[8:9])
    defparam i303_2_lut_3_lut.init = 16'h8080;
    LUT4 i4612_2_lut_rep_110 (.A(nTSC_c), .B(nReset2), .Z(n5398)) /* synthesis lut_function=(!(A (B))) */ ;   // v:/cpu2908/fpga/machxo2/register.v(112[8:9])
    defparam i4612_2_lut_rep_110.init = 16'h7777;
    LUT4 i1_2_lut_2_lut_3_lut (.A(nTSC_c), .B(nReset2), .C(n4869), .Z(n972)) /* synthesis lut_function=(A (B (C))) */ ;   // v:/cpu2908/fpga/machxo2/register.v(112[8:9])
    defparam i1_2_lut_2_lut_3_lut.init = 16'h8080;
    LUT4 i1_4_lut_4_lut (.A(n5398), .B(n4), .C(n4869), .D(n4907), .Z(n31)) /* synthesis lut_function=(A (D)+!A (B+(C+(D)))) */ ;   // v:/cpu2908/fpga/machxo2/register.v(112[8:9])
    defparam i1_4_lut_4_lut.init = 16'hff54;
    LUT4 i296_2_lut_3_lut (.A(nTSC_c), .B(nReset2), .C(subPort[1]), .Z(n589)) /* synthesis lut_function=(A (B (C))) */ ;   // v:/cpu2908/fpga/machxo2/register.v(112[8:9])
    defparam i296_2_lut_3_lut.init = 16'h8080;
    LUT4 i307_2_lut_3_lut (.A(nTSC_c), .B(nReset2), .C(subPort[12]), .Z(n545)) /* synthesis lut_function=(A (B (C))) */ ;   // v:/cpu2908/fpga/machxo2/register.v(112[8:9])
    defparam i307_2_lut_3_lut.init = 16'h8080;
    LUT4 i304_2_lut_3_lut (.A(nTSC_c), .B(nReset2), .C(subPort[9]), .Z(n557)) /* synthesis lut_function=(A (B (C))) */ ;   // v:/cpu2908/fpga/machxo2/register.v(112[8:9])
    defparam i304_2_lut_3_lut.init = 16'h8080;
    LUT4 i308_2_lut_3_lut (.A(nTSC_c), .B(nReset2), .C(subPort[13]), .Z(n541)) /* synthesis lut_function=(A (B (C))) */ ;   // v:/cpu2908/fpga/machxo2/register.v(112[8:9])
    defparam i308_2_lut_3_lut.init = 16'h8080;
    LUT4 i309_2_lut_3_lut (.A(nTSC_c), .B(nReset2), .C(subPort[14]), .Z(n537)) /* synthesis lut_function=(A (B (C))) */ ;   // v:/cpu2908/fpga/machxo2/register.v(112[8:9])
    defparam i309_2_lut_3_lut.init = 16'h8080;
    LUT4 i310_2_lut_3_lut (.A(nTSC_c), .B(nReset2), .C(subPort[15]), .Z(n534)) /* synthesis lut_function=(A (B (C))) */ ;   // v:/cpu2908/fpga/machxo2/register.v(112[8:9])
    defparam i310_2_lut_3_lut.init = 16'h8080;
    LUT4 i300_2_lut_3_lut (.A(nTSC_c), .B(nReset2), .C(subPort[5]), .Z(n573)) /* synthesis lut_function=(A (B (C))) */ ;   // v:/cpu2908/fpga/machxo2/register.v(112[8:9])
    defparam i300_2_lut_3_lut.init = 16'h8080;
    LUT4 i301_2_lut_3_lut (.A(nTSC_c), .B(nReset2), .C(subPort[6]), .Z(n569)) /* synthesis lut_function=(A (B (C))) */ ;   // v:/cpu2908/fpga/machxo2/register.v(112[8:9])
    defparam i301_2_lut_3_lut.init = 16'h8080;
    LUT4 i297_2_lut_3_lut (.A(nTSC_c), .B(nReset2), .C(subPort[2]), .Z(n585)) /* synthesis lut_function=(A (B (C))) */ ;   // v:/cpu2908/fpga/machxo2/register.v(112[8:9])
    defparam i297_2_lut_3_lut.init = 16'h8080;
    LUT4 i298_2_lut_3_lut (.A(nTSC_c), .B(nReset2), .C(subPort[3]), .Z(n581)) /* synthesis lut_function=(A (B (C))) */ ;   // v:/cpu2908/fpga/machxo2/register.v(112[8:9])
    defparam i298_2_lut_3_lut.init = 16'h8080;
    LUT4 i299_2_lut_3_lut (.A(nTSC_c), .B(nReset2), .C(subPort[4]), .Z(n577)) /* synthesis lut_function=(A (B (C))) */ ;   // v:/cpu2908/fpga/machxo2/register.v(112[8:9])
    defparam i299_2_lut_3_lut.init = 16'h8080;
    LUT4 i286_2_lut_3_lut (.A(nTSC_c), .B(nReset2), .C(subPort[0]), .Z(n593)) /* synthesis lut_function=(A (B (C))) */ ;   // v:/cpu2908/fpga/machxo2/register.v(112[8:9])
    defparam i286_2_lut_3_lut.init = 16'h8080;
    LUT4 i302_2_lut_3_lut (.A(nTSC_c), .B(nReset2), .C(subPort[7]), .Z(n565)) /* synthesis lut_function=(A (B (C))) */ ;   // v:/cpu2908/fpga/machxo2/register.v(112[8:9])
    defparam i302_2_lut_3_lut.init = 16'h8080;
    LUT4 i1_4_lut_rep_97 (.A(subPort[13]), .B(n5398), .C(n10), .D(n4871), 
         .Z(ocea_enable_1)) /* synthesis lut_function=(!((B+!(C (D)))+!A)) */ ;   // v:/cpu2908/fpga/machxo2/register.v(112[8:9])
    defparam i1_4_lut_rep_97.init = 16'h2000;
    LUT4 i2720_1_lut_4_lut (.A(subPort[13]), .B(n5398), .C(n10), .D(n4871), 
         .Z(nCS_c_1)) /* synthesis lut_function=((B+!(C (D)))+!A) */ ;   // v:/cpu2908/fpga/machxo2/register.v(112[8:9])
    defparam i2720_1_lut_4_lut.init = 16'hdfff;
    
endmodule
//
// Verilog Description of module sequencer
//

module sequencer (ExDataIn, \sig[45] , IRQH_c, S_c_1, S_c_0, clkE_c, 
            nIRQ_c, VCC_net, clkE_N_18, clkQ_c, \sig[44] , \sig[47] , 
            \sig[46] , clkQ_c__inv, nReset2, nReset1, \sig[43] , \sig[35] , 
            \sig[34] , \sig[33] , \sig[32] , \sig[94] , \sig[93] , 
            \sig[91] , \sig[90] , \sig[89] , \sig[88] , \sig[87] , 
            \sig[86] , \sig[85] , \sig[84] , \sig[83] , \sig[82] , 
            \sig[81] , \sig[80] , \sig[79] , \data_ibus[1] , n7, \sig[78] , 
            \sig[77] , \sig[76] , \sig[75] , \sig[74] , \sig[73] , 
            \sig[72] , \subPort[4] , \outreg[1] , \InternalDataBus[4] , 
            \addrLo[4] , \addrHi[4] , n68, \subPort[4]_adj_109 , \subPort[4]_adj_110 , 
            \outreg[2] , n5388, \subPort[2] , n1, \subPort[1] , n1_adj_111, 
            \subPort[7] , n1_adj_112, \subPort[0] , n1_adj_113, \subPort[6] , 
            n1_adj_114, n5389, \data_ibus[4] , \subPort[4]_adj_115 , 
            \addrLo[3] , n5, clkQ_c_derived_27_enable_9, clkQ_c_derived_27_enable_5, 
            \subPort[5] , \data_ibus[6] , n7_adj_116, \data_ibus[7] , 
            n7_adj_117, \data_ibus[2] , n7_adj_118, \data_ibus[0] , 
            n7_adj_119, \data_es_bus[6] , \data_es_bus[7] , \data_es_bus[3] , 
            \data_es_bus[2] , \data_es_bus[1] , \data_es_bus[0] , GND_net) /* synthesis syn_module_defined=1 */ ;
    input [7:0]ExDataIn;
    input \sig[45] ;
    output IRQH_c;
    output S_c_1;
    output S_c_0;
    input clkE_c;
    input nIRQ_c;
    input VCC_net;
    input clkE_N_18;
    input clkQ_c;
    input \sig[44] ;
    input \sig[47] ;
    input \sig[46] ;
    input clkQ_c__inv;
    input nReset2;
    input nReset1;
    input \sig[43] ;
    output \sig[35] ;
    output \sig[34] ;
    output \sig[33] ;
    output \sig[32] ;
    output \sig[94] ;
    output \sig[93] ;
    output \sig[91] ;
    output \sig[90] ;
    output \sig[89] ;
    output \sig[88] ;
    output \sig[87] ;
    output \sig[86] ;
    output \sig[85] ;
    output \sig[84] ;
    output \sig[83] ;
    output \sig[82] ;
    output \sig[81] ;
    output \sig[80] ;
    output \sig[79] ;
    input \data_ibus[1] ;
    output n7;
    output \sig[78] ;
    output \sig[77] ;
    output \sig[76] ;
    output \sig[75] ;
    output \sig[74] ;
    output \sig[73] ;
    output \sig[72] ;
    input \subPort[4] ;
    output \outreg[1] ;
    output \InternalDataBus[4] ;
    input \addrLo[4] ;
    input \addrHi[4] ;
    output n68;
    input \subPort[4]_adj_109 ;
    input \subPort[4]_adj_110 ;
    output \outreg[2] ;
    output n5388;
    input \subPort[2] ;
    output n1;
    input \subPort[1] ;
    output n1_adj_111;
    input \subPort[7] ;
    output n1_adj_112;
    input \subPort[0] ;
    output n1_adj_113;
    input \subPort[6] ;
    output n1_adj_114;
    output n5389;
    input \data_ibus[4] ;
    input \subPort[4]_adj_115 ;
    input \addrLo[3] ;
    output n5;
    output clkQ_c_derived_27_enable_9;
    output clkQ_c_derived_27_enable_5;
    input \subPort[5] ;
    input \data_ibus[6] ;
    output n7_adj_116;
    input \data_ibus[7] ;
    output n7_adj_117;
    input \data_ibus[2] ;
    output n7_adj_118;
    input \data_ibus[0] ;
    output n7_adj_119;
    output \data_es_bus[6] ;
    output \data_es_bus[7] ;
    output \data_es_bus[3] ;
    output \data_es_bus[2] ;
    output \data_es_bus[1] ;
    output \data_es_bus[0] ;
    input GND_net;
    
    wire clkE_c /* synthesis is_clock=1 */ ;   // v:/cpu2908/fpga/machxo2/top.v(15[14:18])
    wire clkE_N_18 /* synthesis is_inv_clock=1 */ ;   // v:/cpu2908/fpga/machxo2/top.v(14[14:18])
    wire clkQ_c /* synthesis is_clock=1 */ ;   // v:/cpu2908/fpga/machxo2/top.v(14[14:18])
    wire clkQ_c__inv /* synthesis is_inv_clock=1, is_clock=1 */ ;   // v:/cpu2908/fpga/machxo2/top.v(14[14:18])
    
    sequencer_s Sequencer_s (.ExDataIn({ExDataIn}), .\sig[45] (\sig[45] ), 
            .IRQH_c(IRQH_c), .S_c_1(S_c_1), .S_c_0(S_c_0), .clkE_c(clkE_c), 
            .nIRQ_c(nIRQ_c), .VCC_net(VCC_net), .clkE_N_18(clkE_N_18), 
            .clkQ_c(clkQ_c), .\sig[44] (\sig[44] ), .\sig[47] (\sig[47] ), 
            .\sig[46] (\sig[46] ), .clkQ_c__inv(clkQ_c__inv), .nReset2(nReset2), 
            .nReset1(nReset1), .\sig[43] (\sig[43] ), .\sig[35] (\sig[35] ), 
            .\sig[34] (\sig[34] ), .\sig[33] (\sig[33] ), .\sig[32] (\sig[32] ), 
            .\sig[94] (\sig[94] ), .\sig[93] (\sig[93] ), .\sig[91] (\sig[91] ), 
            .\sig[90] (\sig[90] ), .\sig[89] (\sig[89] ), .\sig[88] (\sig[88] ), 
            .\sig[87] (\sig[87] ), .\sig[86] (\sig[86] ), .\sig[85] (\sig[85] ), 
            .\sig[84] (\sig[84] ), .\sig[83] (\sig[83] ), .\sig[82] (\sig[82] ), 
            .\sig[81] (\sig[81] ), .\sig[80] (\sig[80] ), .\sig[79] (\sig[79] ), 
            .\data_ibus[1] (\data_ibus[1] ), .n7(n7), .\sig[78] (\sig[78] ), 
            .\sig[77] (\sig[77] ), .\sig[76] (\sig[76] ), .\sig[75] (\sig[75] ), 
            .\sig[74] (\sig[74] ), .\sig[73] (\sig[73] ), .\sig[72] (\sig[72] ), 
            .\subPort[4] (\subPort[4] ), .\outreg[1] (\outreg[1] ), .\InternalDataBus[4] (\InternalDataBus[4] ), 
            .\addrLo[4] (\addrLo[4] ), .\addrHi[4] (\addrHi[4] ), .n68(n68), 
            .\subPort[4]_adj_98 (\subPort[4]_adj_109 ), .\subPort[4]_adj_99 (\subPort[4]_adj_110 ), 
            .\outreg[2] (\outreg[2] ), .n5388(n5388), .\subPort[2] (\subPort[2] ), 
            .n1(n1), .\subPort[1] (\subPort[1] ), .n1_adj_100(n1_adj_111), 
            .\subPort[7] (\subPort[7] ), .n1_adj_101(n1_adj_112), .\subPort[0] (\subPort[0] ), 
            .n1_adj_102(n1_adj_113), .\subPort[6] (\subPort[6] ), .n1_adj_103(n1_adj_114), 
            .n5389(n5389), .\data_ibus[4] (\data_ibus[4] ), .\subPort[4]_adj_104 (\subPort[4]_adj_115 ), 
            .\addrLo[3] (\addrLo[3] ), .n5(n5), .clkQ_c_derived_27_enable_9(clkQ_c_derived_27_enable_9), 
            .clkQ_c_derived_27_enable_5(clkQ_c_derived_27_enable_5), .\subPort[5] (\subPort[5] ), 
            .\data_ibus[6] (\data_ibus[6] ), .n7_adj_105(n7_adj_116), .\data_ibus[7] (\data_ibus[7] ), 
            .n7_adj_106(n7_adj_117), .\data_ibus[2] (\data_ibus[2] ), .n7_adj_107(n7_adj_118), 
            .\data_ibus[0] (\data_ibus[0] ), .n7_adj_108(n7_adj_119), .\data_es_bus[6] (\data_es_bus[6] ), 
            .\data_es_bus[7] (\data_es_bus[7] ), .\data_es_bus[3] (\data_es_bus[3] ), 
            .\data_es_bus[2] (\data_es_bus[2] ), .\data_es_bus[1] (\data_es_bus[1] ), 
            .\data_es_bus[0] (\data_es_bus[0] ), .GND_net(GND_net)) /* synthesis syn_module_defined=1 */ ;   // v:/cpu2908/fpga/machxo2/sequencer.v(85[13] 124[11])
    
endmodule
//
// Verilog Description of module sequencer_s
//

module sequencer_s (ExDataIn, \sig[45] , IRQH_c, S_c_1, S_c_0, clkE_c, 
            nIRQ_c, VCC_net, clkE_N_18, clkQ_c, \sig[44] , \sig[47] , 
            \sig[46] , clkQ_c__inv, nReset2, nReset1, \sig[43] , \sig[35] , 
            \sig[34] , \sig[33] , \sig[32] , \sig[94] , \sig[93] , 
            \sig[91] , \sig[90] , \sig[89] , \sig[88] , \sig[87] , 
            \sig[86] , \sig[85] , \sig[84] , \sig[83] , \sig[82] , 
            \sig[81] , \sig[80] , \sig[79] , \data_ibus[1] , n7, \sig[78] , 
            \sig[77] , \sig[76] , \sig[75] , \sig[74] , \sig[73] , 
            \sig[72] , \subPort[4] , \outreg[1] , \InternalDataBus[4] , 
            \addrLo[4] , \addrHi[4] , n68, \subPort[4]_adj_98 , \subPort[4]_adj_99 , 
            \outreg[2] , n5388, \subPort[2] , n1, \subPort[1] , n1_adj_100, 
            \subPort[7] , n1_adj_101, \subPort[0] , n1_adj_102, \subPort[6] , 
            n1_adj_103, n5389, \data_ibus[4] , \subPort[4]_adj_104 , 
            \addrLo[3] , n5, clkQ_c_derived_27_enable_9, clkQ_c_derived_27_enable_5, 
            \subPort[5] , \data_ibus[6] , n7_adj_105, \data_ibus[7] , 
            n7_adj_106, \data_ibus[2] , n7_adj_107, \data_ibus[0] , 
            n7_adj_108, \data_es_bus[6] , \data_es_bus[7] , \data_es_bus[3] , 
            \data_es_bus[2] , \data_es_bus[1] , \data_es_bus[0] , GND_net) /* synthesis syn_module_defined=1 */ ;
    input [7:0]ExDataIn;
    input \sig[45] ;
    output IRQH_c;
    output S_c_1;
    output S_c_0;
    input clkE_c;
    input nIRQ_c;
    input VCC_net;
    input clkE_N_18;
    input clkQ_c;
    input \sig[44] ;
    input \sig[47] ;
    input \sig[46] ;
    input clkQ_c__inv;
    input nReset2;
    input nReset1;
    input \sig[43] ;
    output \sig[35] ;
    output \sig[34] ;
    output \sig[33] ;
    output \sig[32] ;
    output \sig[94] ;
    output \sig[93] ;
    output \sig[91] ;
    output \sig[90] ;
    output \sig[89] ;
    output \sig[88] ;
    output \sig[87] ;
    output \sig[86] ;
    output \sig[85] ;
    output \sig[84] ;
    output \sig[83] ;
    output \sig[82] ;
    output \sig[81] ;
    output \sig[80] ;
    output \sig[79] ;
    input \data_ibus[1] ;
    output n7;
    output \sig[78] ;
    output \sig[77] ;
    output \sig[76] ;
    output \sig[75] ;
    output \sig[74] ;
    output \sig[73] ;
    output \sig[72] ;
    input \subPort[4] ;
    output \outreg[1] ;
    output \InternalDataBus[4] ;
    input \addrLo[4] ;
    input \addrHi[4] ;
    output n68;
    input \subPort[4]_adj_98 ;
    input \subPort[4]_adj_99 ;
    output \outreg[2] ;
    output n5388;
    input \subPort[2] ;
    output n1;
    input \subPort[1] ;
    output n1_adj_100;
    input \subPort[7] ;
    output n1_adj_101;
    input \subPort[0] ;
    output n1_adj_102;
    input \subPort[6] ;
    output n1_adj_103;
    output n5389;
    input \data_ibus[4] ;
    input \subPort[4]_adj_104 ;
    input \addrLo[3] ;
    output n5;
    output clkQ_c_derived_27_enable_9;
    output clkQ_c_derived_27_enable_5;
    input \subPort[5] ;
    input \data_ibus[6] ;
    output n7_adj_105;
    input \data_ibus[7] ;
    output n7_adj_106;
    input \data_ibus[2] ;
    output n7_adj_107;
    input \data_ibus[0] ;
    output n7_adj_108;
    output \data_es_bus[6] ;
    output \data_es_bus[7] ;
    output \data_es_bus[3] ;
    output \data_es_bus[2] ;
    output \data_es_bus[1] ;
    output \data_es_bus[0] ;
    input GND_net;
    
    wire clkE_c /* synthesis is_clock=1 */ ;   // v:/cpu2908/fpga/machxo2/top.v(15[14:18])
    wire clkE_N_18 /* synthesis is_inv_clock=1 */ ;   // v:/cpu2908/fpga/machxo2/top.v(14[14:18])
    wire N_14 /* synthesis is_clock=1 */ ;   // v:/cpu2908/fpga/machxo2/impl1/sequencer_s.v(66[6:10])
    wire clkQ_c /* synthesis is_clock=1 */ ;   // v:/cpu2908/fpga/machxo2/top.v(14[14:18])
    wire [127:0]sig /* synthesis is_inv_clock=1 */ ;   // v:/cpu2908/fpga/machxo2/core.v(20[21:24])
    wire clkQ_c__inv /* synthesis is_inv_clock=1, is_clock=1 */ ;   // v:/cpu2908/fpga/machxo2/top.v(14[14:18])
    wire N_28 /* synthesis is_clock=1 */ ;   // v:/cpu2908/fpga/machxo2/impl1/sequencer_s.v(78[6:10])
    
    wire N_46, N_29, N_30, JG, N_38, N_47, JL, N_40, N_35, 
        N_36, N_42, N_43, N_8, N_44, N_45, N_2, N_11, N_37, 
        N_9, N_12, N_13, N_22, N_16;
    wire [31:0]UM;   // v:/cpu2908/fpga/machxo2/sequencer.v(21[20:22])
    wire [31:0]XD;   // v:/cpu2908/fpga/machxo2/impl1/sequencer_s.v(31[15:17])
    
    wire N_10, N_21, N_4, n4975, n4976;
    wire [7:0]subPort;   // v:/cpu2908/fpga/machxo2/register.v(49[19:26])
    wire [7:0]DataInSel1;   // v:/cpu2908/fpga/machxo2/impl1/sequencer_s.v(36[14:24])
    wire [7:0]uromIDX_A;   // v:/cpu2908/fpga/machxo2/impl1/sequencer_s.v(33[14:23])
    wire [7:0]data_es_bus;   // v:/cpu2908/fpga/machxo2/core.v(51[12:23])
    wire [0:9]CT;   // v:/cpu2908/fpga/machxo2/impl1/sequencer_s.v(7[14:16])
    wire [0:9]idx;   // v:/cpu2908/fpga/machxo2/impl1/sequencer_s.v(14[14:17])
    wire [0:7]uromIDX;   // v:/cpu2908/fpga/machxo2/impl1/sequencer_s.v(30[14:21])
    
    AND3 I114 (.A(N_29), .B(N_30), .C(ExDataIn[3]), .Z(N_46)) /* synthesis syn_instantiated=1, LSE_LINE_FILE_ID=5, LSE_LCOL=13, LSE_RCOL=11, LSE_LLINE=85, LSE_RLINE=124 */ ;   // v:/cpu2908/fpga/machxo2/sequencer.v(85[13] 124[11])
    AND3 I23 (.A(JG), .B(N_46), .C(ExDataIn[0]), .Z(N_38)) /* synthesis syn_instantiated=1, LSE_LINE_FILE_ID=5, LSE_LCOL=13, LSE_RCOL=11, LSE_LLINE=85, LSE_RLINE=124 */ ;   // v:/cpu2908/fpga/machxo2/sequencer.v(85[13] 124[11])
    AND3 I24 (.A(JL), .B(N_46), .C(N_47), .Z(N_40)) /* synthesis syn_instantiated=1, LSE_LINE_FILE_ID=5, LSE_LCOL=13, LSE_RCOL=11, LSE_LLINE=85, LSE_RLINE=124 */ ;   // v:/cpu2908/fpga/machxo2/sequencer.v(85[13] 124[11])
    XOR2 I115 (.A(ExDataIn[0]), .B(N_35), .Z(N_36)) /* synthesis syn_instantiated=1, LSE_LINE_FILE_ID=5, LSE_LCOL=13, LSE_RCOL=11, LSE_LLINE=85, LSE_RLINE=124 */ ;   // v:/cpu2908/fpga/machxo2/impl1/sequencer_s.v(86[6:48])
    AND4 I116 (.A(N_42), .B(ExDataIn[5]), .C(ExDataIn[6]), .D(ExDataIn[7]), 
         .Z(N_43)) /* synthesis syn_instantiated=1, LSE_LINE_FILE_ID=5, LSE_LCOL=13, LSE_RCOL=11, LSE_LLINE=85, LSE_RLINE=124 */ ;   // v:/cpu2908/fpga/machxo2/sequencer.v(85[13] 124[11])
    AND4 I10 (.A(IRQH_c), .B(\sig[45] ), .C(S_c_0), .D(S_c_1), .Z(N_8)) /* synthesis syn_instantiated=1, LSE_LINE_FILE_ID=5, LSE_LCOL=13, LSE_RCOL=11, LSE_LLINE=85, LSE_RLINE=124 */ ;   // v:/cpu2908/fpga/machxo2/sequencer.v(85[13] 124[11])
    OR2 I22 (.A(N_46), .B(N_44), .Z(N_45)) /* synthesis syn_instantiated=1, LSE_LINE_FILE_ID=5, LSE_LCOL=13, LSE_RCOL=11, LSE_LLINE=85, LSE_RLINE=124 */ ;   // v:/cpu2908/fpga/machxo2/impl1/sequencer_s.v(120[5:41])
    INV I34 (.A(ExDataIn[0]), .Z(N_47)) /* synthesis LSE_LINE_FILE_ID=5, LSE_LCOL=13, LSE_RCOL=11, LSE_LLINE=85, LSE_RLINE=124 */ ;   // v:/cpu2908/fpga/machxo2/sequencer.v(85[13] 124[11])
    FD1P3DX IRQCtrl (.D(nIRQ_c), .SP(VCC_net), .CK(clkE_c), .CD(N_2), 
            .Q(IRQH_c)) /* synthesis syn_instantiated=1, LSE_LINE_FILE_ID=5, LSE_LCOL=13, LSE_RCOL=11, LSE_LLINE=85, LSE_RLINE=124 */ ;   // v:/cpu2908/fpga/machxo2/impl1/sequencer_s.v(152[9:67])
    defparam IRQCtrl.GSR = "DISABLED";
    FD1P3DX I46 (.D(sig[6]), .SP(VCC_net), .CK(clkE_N_18), .CD(N_11), 
            .Q(N_14)) /* synthesis syn_instantiated=1, LSE_LINE_FILE_ID=5, LSE_LCOL=13, LSE_RCOL=11, LSE_LLINE=85, LSE_RLINE=124 */ ;   // v:/cpu2908/fpga/machxo2/impl1/sequencer_s.v(153[9:68])
    defparam I46.GSR = "DISABLED";
    FD1P3AY I109 (.D(sig[6]), .SP(VCC_net), .CK(clkQ_c), .Q(sig[1])) /* synthesis syn_instantiated=1, LSE_LINE_FILE_ID=5, LSE_LCOL=13, LSE_RCOL=11, LSE_LLINE=85, LSE_RLINE=124 */ ;   // v:/cpu2908/fpga/machxo2/impl1/sequencer_s.v(94[9:72])
    defparam I109.GSR = "ENABLED";
    XOR2 I27 (.A(\sig[44] ), .B(\sig[47] ), .Z(JL)) /* synthesis syn_instantiated=1, LSE_LINE_FILE_ID=5, LSE_LCOL=13, LSE_RCOL=11, LSE_LLINE=85, LSE_RLINE=124 */ ;   // v:/cpu2908/fpga/machxo2/impl1/sequencer_s.v(87[6:50])
    OR3 I21 (.A(N_40), .B(N_38), .C(N_37), .Z(sig[41])) /* synthesis syn_instantiated=1, LSE_LINE_FILE_ID=5, LSE_LCOL=13, LSE_RCOL=11, LSE_LLINE=85, LSE_RLINE=124 */ ;   // v:/cpu2908/fpga/machxo2/sequencer.v(85[13] 124[11])
    NR2 I29 (.A(JL), .B(\sig[46] ), .Z(JG)) /* synthesis syn_instantiated=1, LSE_LINE_FILE_ID=5, LSE_LCOL=13, LSE_RCOL=11, LSE_LLINE=85, LSE_RLINE=124 */ ;   // v:/cpu2908/fpga/machxo2/sequencer.v(85[13] 124[11])
    FD1P3AX Bit1 (.D(N_9), .SP(VCC_net), .CK(sig[0]), .Q(S_c_1)) /* synthesis syn_instantiated=1, LSE_LINE_FILE_ID=5, LSE_LCOL=13, LSE_RCOL=11, LSE_LLINE=85, LSE_RLINE=124 */ ;   // v:/cpu2908/fpga/machxo2/impl1/sequencer_s.v(151[9:70])
    defparam Bit1.GSR = "ENABLED";
    OR2 I110 (.A(N_13), .B(N_12), .Z(N_22)) /* synthesis syn_instantiated=1, LSE_LINE_FILE_ID=5, LSE_LCOL=13, LSE_RCOL=11, LSE_LLINE=85, LSE_RLINE=124 */ ;   // v:/cpu2908/fpga/machxo2/impl1/sequencer_s.v(121[5:42])
    OR2 I48 (.A(clkE_c), .B(N_16), .Z(sig[4])) /* synthesis syn_instantiated=1, LSE_LINE_FILE_ID=5, LSE_LCOL=13, LSE_RCOL=11, LSE_LLINE=85, LSE_RLINE=124 */ ;   // v:/cpu2908/fpga/machxo2/impl1/sequencer_s.v(122[5:42])
    OR2 I100 (.A(UM[8]), .B(UM[14]), .Z(XD[17])) /* synthesis syn_instantiated=1, LSE_LINE_FILE_ID=5, LSE_LCOL=13, LSE_RCOL=11, LSE_LLINE=85, LSE_RLINE=124 */ ;   // v:/cpu2908/fpga/machxo2/impl1/sequencer_s.v(123[5:46])
    OR2 I8 (.A(N_10), .B(N_8), .Z(N_9)) /* synthesis syn_instantiated=1, LSE_LINE_FILE_ID=5, LSE_LCOL=13, LSE_RCOL=11, LSE_LLINE=85, LSE_RLINE=124 */ ;   // v:/cpu2908/fpga/machxo2/impl1/sequencer_s.v(124[5:38])
    AND2 I117 (.A(N_45), .B(N_43), .Z(sig[42])) /* synthesis syn_instantiated=1, LSE_LINE_FILE_ID=5, LSE_LCOL=13, LSE_RCOL=11, LSE_LLINE=85, LSE_RLINE=124 */ ;   // v:/cpu2908/fpga/machxo2/impl1/sequencer_s.v(125[6:46])
    AND2 I25 (.A(N_44), .B(N_36), .Z(N_37)) /* synthesis syn_instantiated=1, LSE_LINE_FILE_ID=5, LSE_LCOL=13, LSE_RCOL=11, LSE_LLINE=85, LSE_RLINE=124 */ ;   // v:/cpu2908/fpga/machxo2/impl1/sequencer_s.v(126[6:42])
    AND2 I112 (.A(clkQ_c__inv), .B(nReset2), .Z(N_28)) /* synthesis syn_instantiated=1, LSE_LINE_FILE_ID=5, LSE_LCOL=13, LSE_RCOL=11, LSE_LLINE=85, LSE_RLINE=124 */ ;   // v:/cpu2908/fpga/machxo2/impl1/sequencer_s.v(127[6:44])
    AND2 I49 (.A(nReset1), .B(clkQ_c__inv), .Z(N_16)) /* synthesis syn_instantiated=1, LSE_LINE_FILE_ID=5, LSE_LCOL=13, LSE_RCOL=11, LSE_LLINE=85, LSE_RLINE=124 */ ;   // v:/cpu2908/fpga/machxo2/impl1/sequencer_s.v(128[6:42])
    AND2 I101 (.A(N_21), .B(UM[19]), .Z(XD[12])) /* synthesis syn_instantiated=1, LSE_LINE_FILE_ID=5, LSE_LCOL=13, LSE_RCOL=11, LSE_LLINE=85, LSE_RLINE=124 */ ;   // v:/cpu2908/fpga/machxo2/impl1/sequencer_s.v(129[6:45])
    AND2 I11 (.A(N_12), .B(S_c_1), .Z(N_2)) /* synthesis syn_instantiated=1, LSE_LINE_FILE_ID=5, LSE_LCOL=13, LSE_RCOL=11, LSE_LLINE=85, LSE_RLINE=124 */ ;   // v:/cpu2908/fpga/machxo2/impl1/sequencer_s.v(130[6:41])
    AND2 I9 (.A(N_13), .B(S_c_0), .Z(N_10)) /* synthesis syn_instantiated=1, LSE_LINE_FILE_ID=5, LSE_LCOL=13, LSE_RCOL=11, LSE_LLINE=85, LSE_RLINE=124 */ ;   // v:/cpu2908/fpga/machxo2/impl1/sequencer_s.v(131[6:41])
    INV I118 (.A(ExDataIn[1]), .Z(N_29)) /* synthesis LSE_LINE_FILE_ID=5, LSE_LCOL=13, LSE_RCOL=11, LSE_LLINE=85, LSE_RLINE=124 */ ;   // v:/cpu2908/fpga/machxo2/sequencer.v(85[13] 124[11])
    INV I119 (.A(ExDataIn[2]), .Z(N_30)) /* synthesis LSE_LINE_FILE_ID=5, LSE_LCOL=13, LSE_RCOL=11, LSE_LLINE=85, LSE_RLINE=124 */ ;   // v:/cpu2908/fpga/machxo2/sequencer.v(85[13] 124[11])
    INV I120 (.A(ExDataIn[4]), .Z(N_42)) /* synthesis LSE_LINE_FILE_ID=5, LSE_LCOL=13, LSE_RCOL=11, LSE_LLINE=85, LSE_RLINE=124 */ ;   // v:/cpu2908/fpga/machxo2/sequencer.v(85[13] 124[11])
    INV I32 (.A(ExDataIn[3]), .Z(N_44)) /* synthesis LSE_LINE_FILE_ID=5, LSE_LCOL=13, LSE_RCOL=11, LSE_LLINE=85, LSE_RLINE=124 */ ;   // v:/cpu2908/fpga/machxo2/sequencer.v(85[13] 124[11])
    INV I111 (.A(N_8), .Z(N_4)) /* synthesis LSE_LINE_FILE_ID=5, LSE_LCOL=13, LSE_RCOL=11, LSE_LLINE=85, LSE_RLINE=124 */ ;   // v:/cpu2908/fpga/machxo2/sequencer.v(85[13] 124[11])
    INV I102 (.A(UM[8]), .Z(N_21)) /* synthesis LSE_LINE_FILE_ID=5, LSE_LCOL=13, LSE_RCOL=11, LSE_LLINE=85, LSE_RLINE=124 */ ;   // v:/cpu2908/fpga/machxo2/sequencer.v(85[13] 124[11])
    INV I51 (.A(N_14), .Z(sig[0])) /* synthesis LSE_LINE_FILE_ID=5, LSE_LCOL=13, LSE_RCOL=11, LSE_LLINE=85, LSE_RLINE=124 */ ;   // v:/cpu2908/fpga/machxo2/sequencer.v(85[13] 124[11])
    INV I50 (.A(N_16), .Z(N_11)) /* synthesis LSE_LINE_FILE_ID=5, LSE_LCOL=13, LSE_RCOL=11, LSE_LLINE=85, LSE_RLINE=124 */ ;   // v:/cpu2908/fpga/machxo2/sequencer.v(85[13] 124[11])
    INV I5 (.A(S_c_0), .Z(N_12)) /* synthesis LSE_LINE_FILE_ID=5, LSE_LCOL=13, LSE_RCOL=11, LSE_LLINE=85, LSE_RLINE=124 */ ;   // v:/cpu2908/fpga/machxo2/sequencer.v(85[13] 124[11])
    INV I6 (.A(S_c_1), .Z(N_13)) /* synthesis LSE_LINE_FILE_ID=5, LSE_LCOL=13, LSE_RCOL=11, LSE_LLINE=85, LSE_RLINE=124 */ ;   // v:/cpu2908/fpga/machxo2/sequencer.v(85[13] 124[11])
    PFUMX i4480 (.BLUT(n4975), .ALUT(n4976), .C0(ExDataIn[2]), .Z(N_35));
    FD1P3AX Bit0 (.D(N_4), .SP(VCC_net), .CK(sig[0]), .Q(S_c_0)) /* synthesis syn_instantiated=1, LSE_LINE_FILE_ID=5, LSE_LCOL=13, LSE_RCOL=11, LSE_LLINE=85, LSE_RLINE=124 */ ;   // v:/cpu2908/fpga/machxo2/impl1/sequencer_s.v(154[9:70])
    defparam Bit0.GSR = "ENABLED";
    LUT4 i4478_3_lut (.A(\sig[43] ), .B(\sig[44] ), .C(ExDataIn[1]), .Z(n4975)) /* synthesis lut_function=(A (B+!(C))+!A (B (C))) */ ;   // v:/cpu2908/fpga/machxo2/sequencer.v(85[13] 124[11])
    defparam i4478_3_lut.init = 16'hcaca;
    LUT4 i4479_3_lut (.A(\sig[46] ), .B(\sig[47] ), .C(ExDataIn[1]), .Z(n4976)) /* synthesis lut_function=(A (B+!(C))+!A (B (C))) */ ;   // v:/cpu2908/fpga/machxo2/sequencer.v(85[13] 124[11])
    defparam i4479_3_lut.init = 16'hcaca;
    register8_U6 tempReg (.subPort({subPort}), .clkE_N_18(clkE_N_18), .ExDataIn({ExDataIn})) /* synthesis syn_module_defined=1 */ ;   // v:/cpu2908/fpga/machxo2/impl1/sequencer_s.v(97[11] 98[39])
    Mux2_1x8 I97 (.ExDataIn({ExDataIn}), .subPort({subPort}), .\sig[92] (sig[92]), 
            .DataInSel1({DataInSel1})) /* synthesis syn_module_defined=1 */ ;   // v:/cpu2908/fpga/machxo2/impl1/sequencer_s.v(116[10] 117[34])
    jccSelector I82 (.\ExDataIn[3] (ExDataIn[3]), .\sig[42] (sig[42]), .\uromIDX_A[3] (uromIDX_A[3]), 
            .\ExDataIn[2] (ExDataIn[2]), .\uromIDX_A[2] (uromIDX_A[2]), 
            .\ExDataIn[1] (ExDataIn[1]), .\uromIDX_A[1] (uromIDX_A[1]), 
            .\ExDataIn[0] (ExDataIn[0]), .\sig[41] (sig[41]), .\uromIDX_A[0] (uromIDX_A[0])) /* synthesis syn_module_defined=1 */ ;   // v:/cpu2908/fpga/machxo2/impl1/sequencer_s.v(101[13] 102[41])
    register32 I62 (.\sig[35] (\sig[35] ), .clkE_N_18(clkE_N_18), .\UM[2] (UM[2]), 
            .\sig[34] (\sig[34] ), .\UM[3] (UM[3]), .\sig[33] (\sig[33] ), 
            .\UM[4] (UM[4]), .\sig[32] (\sig[32] ), .\UM[5] (UM[5]), .\sig[94] (\sig[94] ), 
            .\UM[9] (UM[9]), .\sig[93] (\sig[93] ), .\UM[10] (UM[10]), 
            .\sig[92] (sig[92]), .\UM[11] (UM[11]), .\sig[91] (\sig[91] ), 
            .\UM[12] (UM[12]), .\sig[90] (\sig[90] ), .\UM[13] (UM[13]), 
            .\sig[89] (\sig[89] ), .\XD[17] (XD[17]), .\sig[88] (\sig[88] ), 
            .\UM[15] (UM[15]), .\sig[87] (\sig[87] ), .\UM[16] (UM[16]), 
            .\sig[86] (\sig[86] ), .\UM[17] (UM[17]), .\sig[85] (\sig[85] ), 
            .\UM[18] (UM[18]), .\sig[84] (\sig[84] ), .\XD[12] (XD[12]), 
            .\sig[83] (\sig[83] ), .\UM[20] (UM[20]), .\sig[82] (\sig[82] ), 
            .\UM[21] (UM[21]), .\sig[81] (\sig[81] ), .\UM[22] (UM[22]), 
            .\sig[80] (\sig[80] ), .\UM[23] (UM[23]), .\sig[79] (\sig[79] ), 
            .\UM[24] (UM[24]), .\data_ibus[1] (\data_ibus[1] ), .n7(n7), 
            .\sig[78] (\sig[78] ), .\UM[25] (UM[25]), .\sig[77] (\sig[77] ), 
            .\UM[26] (UM[26]), .\sig[76] (\sig[76] ), .\UM[27] (UM[27]), 
            .\sig[75] (\sig[75] ), .\UM[28] (UM[28]), .\sig[74] (\sig[74] ), 
            .\UM[29] (UM[29]), .\sig[73] (\sig[73] ), .\UM[30] (UM[30]), 
            .\sig[72] (\sig[72] ), .\UM[31] (UM[31]), .\subPort[4] (\subPort[4] ), 
            .\outreg[1] (\outreg[1] ), .\InternalDataBus[4] (\InternalDataBus[4] ), 
            .\addrLo[4] (\addrLo[4] ), .\addrHi[4] (\addrHi[4] ), .n68(n68), 
            .\subPort[4]_adj_87 (\subPort[4]_adj_98 ), .\subPort[4]_adj_88 (\subPort[4]_adj_99 ), 
            .\data_es_bus[5] (data_es_bus[5]), .\outreg[2] (\outreg[2] ), 
            .n5388(n5388), .\subPort[2] (\subPort[2] ), .n1(n1), .\subPort[1] (\subPort[1] ), 
            .n1_adj_89(n1_adj_100), .\subPort[7] (\subPort[7] ), .n1_adj_90(n1_adj_101), 
            .\subPort[0] (\subPort[0] ), .n1_adj_91(n1_adj_102), .\subPort[6] (\subPort[6] ), 
            .n1_adj_92(n1_adj_103), .n5389(n5389), .\data_ibus[4] (\data_ibus[4] ), 
            .\subPort[4]_adj_93 (\subPort[4]_adj_104 ), .\addrLo[3] (\addrLo[3] ), 
            .n5(n5), .\data_es_bus[4] (data_es_bus[4]), .clkQ_c_derived_27_enable_9(clkQ_c_derived_27_enable_9), 
            .clkQ_c_derived_27_enable_5(clkQ_c_derived_27_enable_5), .\subPort[5] (\subPort[5] ), 
            .\data_ibus[6] (\data_ibus[6] ), .n7_adj_94(n7_adj_105), .\data_ibus[7] (\data_ibus[7] ), 
            .n7_adj_95(n7_adj_106), .\data_ibus[2] (\data_ibus[2] ), .n7_adj_96(n7_adj_107), 
            .\data_ibus[0] (\data_ibus[0] ), .n7_adj_97(n7_adj_108)) /* synthesis syn_module_defined=1 */ ;   // v:/cpu2908/fpga/machxo2/impl1/sequencer_s.v(104[12] 105[29])
    Mux2_1x8_U7 I59 (.DataInSel1({DataInSel1}), .\UM[15] (UM[15]), .\UM[8] (UM[8]), 
            .data_es_bus({\data_es_bus[7] , \data_es_bus[6] , data_es_bus[5:4], 
            \data_es_bus[3] , \data_es_bus[2] , \data_es_bus[1] , \data_es_bus[0] }), 
            .\UM[14] (UM[14]), .\UM[16] (UM[16]), .\UM[17] (UM[17]), .\UM[18] (UM[18]), 
            .\UM[19] (UM[19]), .\UM[20] (UM[20]), .\UM[21] (UM[21])) /* synthesis syn_module_defined=1 */ ;   // v:/cpu2908/fpga/machxo2/impl1/sequencer_s.v(112[10] 113[110])
    uromCounter I45 (.CT({CT}), .\sig[4] (sig[4]), .idx({idx}), .\sig[1] (sig[1]), 
            .GND_net(GND_net)) /* synthesis syn_module_defined=1 */ ;   // v:/cpu2908/fpga/machxo2/impl1/sequencer_s.v(106[13] 107[85])
    Mux2_1x8_U8 I33 (.\ExDataIn[6] (ExDataIn[6]), .VCC_net(VCC_net), .N_22(N_22), 
            .uromIDX({uromIDX}), .\ExDataIn[7] (ExDataIn[7]), .\ExDataIn[5] (ExDataIn[5]), 
            .\ExDataIn[4] (ExDataIn[4]), .GND_net(GND_net), .\uromIDX_A[3] (uromIDX_A[3]), 
            .\uromIDX_A[2] (uromIDX_A[2]), .\uromIDX_A[1] (uromIDX_A[1]), 
            .S_c_1(S_c_1), .\uromIDX_A[0] (uromIDX_A[0]), .S_c_0(S_c_0)) /* synthesis syn_module_defined=1 */ ;   // v:/cpu2908/fpga/machxo2/impl1/sequencer_s.v(114[10] 115[110])
    urom_TBL I107 (.uromIDX({uromIDX}), .idx({idx})) /* synthesis NGD_DRC_MASK=1, syn_module_defined=1 */ ;   // v:/cpu2908/fpga/machxo2/impl1/sequencer_s.v(91[10:199])
    uromd I105 (.CT({CT}), .N_28(N_28), .VCC_net(VCC_net), .GND_net(GND_net), 
          .\sig[6] (sig[6]), .\UM[2] (UM[2]), .\UM[3] (UM[3]), .\UM[4] (UM[4]), 
          .\UM[14] (UM[14]), .\UM[15] (UM[15]), .\UM[16] (UM[16]), .\UM[17] (UM[17]), 
          .\UM[18] (UM[18]), .\UM[19] (UM[19]), .\UM[20] (UM[20]), .\UM[21] (UM[21]), 
          .\UM[22] (UM[22]), .\UM[23] (UM[23]), .\UM[24] (UM[24]), .\UM[25] (UM[25]), 
          .\UM[26] (UM[26]), .\UM[27] (UM[27]), .\UM[28] (UM[28]), .\UM[29] (UM[29]), 
          .\UM[30] (UM[30]), .\UM[31] (UM[31]), .\UM[5] (UM[5]), .\UM[8] (UM[8]), 
          .\UM[9] (UM[9]), .\UM[10] (UM[10]), .\UM[11] (UM[11]), .\UM[12] (UM[12]), 
          .\UM[13] (UM[13])) /* synthesis NGD_DRC_MASK=1, syn_module_defined=1 */ ;   // v:/cpu2908/fpga/machxo2/impl1/sequencer_s.v(92[7] 93[248])
    
endmodule
//
// Verilog Description of module register8_U6
//

module register8_U6 (subPort, clkE_N_18, ExDataIn) /* synthesis syn_module_defined=1 */ ;
    output [7:0]subPort;
    input clkE_N_18;
    input [7:0]ExDataIn;
    
    wire clkE_N_18 /* synthesis is_inv_clock=1 */ ;   // v:/cpu2908/fpga/machxo2/top.v(14[14:18])
    
    FD1S3AX R_i7 (.D(ExDataIn[7]), .CK(clkE_N_18), .Q(subPort[7])) /* synthesis LSE_LINE_FILE_ID=6, LSE_LCOL=11, LSE_RCOL=39, LSE_LLINE=97, LSE_RLINE=98 */ ;   // v:/cpu2908/fpga/machxo2/register.v(57[8] 59[4])
    defparam R_i7.GSR = "DISABLED";
    FD1S3AX R_i6 (.D(ExDataIn[6]), .CK(clkE_N_18), .Q(subPort[6])) /* synthesis LSE_LINE_FILE_ID=6, LSE_LCOL=11, LSE_RCOL=39, LSE_LLINE=97, LSE_RLINE=98 */ ;   // v:/cpu2908/fpga/machxo2/register.v(57[8] 59[4])
    defparam R_i6.GSR = "DISABLED";
    FD1S3AX R_i5 (.D(ExDataIn[5]), .CK(clkE_N_18), .Q(subPort[5])) /* synthesis LSE_LINE_FILE_ID=6, LSE_LCOL=11, LSE_RCOL=39, LSE_LLINE=97, LSE_RLINE=98 */ ;   // v:/cpu2908/fpga/machxo2/register.v(57[8] 59[4])
    defparam R_i5.GSR = "DISABLED";
    FD1S3AX R_i4 (.D(ExDataIn[4]), .CK(clkE_N_18), .Q(subPort[4])) /* synthesis LSE_LINE_FILE_ID=6, LSE_LCOL=11, LSE_RCOL=39, LSE_LLINE=97, LSE_RLINE=98 */ ;   // v:/cpu2908/fpga/machxo2/register.v(57[8] 59[4])
    defparam R_i4.GSR = "DISABLED";
    FD1S3AX R_i3 (.D(ExDataIn[3]), .CK(clkE_N_18), .Q(subPort[3])) /* synthesis LSE_LINE_FILE_ID=6, LSE_LCOL=11, LSE_RCOL=39, LSE_LLINE=97, LSE_RLINE=98 */ ;   // v:/cpu2908/fpga/machxo2/register.v(57[8] 59[4])
    defparam R_i3.GSR = "DISABLED";
    FD1S3AX R_i2 (.D(ExDataIn[2]), .CK(clkE_N_18), .Q(subPort[2])) /* synthesis LSE_LINE_FILE_ID=6, LSE_LCOL=11, LSE_RCOL=39, LSE_LLINE=97, LSE_RLINE=98 */ ;   // v:/cpu2908/fpga/machxo2/register.v(57[8] 59[4])
    defparam R_i2.GSR = "DISABLED";
    FD1S3AX R_i1 (.D(ExDataIn[1]), .CK(clkE_N_18), .Q(subPort[1])) /* synthesis LSE_LINE_FILE_ID=6, LSE_LCOL=11, LSE_RCOL=39, LSE_LLINE=97, LSE_RLINE=98 */ ;   // v:/cpu2908/fpga/machxo2/register.v(57[8] 59[4])
    defparam R_i1.GSR = "DISABLED";
    FD1S3AX R_i0 (.D(ExDataIn[0]), .CK(clkE_N_18), .Q(subPort[0])) /* synthesis LSE_LINE_FILE_ID=6, LSE_LCOL=11, LSE_RCOL=39, LSE_LLINE=97, LSE_RLINE=98 */ ;   // v:/cpu2908/fpga/machxo2/register.v(57[8] 59[4])
    defparam R_i0.GSR = "DISABLED";
    
endmodule
//
// Verilog Description of module Mux2_1x8
//

module Mux2_1x8 (ExDataIn, subPort, \sig[92] , DataInSel1) /* synthesis syn_module_defined=1 */ ;
    input [7:0]ExDataIn;
    input [7:0]subPort;
    input \sig[92] ;
    output [7:0]DataInSel1;
    
    
    MUX21 I7 (.D0(ExDataIn[6]), .D1(subPort[6]), .SD(\sig[92] ), .Z(DataInSel1[6])) /* synthesis syn_instantiated=1, LSE_LINE_FILE_ID=6, LSE_LCOL=10, LSE_RCOL=34, LSE_LLINE=116, LSE_RLINE=117 */ ;   // v:/cpu2908/fpga/machxo2/impl1/sequencer_s.v(116[10] 117[34])
    MUX21 I8 (.D0(ExDataIn[7]), .D1(subPort[7]), .SD(\sig[92] ), .Z(DataInSel1[7])) /* synthesis syn_instantiated=1, LSE_LINE_FILE_ID=6, LSE_LCOL=10, LSE_RCOL=34, LSE_LLINE=116, LSE_RLINE=117 */ ;   // v:/cpu2908/fpga/machxo2/impl1/sequencer_s.v(116[10] 117[34])
    MUX21 I6 (.D0(ExDataIn[5]), .D1(subPort[5]), .SD(\sig[92] ), .Z(DataInSel1[5])) /* synthesis syn_instantiated=1, LSE_LINE_FILE_ID=6, LSE_LCOL=10, LSE_RCOL=34, LSE_LLINE=116, LSE_RLINE=117 */ ;   // v:/cpu2908/fpga/machxo2/impl1/sequencer_s.v(116[10] 117[34])
    MUX21 I5 (.D0(ExDataIn[4]), .D1(subPort[4]), .SD(\sig[92] ), .Z(DataInSel1[4])) /* synthesis syn_instantiated=1, LSE_LINE_FILE_ID=6, LSE_LCOL=10, LSE_RCOL=34, LSE_LLINE=116, LSE_RLINE=117 */ ;   // v:/cpu2908/fpga/machxo2/impl1/sequencer_s.v(116[10] 117[34])
    MUX21 I4 (.D0(ExDataIn[3]), .D1(subPort[3]), .SD(\sig[92] ), .Z(DataInSel1[3])) /* synthesis syn_instantiated=1, LSE_LINE_FILE_ID=6, LSE_LCOL=10, LSE_RCOL=34, LSE_LLINE=116, LSE_RLINE=117 */ ;   // v:/cpu2908/fpga/machxo2/impl1/sequencer_s.v(116[10] 117[34])
    MUX21 I3 (.D0(ExDataIn[2]), .D1(subPort[2]), .SD(\sig[92] ), .Z(DataInSel1[2])) /* synthesis syn_instantiated=1, LSE_LINE_FILE_ID=6, LSE_LCOL=10, LSE_RCOL=34, LSE_LLINE=116, LSE_RLINE=117 */ ;   // v:/cpu2908/fpga/machxo2/impl1/sequencer_s.v(116[10] 117[34])
    MUX21 I2 (.D0(ExDataIn[1]), .D1(subPort[1]), .SD(\sig[92] ), .Z(DataInSel1[1])) /* synthesis syn_instantiated=1, LSE_LINE_FILE_ID=6, LSE_LCOL=10, LSE_RCOL=34, LSE_LLINE=116, LSE_RLINE=117 */ ;   // v:/cpu2908/fpga/machxo2/impl1/sequencer_s.v(116[10] 117[34])
    MUX21 I1 (.D0(ExDataIn[0]), .D1(subPort[0]), .SD(\sig[92] ), .Z(DataInSel1[0])) /* synthesis syn_instantiated=1, LSE_LINE_FILE_ID=6, LSE_LCOL=10, LSE_RCOL=34, LSE_LLINE=116, LSE_RLINE=117 */ ;   // v:/cpu2908/fpga/machxo2/impl1/sequencer_s.v(116[10] 117[34])
    
endmodule
//
// Verilog Description of module jccSelector
//

module jccSelector (\ExDataIn[3] , \sig[42] , \uromIDX_A[3] , \ExDataIn[2] , 
            \uromIDX_A[2] , \ExDataIn[1] , \uromIDX_A[1] , \ExDataIn[0] , 
            \sig[41] , \uromIDX_A[0] ) /* synthesis syn_module_defined=1 */ ;
    input \ExDataIn[3] ;
    input \sig[42] ;
    output \uromIDX_A[3] ;
    input \ExDataIn[2] ;
    output \uromIDX_A[2] ;
    input \ExDataIn[1] ;
    output \uromIDX_A[1] ;
    input \ExDataIn[0] ;
    input \sig[41] ;
    output \uromIDX_A[0] ;
    
    
    LUT4 i2658_2_lut (.A(\ExDataIn[3] ), .B(\sig[42] ), .Z(\uromIDX_A[3] )) /* synthesis lut_function=(A+(B)) */ ;   // v:/cpu2908/fpga/machxo2/sequencer.v(178[15] 179[68])
    defparam i2658_2_lut.init = 16'heeee;
    LUT4 i2659_2_lut (.A(\ExDataIn[2] ), .B(\sig[42] ), .Z(\uromIDX_A[2] )) /* synthesis lut_function=(A+(B)) */ ;   // v:/cpu2908/fpga/machxo2/sequencer.v(178[15] 179[68])
    defparam i2659_2_lut.init = 16'heeee;
    LUT4 i2660_2_lut (.A(\ExDataIn[1] ), .B(\sig[42] ), .Z(\uromIDX_A[1] )) /* synthesis lut_function=(A+(B)) */ ;   // v:/cpu2908/fpga/machxo2/sequencer.v(178[15] 179[68])
    defparam i2660_2_lut.init = 16'heeee;
    LUT4 noJump_I_0_3_lut (.A(\ExDataIn[0] ), .B(\sig[41] ), .C(\sig[42] ), 
         .Z(\uromIDX_A[0] )) /* synthesis lut_function=(A (B+!(C))+!A (B (C))) */ ;   // v:/cpu2908/fpga/machxo2/sequencer.v(178[15] 179[68])
    defparam noJump_I_0_3_lut.init = 16'hcaca;
    
endmodule
//
// Verilog Description of module register32
//

module register32 (\sig[35] , clkE_N_18, \UM[2] , \sig[34] , \UM[3] , 
            \sig[33] , \UM[4] , \sig[32] , \UM[5] , \sig[94] , \UM[9] , 
            \sig[93] , \UM[10] , \sig[92] , \UM[11] , \sig[91] , \UM[12] , 
            \sig[90] , \UM[13] , \sig[89] , \XD[17] , \sig[88] , \UM[15] , 
            \sig[87] , \UM[16] , \sig[86] , \UM[17] , \sig[85] , \UM[18] , 
            \sig[84] , \XD[12] , \sig[83] , \UM[20] , \sig[82] , \UM[21] , 
            \sig[81] , \UM[22] , \sig[80] , \UM[23] , \sig[79] , \UM[24] , 
            \data_ibus[1] , n7, \sig[78] , \UM[25] , \sig[77] , \UM[26] , 
            \sig[76] , \UM[27] , \sig[75] , \UM[28] , \sig[74] , \UM[29] , 
            \sig[73] , \UM[30] , \sig[72] , \UM[31] , \subPort[4] , 
            \outreg[1] , \InternalDataBus[4] , \addrLo[4] , \addrHi[4] , 
            n68, \subPort[4]_adj_87 , \subPort[4]_adj_88 , \data_es_bus[5] , 
            \outreg[2] , n5388, \subPort[2] , n1, \subPort[1] , n1_adj_89, 
            \subPort[7] , n1_adj_90, \subPort[0] , n1_adj_91, \subPort[6] , 
            n1_adj_92, n5389, \data_ibus[4] , \subPort[4]_adj_93 , \addrLo[3] , 
            n5, \data_es_bus[4] , clkQ_c_derived_27_enable_9, clkQ_c_derived_27_enable_5, 
            \subPort[5] , \data_ibus[6] , n7_adj_94, \data_ibus[7] , 
            n7_adj_95, \data_ibus[2] , n7_adj_96, \data_ibus[0] , n7_adj_97) /* synthesis syn_module_defined=1 */ ;
    output \sig[35] ;
    input clkE_N_18;
    input \UM[2] ;
    output \sig[34] ;
    input \UM[3] ;
    output \sig[33] ;
    input \UM[4] ;
    output \sig[32] ;
    input \UM[5] ;
    output \sig[94] ;
    input \UM[9] ;
    output \sig[93] ;
    input \UM[10] ;
    output \sig[92] ;
    input \UM[11] ;
    output \sig[91] ;
    input \UM[12] ;
    output \sig[90] ;
    input \UM[13] ;
    output \sig[89] ;
    input \XD[17] ;
    output \sig[88] ;
    input \UM[15] ;
    output \sig[87] ;
    input \UM[16] ;
    output \sig[86] ;
    input \UM[17] ;
    output \sig[85] ;
    input \UM[18] ;
    output \sig[84] ;
    input \XD[12] ;
    output \sig[83] ;
    input \UM[20] ;
    output \sig[82] ;
    input \UM[21] ;
    output \sig[81] ;
    input \UM[22] ;
    output \sig[80] ;
    input \UM[23] ;
    output \sig[79] ;
    input \UM[24] ;
    input \data_ibus[1] ;
    output n7;
    output \sig[78] ;
    input \UM[25] ;
    output \sig[77] ;
    input \UM[26] ;
    output \sig[76] ;
    input \UM[27] ;
    output \sig[75] ;
    input \UM[28] ;
    output \sig[74] ;
    input \UM[29] ;
    output \sig[73] ;
    input \UM[30] ;
    output \sig[72] ;
    input \UM[31] ;
    input \subPort[4] ;
    output \outreg[1] ;
    output \InternalDataBus[4] ;
    input \addrLo[4] ;
    input \addrHi[4] ;
    output n68;
    input \subPort[4]_adj_87 ;
    input \subPort[4]_adj_88 ;
    input \data_es_bus[5] ;
    output \outreg[2] ;
    output n5388;
    input \subPort[2] ;
    output n1;
    input \subPort[1] ;
    output n1_adj_89;
    input \subPort[7] ;
    output n1_adj_90;
    input \subPort[0] ;
    output n1_adj_91;
    input \subPort[6] ;
    output n1_adj_92;
    output n5389;
    input \data_ibus[4] ;
    input \subPort[4]_adj_93 ;
    input \addrLo[3] ;
    output n5;
    input \data_es_bus[4] ;
    output clkQ_c_derived_27_enable_9;
    output clkQ_c_derived_27_enable_5;
    input \subPort[5] ;
    input \data_ibus[6] ;
    output n7_adj_94;
    input \data_ibus[7] ;
    output n7_adj_95;
    input \data_ibus[2] ;
    output n7_adj_96;
    input \data_ibus[0] ;
    output n7_adj_97;
    
    wire clkE_N_18 /* synthesis is_inv_clock=1 */ ;   // v:/cpu2908/fpga/machxo2/top.v(14[14:18])
    
    wire n5452, n5416, n5451, n73, n84, n5450, n5414, n5415;
    
    FD1S3AX R_i27 (.D(\UM[2] ), .CK(clkE_N_18), .Q(\sig[35] )) /* synthesis LSE_LINE_FILE_ID=6, LSE_LCOL=12, LSE_RCOL=29, LSE_LLINE=104, LSE_RLINE=105 */ ;   // v:/cpu2908/fpga/machxo2/register.v(133[7] 135[5])
    defparam R_i27.GSR = "ENABLED";
    FD1S3AX R_i26 (.D(\UM[3] ), .CK(clkE_N_18), .Q(\sig[34] )) /* synthesis LSE_LINE_FILE_ID=6, LSE_LCOL=12, LSE_RCOL=29, LSE_LLINE=104, LSE_RLINE=105 */ ;   // v:/cpu2908/fpga/machxo2/register.v(133[7] 135[5])
    defparam R_i26.GSR = "ENABLED";
    FD1S3AX R_i25 (.D(\UM[4] ), .CK(clkE_N_18), .Q(\sig[33] )) /* synthesis LSE_LINE_FILE_ID=6, LSE_LCOL=12, LSE_RCOL=29, LSE_LLINE=104, LSE_RLINE=105 */ ;   // v:/cpu2908/fpga/machxo2/register.v(133[7] 135[5])
    defparam R_i25.GSR = "ENABLED";
    FD1S3AX R_i24 (.D(\UM[5] ), .CK(clkE_N_18), .Q(\sig[32] )) /* synthesis LSE_LINE_FILE_ID=6, LSE_LCOL=12, LSE_RCOL=29, LSE_LLINE=104, LSE_RLINE=105 */ ;   // v:/cpu2908/fpga/machxo2/register.v(133[7] 135[5])
    defparam R_i24.GSR = "ENABLED";
    FD1S3AX R_i23 (.D(\UM[9] ), .CK(clkE_N_18), .Q(\sig[94] )) /* synthesis LSE_LINE_FILE_ID=6, LSE_LCOL=12, LSE_RCOL=29, LSE_LLINE=104, LSE_RLINE=105 */ ;   // v:/cpu2908/fpga/machxo2/register.v(133[7] 135[5])
    defparam R_i23.GSR = "ENABLED";
    FD1S3AX R_i22 (.D(\UM[10] ), .CK(clkE_N_18), .Q(\sig[93] )) /* synthesis LSE_LINE_FILE_ID=6, LSE_LCOL=12, LSE_RCOL=29, LSE_LLINE=104, LSE_RLINE=105 */ ;   // v:/cpu2908/fpga/machxo2/register.v(133[7] 135[5])
    defparam R_i22.GSR = "ENABLED";
    FD1S3AX R_i21 (.D(\UM[11] ), .CK(clkE_N_18), .Q(\sig[92] )) /* synthesis LSE_LINE_FILE_ID=6, LSE_LCOL=12, LSE_RCOL=29, LSE_LLINE=104, LSE_RLINE=105 */ ;   // v:/cpu2908/fpga/machxo2/register.v(133[7] 135[5])
    defparam R_i21.GSR = "ENABLED";
    FD1S3AX R_i20 (.D(\UM[12] ), .CK(clkE_N_18), .Q(\sig[91] )) /* synthesis LSE_LINE_FILE_ID=6, LSE_LCOL=12, LSE_RCOL=29, LSE_LLINE=104, LSE_RLINE=105 */ ;   // v:/cpu2908/fpga/machxo2/register.v(133[7] 135[5])
    defparam R_i20.GSR = "ENABLED";
    FD1S3AX R_i19 (.D(\UM[13] ), .CK(clkE_N_18), .Q(\sig[90] )) /* synthesis LSE_LINE_FILE_ID=6, LSE_LCOL=12, LSE_RCOL=29, LSE_LLINE=104, LSE_RLINE=105 */ ;   // v:/cpu2908/fpga/machxo2/register.v(133[7] 135[5])
    defparam R_i19.GSR = "ENABLED";
    FD1S3AX R_i18 (.D(\XD[17] ), .CK(clkE_N_18), .Q(\sig[89] )) /* synthesis LSE_LINE_FILE_ID=6, LSE_LCOL=12, LSE_RCOL=29, LSE_LLINE=104, LSE_RLINE=105 */ ;   // v:/cpu2908/fpga/machxo2/register.v(133[7] 135[5])
    defparam R_i18.GSR = "ENABLED";
    FD1S3AX R_i17 (.D(\UM[15] ), .CK(clkE_N_18), .Q(\sig[88] )) /* synthesis LSE_LINE_FILE_ID=6, LSE_LCOL=12, LSE_RCOL=29, LSE_LLINE=104, LSE_RLINE=105 */ ;   // v:/cpu2908/fpga/machxo2/register.v(133[7] 135[5])
    defparam R_i17.GSR = "ENABLED";
    FD1S3AX R_i16 (.D(\UM[16] ), .CK(clkE_N_18), .Q(\sig[87] )) /* synthesis LSE_LINE_FILE_ID=6, LSE_LCOL=12, LSE_RCOL=29, LSE_LLINE=104, LSE_RLINE=105 */ ;   // v:/cpu2908/fpga/machxo2/register.v(133[7] 135[5])
    defparam R_i16.GSR = "ENABLED";
    FD1S3AX R_i15 (.D(\UM[17] ), .CK(clkE_N_18), .Q(\sig[86] )) /* synthesis LSE_LINE_FILE_ID=6, LSE_LCOL=12, LSE_RCOL=29, LSE_LLINE=104, LSE_RLINE=105 */ ;   // v:/cpu2908/fpga/machxo2/register.v(133[7] 135[5])
    defparam R_i15.GSR = "ENABLED";
    FD1S3AX R_i14 (.D(\UM[18] ), .CK(clkE_N_18), .Q(\sig[85] )) /* synthesis LSE_LINE_FILE_ID=6, LSE_LCOL=12, LSE_RCOL=29, LSE_LLINE=104, LSE_RLINE=105 */ ;   // v:/cpu2908/fpga/machxo2/register.v(133[7] 135[5])
    defparam R_i14.GSR = "ENABLED";
    FD1S3AX R_i13 (.D(\XD[12] ), .CK(clkE_N_18), .Q(\sig[84] )) /* synthesis LSE_LINE_FILE_ID=6, LSE_LCOL=12, LSE_RCOL=29, LSE_LLINE=104, LSE_RLINE=105 */ ;   // v:/cpu2908/fpga/machxo2/register.v(133[7] 135[5])
    defparam R_i13.GSR = "ENABLED";
    FD1S3AX R_i12 (.D(\UM[20] ), .CK(clkE_N_18), .Q(\sig[83] )) /* synthesis LSE_LINE_FILE_ID=6, LSE_LCOL=12, LSE_RCOL=29, LSE_LLINE=104, LSE_RLINE=105 */ ;   // v:/cpu2908/fpga/machxo2/register.v(133[7] 135[5])
    defparam R_i12.GSR = "ENABLED";
    FD1S3AX R_i11 (.D(\UM[21] ), .CK(clkE_N_18), .Q(\sig[82] )) /* synthesis LSE_LINE_FILE_ID=6, LSE_LCOL=12, LSE_RCOL=29, LSE_LLINE=104, LSE_RLINE=105 */ ;   // v:/cpu2908/fpga/machxo2/register.v(133[7] 135[5])
    defparam R_i11.GSR = "ENABLED";
    FD1S3AX R_i10 (.D(\UM[22] ), .CK(clkE_N_18), .Q(\sig[81] )) /* synthesis LSE_LINE_FILE_ID=6, LSE_LCOL=12, LSE_RCOL=29, LSE_LLINE=104, LSE_RLINE=105 */ ;   // v:/cpu2908/fpga/machxo2/register.v(133[7] 135[5])
    defparam R_i10.GSR = "ENABLED";
    FD1S3AX R_i9 (.D(\UM[23] ), .CK(clkE_N_18), .Q(\sig[80] )) /* synthesis LSE_LINE_FILE_ID=6, LSE_LCOL=12, LSE_RCOL=29, LSE_LLINE=104, LSE_RLINE=105 */ ;   // v:/cpu2908/fpga/machxo2/register.v(133[7] 135[5])
    defparam R_i9.GSR = "ENABLED";
    FD1S3AX R_i8 (.D(\UM[24] ), .CK(clkE_N_18), .Q(\sig[79] )) /* synthesis LSE_LINE_FILE_ID=6, LSE_LCOL=12, LSE_RCOL=29, LSE_LLINE=104, LSE_RLINE=105 */ ;   // v:/cpu2908/fpga/machxo2/register.v(133[7] 135[5])
    defparam R_i8.GSR = "ENABLED";
    LUT4 Select_249_i7_2_lut_3_lut_4_lut (.A(\sig[80] ), .B(\sig[81] ), 
         .C(\data_ibus[1] ), .D(\sig[79] ), .Z(n7)) /* synthesis lut_function=(A (B (C (D)))) */ ;   // v:/cpu2908/fpga/machxo2/core.v(20[21:24])
    defparam Select_249_i7_2_lut_3_lut_4_lut.init = 16'h8000;
    FD1S3AX R_i7 (.D(\UM[25] ), .CK(clkE_N_18), .Q(\sig[78] )) /* synthesis LSE_LINE_FILE_ID=6, LSE_LCOL=12, LSE_RCOL=29, LSE_LLINE=104, LSE_RLINE=105 */ ;   // v:/cpu2908/fpga/machxo2/register.v(133[7] 135[5])
    defparam R_i7.GSR = "ENABLED";
    FD1S3AX R_i6 (.D(\UM[26] ), .CK(clkE_N_18), .Q(\sig[77] )) /* synthesis LSE_LINE_FILE_ID=6, LSE_LCOL=12, LSE_RCOL=29, LSE_LLINE=104, LSE_RLINE=105 */ ;   // v:/cpu2908/fpga/machxo2/register.v(133[7] 135[5])
    defparam R_i6.GSR = "ENABLED";
    FD1S3AX R_i5 (.D(\UM[27] ), .CK(clkE_N_18), .Q(\sig[76] )) /* synthesis LSE_LINE_FILE_ID=6, LSE_LCOL=12, LSE_RCOL=29, LSE_LLINE=104, LSE_RLINE=105 */ ;   // v:/cpu2908/fpga/machxo2/register.v(133[7] 135[5])
    defparam R_i5.GSR = "ENABLED";
    FD1S3AX R_i4 (.D(\UM[28] ), .CK(clkE_N_18), .Q(\sig[75] )) /* synthesis LSE_LINE_FILE_ID=6, LSE_LCOL=12, LSE_RCOL=29, LSE_LLINE=104, LSE_RLINE=105 */ ;   // v:/cpu2908/fpga/machxo2/register.v(133[7] 135[5])
    defparam R_i4.GSR = "ENABLED";
    FD1S3AX R_i3 (.D(\UM[29] ), .CK(clkE_N_18), .Q(\sig[74] )) /* synthesis LSE_LINE_FILE_ID=6, LSE_LCOL=12, LSE_RCOL=29, LSE_LLINE=104, LSE_RLINE=105 */ ;   // v:/cpu2908/fpga/machxo2/register.v(133[7] 135[5])
    defparam R_i3.GSR = "ENABLED";
    FD1S3AX R_i2 (.D(\UM[30] ), .CK(clkE_N_18), .Q(\sig[73] )) /* synthesis LSE_LINE_FILE_ID=6, LSE_LCOL=12, LSE_RCOL=29, LSE_LLINE=104, LSE_RLINE=105 */ ;   // v:/cpu2908/fpga/machxo2/register.v(133[7] 135[5])
    defparam R_i2.GSR = "ENABLED";
    FD1S3AX R_i1 (.D(\UM[31] ), .CK(clkE_N_18), .Q(\sig[72] )) /* synthesis LSE_LINE_FILE_ID=6, LSE_LCOL=12, LSE_RCOL=29, LSE_LLINE=104, LSE_RLINE=105 */ ;   // v:/cpu2908/fpga/machxo2/register.v(133[7] 135[5])
    defparam R_i1.GSR = "ENABLED";
    LUT4 i6_4_lut (.A(\subPort[4] ), .B(n5452), .C(n5416), .D(\outreg[1] ), 
         .Z(\InternalDataBus[4] )) /* synthesis lut_function=(A (B+(C+(D)))+!A (B+(C))) */ ;   // v:/cpu2908/fpga/machxo2/core.v(20[21:24])
    defparam i6_4_lut.init = 16'hfefc;
    LUT4 i5_4_lut_then_4_lut (.A(\addrLo[4] ), .B(\addrHi[4] ), .C(\sig[80] ), 
         .D(\sig[79] ), .Z(n5451)) /* synthesis lut_function=(!(A (B (C)+!B (C+(D)))+!A ((C+!(D))+!B))) */ ;   // v:/cpu2908/fpga/machxo2/core.v(20[21:24])
    defparam i5_4_lut_then_4_lut.init = 16'h0c0a;
    PFUMX i71 (.BLUT(n73), .ALUT(n84), .C0(\sig[79] ), .Z(n68));
    LUT4 i5_4_lut_else_4_lut (.A(\subPort[4]_adj_87 ), .B(\subPort[4]_adj_88 ), 
         .C(\sig[80] ), .D(\sig[79] ), .Z(n5450)) /* synthesis lut_function=(!(A (B (D)+!B (C+(D)))+!A (((D)+!C)+!B))) */ ;   // v:/cpu2908/fpga/machxo2/core.v(20[21:24])
    defparam i5_4_lut_else_4_lut.init = 16'h00ca;
    LUT4 i1_2_lut_3_lut (.A(\sig[80] ), .B(\sig[81] ), .C(\data_es_bus[5] ), 
         .Z(n73)) /* synthesis lut_function=(A (B (C))) */ ;   // v:/cpu2908/fpga/machxo2/core.v(20[21:24])
    defparam i1_2_lut_3_lut.init = 16'h8080;
    LUT4 i1_2_lut_3_lut_adj_98 (.A(\sig[80] ), .B(\sig[81] ), .C(\sig[79] ), 
         .Z(\outreg[2] )) /* synthesis lut_function=(!((B+(C))+!A)) */ ;   // v:/cpu2908/fpga/machxo2/register.v(133[7] 135[5])
    defparam i1_2_lut_3_lut_adj_98.init = 16'h0202;
    LUT4 i1_2_lut_rep_100_3_lut (.A(\sig[80] ), .B(\sig[81] ), .C(\sig[79] ), 
         .Z(n5388)) /* synthesis lut_function=(A+(B+(C))) */ ;
    defparam i1_2_lut_rep_100_3_lut.init = 16'hfefe;
    LUT4 Select_248_i1_2_lut_3_lut_4_lut (.A(\sig[80] ), .B(\sig[81] ), 
         .C(\subPort[2] ), .D(\sig[79] ), .Z(n1)) /* synthesis lut_function=(!(A+(B+((D)+!C)))) */ ;
    defparam Select_248_i1_2_lut_3_lut_4_lut.init = 16'h0010;
    LUT4 Select_249_i1_2_lut_3_lut_4_lut (.A(\sig[80] ), .B(\sig[81] ), 
         .C(\subPort[1] ), .D(\sig[79] ), .Z(n1_adj_89)) /* synthesis lut_function=(!(A+(B+((D)+!C)))) */ ;
    defparam Select_249_i1_2_lut_3_lut_4_lut.init = 16'h0010;
    LUT4 Select_243_i1_2_lut_3_lut_4_lut (.A(\sig[80] ), .B(\sig[81] ), 
         .C(\subPort[7] ), .D(\sig[79] ), .Z(n1_adj_90)) /* synthesis lut_function=(!(A+(B+((D)+!C)))) */ ;
    defparam Select_243_i1_2_lut_3_lut_4_lut.init = 16'h0010;
    LUT4 i1_2_lut_3_lut_adj_99 (.A(\sig[80] ), .B(\sig[81] ), .C(\sig[79] ), 
         .Z(\outreg[1] )) /* synthesis lut_function=(!(A+(B+!(C)))) */ ;
    defparam i1_2_lut_3_lut_adj_99.init = 16'h1010;
    LUT4 Select_250_i1_2_lut_3_lut_4_lut (.A(\sig[80] ), .B(\sig[81] ), 
         .C(\subPort[0] ), .D(\sig[79] ), .Z(n1_adj_91)) /* synthesis lut_function=(!(A+(B+((D)+!C)))) */ ;
    defparam Select_250_i1_2_lut_3_lut_4_lut.init = 16'h0010;
    LUT4 Select_244_i1_2_lut_3_lut_4_lut (.A(\sig[80] ), .B(\sig[81] ), 
         .C(\subPort[6] ), .D(\sig[79] ), .Z(n1_adj_92)) /* synthesis lut_function=(!(A+(B+((D)+!C)))) */ ;
    defparam Select_244_i1_2_lut_3_lut_4_lut.init = 16'h0010;
    LUT4 i1_2_lut_rep_101_3_lut (.A(\sig[81] ), .B(\sig[80] ), .C(\sig[79] ), 
         .Z(n5389)) /* synthesis lut_function=(!((B+(C))+!A)) */ ;   // v:/cpu2908/fpga/machxo2/register.v(133[7] 135[5])
    defparam i1_2_lut_rep_101_3_lut.init = 16'h0202;
    PFUMX i4717 (.BLUT(n5414), .ALUT(n5415), .C0(\sig[79] ), .Z(n5416));
    LUT4 i1_3_lut_4_lut_then_4_lut (.A(\sig[81] ), .B(\sig[80] ), .C(\data_ibus[4] ), 
         .D(\subPort[4]_adj_93 ), .Z(n5415)) /* synthesis lut_function=(A (B (C))+!A (B (D))) */ ;   // v:/cpu2908/fpga/machxo2/register.v(133[7] 135[5])
    defparam i1_3_lut_4_lut_then_4_lut.init = 16'hc480;
    LUT4 Select_247_i5_2_lut_3_lut_4_lut (.A(\sig[81] ), .B(\sig[80] ), 
         .C(\addrLo[3] ), .D(\sig[79] ), .Z(n5)) /* synthesis lut_function=(!((B+((D)+!C))+!A)) */ ;   // v:/cpu2908/fpga/machxo2/register.v(133[7] 135[5])
    defparam Select_247_i5_2_lut_3_lut_4_lut.init = 16'h0020;
    LUT4 i1_3_lut_4_lut_else_4_lut (.A(\sig[81] ), .B(\sig[80] ), .C(\data_es_bus[4] ), 
         .Z(n5414)) /* synthesis lut_function=(A (B (C))) */ ;   // v:/cpu2908/fpga/machxo2/register.v(133[7] 135[5])
    defparam i1_3_lut_4_lut_else_4_lut.init = 16'h8080;
    LUT4 i414_1_lut_rep_109 (.A(\sig[89] ), .Z(clkQ_c_derived_27_enable_9)) /* synthesis lut_function=(!(A)) */ ;   // v:/cpu2908/fpga/machxo2/register.v(133[7] 135[5])
    defparam i414_1_lut_rep_109.init = 16'h5555;
    LUT4 i415_2_lut_2_lut (.A(\sig[89] ), .B(\sig[88] ), .Z(clkQ_c_derived_27_enable_5)) /* synthesis lut_function=(!(A+!(B))) */ ;   // v:/cpu2908/fpga/machxo2/register.v(133[7] 135[5])
    defparam i415_2_lut_2_lut.init = 16'h4444;
    LUT4 i1_2_lut_3_lut_adj_100 (.A(\sig[80] ), .B(\sig[81] ), .C(\subPort[5] ), 
         .Z(n84)) /* synthesis lut_function=(!((B+!(C))+!A)) */ ;   // v:/cpu2908/fpga/machxo2/register.v(133[7] 135[5])
    defparam i1_2_lut_3_lut_adj_100.init = 16'h2020;
    LUT4 Select_244_i7_2_lut_3_lut_4_lut (.A(\sig[80] ), .B(\sig[81] ), 
         .C(\data_ibus[6] ), .D(\sig[79] ), .Z(n7_adj_94)) /* synthesis lut_function=(A (B (C (D)))) */ ;   // v:/cpu2908/fpga/machxo2/core.v(20[21:24])
    defparam Select_244_i7_2_lut_3_lut_4_lut.init = 16'h8000;
    PFUMX i4741 (.BLUT(n5450), .ALUT(n5451), .C0(\sig[81] ), .Z(n5452));
    LUT4 Select_243_i7_2_lut_3_lut_4_lut (.A(\sig[80] ), .B(\sig[81] ), 
         .C(\data_ibus[7] ), .D(\sig[79] ), .Z(n7_adj_95)) /* synthesis lut_function=(A (B (C (D)))) */ ;   // v:/cpu2908/fpga/machxo2/core.v(20[21:24])
    defparam Select_243_i7_2_lut_3_lut_4_lut.init = 16'h8000;
    LUT4 Select_248_i7_2_lut_3_lut_4_lut (.A(\sig[80] ), .B(\sig[81] ), 
         .C(\data_ibus[2] ), .D(\sig[79] ), .Z(n7_adj_96)) /* synthesis lut_function=(A (B (C (D)))) */ ;   // v:/cpu2908/fpga/machxo2/core.v(20[21:24])
    defparam Select_248_i7_2_lut_3_lut_4_lut.init = 16'h8000;
    LUT4 Select_250_i7_2_lut_3_lut_4_lut (.A(\sig[80] ), .B(\sig[81] ), 
         .C(\data_ibus[0] ), .D(\sig[79] ), .Z(n7_adj_97)) /* synthesis lut_function=(A (B (C (D)))) */ ;   // v:/cpu2908/fpga/machxo2/core.v(20[21:24])
    defparam Select_250_i7_2_lut_3_lut_4_lut.init = 16'h8000;
    
endmodule
//
// Verilog Description of module Mux2_1x8_U7
//

module Mux2_1x8_U7 (DataInSel1, \UM[15] , \UM[8] , data_es_bus, \UM[14] , 
            \UM[16] , \UM[17] , \UM[18] , \UM[19] , \UM[20] , \UM[21] ) /* synthesis syn_module_defined=1 */ ;
    input [7:0]DataInSel1;
    input \UM[15] ;
    input \UM[8] ;
    output [7:0]data_es_bus;
    input \UM[14] ;
    input \UM[16] ;
    input \UM[17] ;
    input \UM[18] ;
    input \UM[19] ;
    input \UM[20] ;
    input \UM[21] ;
    
    
    MUX21 I7 (.D0(DataInSel1[6]), .D1(\UM[15] ), .SD(\UM[8] ), .Z(data_es_bus[6])) /* synthesis syn_instantiated=1, LSE_LINE_FILE_ID=6, LSE_LCOL=10, LSE_RCOL=110, LSE_LLINE=112, LSE_RLINE=113 */ ;   // v:/cpu2908/fpga/machxo2/impl1/sequencer_s.v(112[10] 113[110])
    MUX21 I8 (.D0(DataInSel1[7]), .D1(\UM[14] ), .SD(\UM[8] ), .Z(data_es_bus[7])) /* synthesis syn_instantiated=1, LSE_LINE_FILE_ID=6, LSE_LCOL=10, LSE_RCOL=110, LSE_LLINE=112, LSE_RLINE=113 */ ;   // v:/cpu2908/fpga/machxo2/impl1/sequencer_s.v(112[10] 113[110])
    MUX21 I6 (.D0(DataInSel1[5]), .D1(\UM[16] ), .SD(\UM[8] ), .Z(data_es_bus[5])) /* synthesis syn_instantiated=1, LSE_LINE_FILE_ID=6, LSE_LCOL=10, LSE_RCOL=110, LSE_LLINE=112, LSE_RLINE=113 */ ;   // v:/cpu2908/fpga/machxo2/impl1/sequencer_s.v(112[10] 113[110])
    MUX21 I5 (.D0(DataInSel1[4]), .D1(\UM[17] ), .SD(\UM[8] ), .Z(data_es_bus[4])) /* synthesis syn_instantiated=1, LSE_LINE_FILE_ID=6, LSE_LCOL=10, LSE_RCOL=110, LSE_LLINE=112, LSE_RLINE=113 */ ;   // v:/cpu2908/fpga/machxo2/impl1/sequencer_s.v(112[10] 113[110])
    MUX21 I4 (.D0(DataInSel1[3]), .D1(\UM[18] ), .SD(\UM[8] ), .Z(data_es_bus[3])) /* synthesis syn_instantiated=1, LSE_LINE_FILE_ID=6, LSE_LCOL=10, LSE_RCOL=110, LSE_LLINE=112, LSE_RLINE=113 */ ;   // v:/cpu2908/fpga/machxo2/impl1/sequencer_s.v(112[10] 113[110])
    MUX21 I3 (.D0(DataInSel1[2]), .D1(\UM[19] ), .SD(\UM[8] ), .Z(data_es_bus[2])) /* synthesis syn_instantiated=1, LSE_LINE_FILE_ID=6, LSE_LCOL=10, LSE_RCOL=110, LSE_LLINE=112, LSE_RLINE=113 */ ;   // v:/cpu2908/fpga/machxo2/impl1/sequencer_s.v(112[10] 113[110])
    MUX21 I2 (.D0(DataInSel1[1]), .D1(\UM[20] ), .SD(\UM[8] ), .Z(data_es_bus[1])) /* synthesis syn_instantiated=1, LSE_LINE_FILE_ID=6, LSE_LCOL=10, LSE_RCOL=110, LSE_LLINE=112, LSE_RLINE=113 */ ;   // v:/cpu2908/fpga/machxo2/impl1/sequencer_s.v(112[10] 113[110])
    MUX21 I1 (.D0(DataInSel1[0]), .D1(\UM[21] ), .SD(\UM[8] ), .Z(data_es_bus[0])) /* synthesis syn_instantiated=1, LSE_LINE_FILE_ID=6, LSE_LCOL=10, LSE_RCOL=110, LSE_LLINE=112, LSE_RLINE=113 */ ;   // v:/cpu2908/fpga/machxo2/impl1/sequencer_s.v(112[10] 113[110])
    
endmodule
//
// Verilog Description of module uromCounter
//
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
